hcmusthinhcode2k2/WeatherStation_Thesis/Docs/Images/1b0e72e8-8784-49f9-9e78-873ca0ad76dc.png

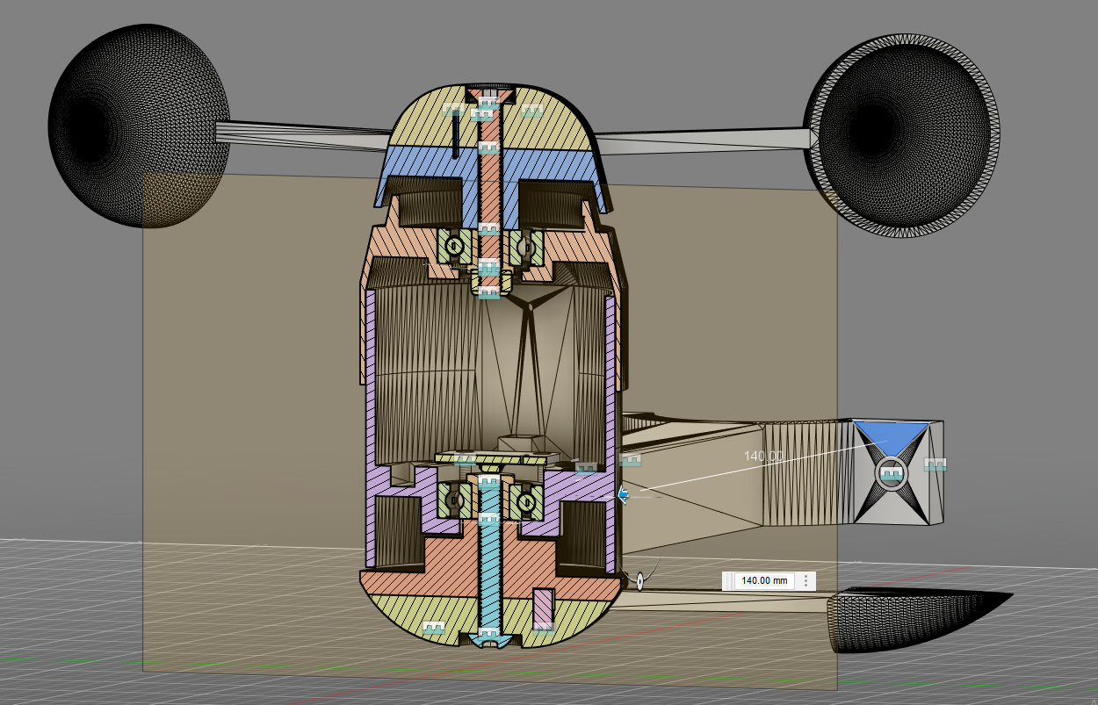
Docs/Images/1b0e72e8-8784-49f9-9e78-873ca0ad76dc.png
