hcmusthinhcode2k2/WeatherStation_Thesis/Docs/Images/2f302a85-7f2c-48bd-ab72-bc9634dedcbf.png

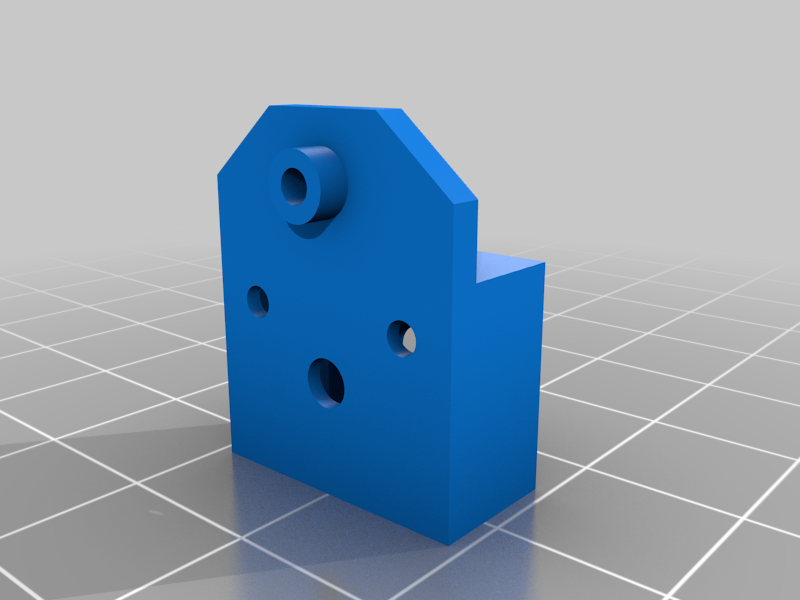
Docs/Images/2f302a85-7f2c-48bd-ab72-bc9634dedcbf.png
