hcmusthinhcode2k2/WeatherStation_Thesis/Docs/Images/3e30936f-f37a-4110-baf6-09b9fe7c85cc.png

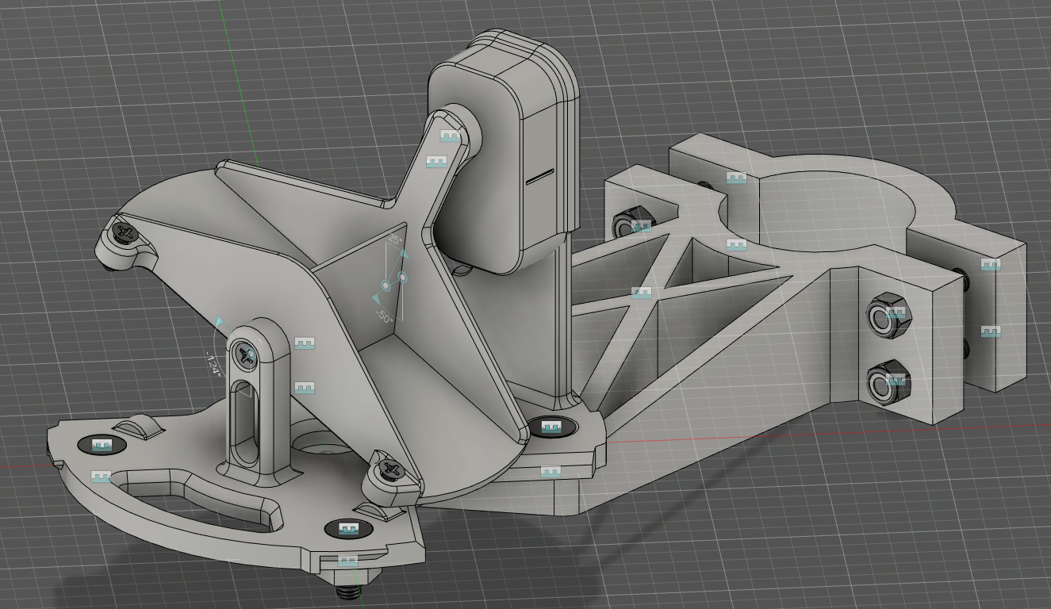
Docs/Images/3e30936f-f37a-4110-baf6-09b9fe7c85cc.png
