hcmusthinhcode2k2/WeatherStation_Thesis/Docs/Images/6b6d25d0-493b-4c5d-b1c7-931fbae90489.png

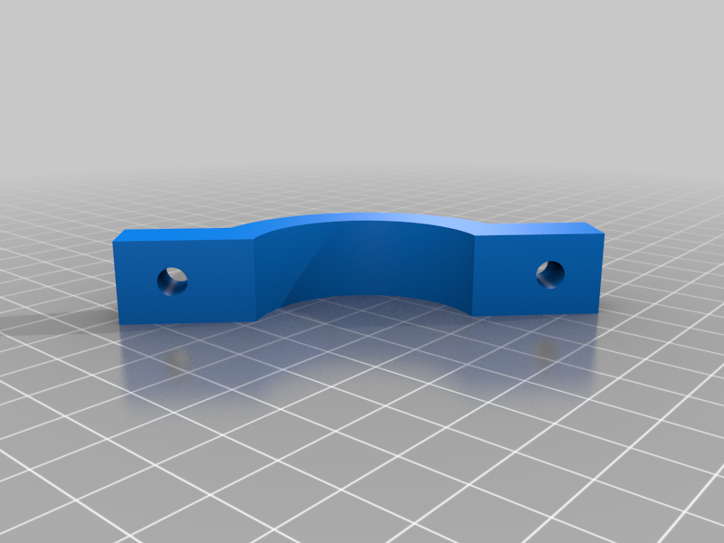
Docs/Images/6b6d25d0-493b-4c5d-b1c7-931fbae90489.png
