hcmusthinhcode2k2/WeatherStation_Thesis/Docs/Images/64f7d702-b31b-4c6c-b1bf-0f5daace0e0c.png

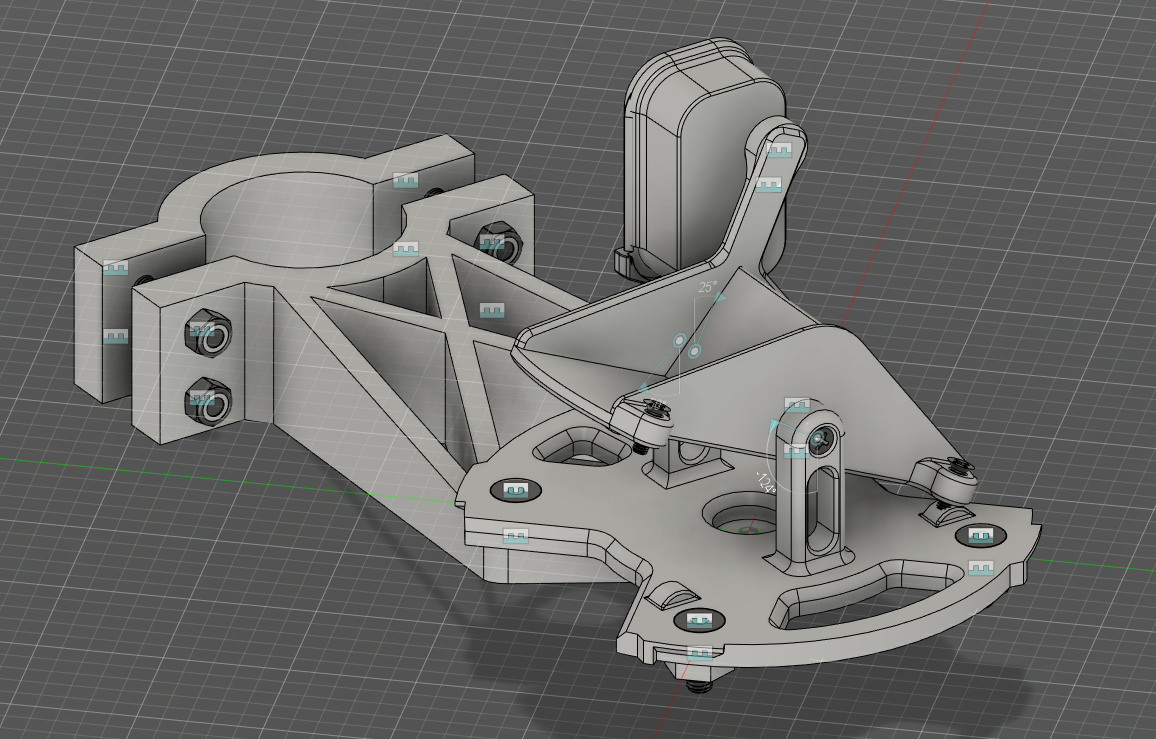
Docs/Images/64f7d702-b31b-4c6c-b1bf-0f5daace0e0c.png
