hcmusthinhcode2k2/WeatherStation_Thesis/Docs/Images/68ed1a44-c36f-472e-b6a4-fc436cf54907.PNG

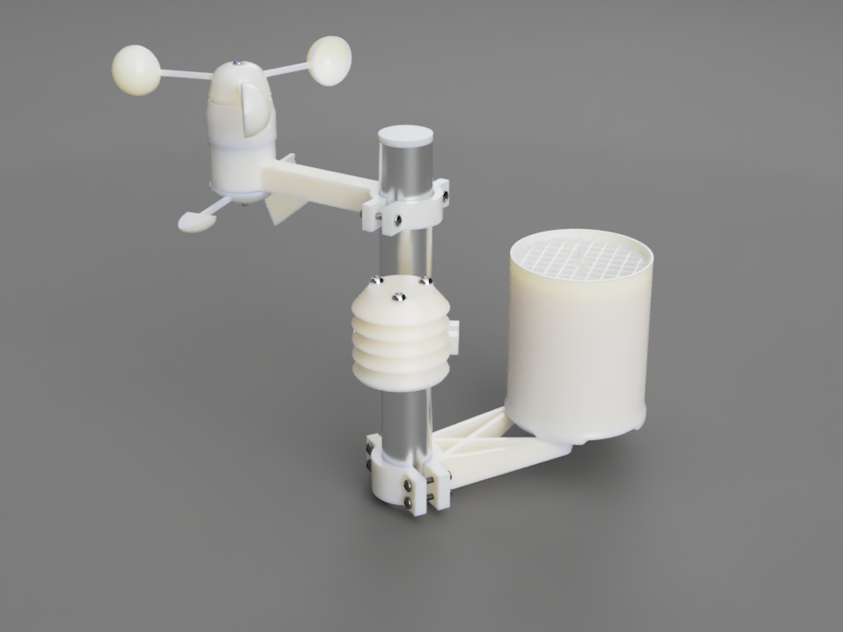
Docs/Images/68ed1a44-c36f-472e-b6a4-fc436cf54907.PNG
