hcmusthinhcode2k2/WeatherStation_Thesis/Docs/Images/645dd349-c03a-4ee8-80c0-8387001d7b49.png

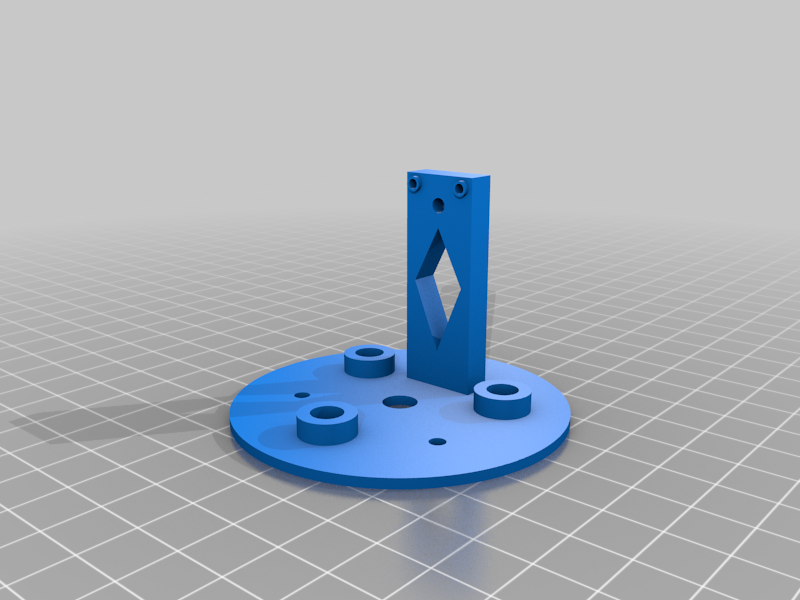
Docs/Images/645dd349-c03a-4ee8-80c0-8387001d7b49.png
