hcmusthinhcode2k2/WeatherStation_Thesis/Docs/Images/985cce32-4516-4d66-b6d8-986ed9bc3f87.png

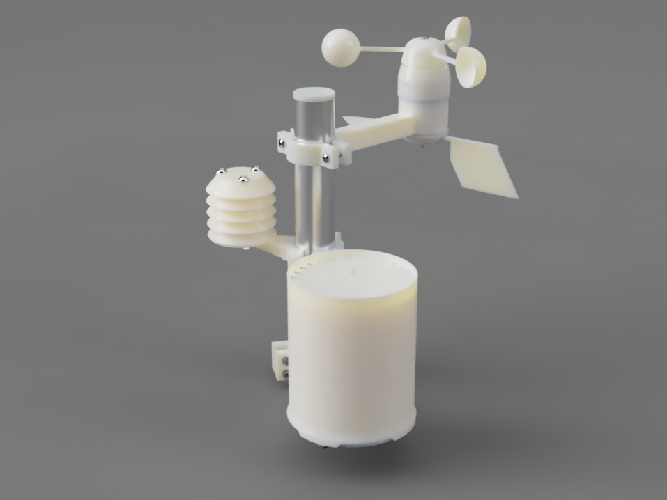
Docs/Images/985cce32-4516-4d66-b6d8-986ed9bc3f87.png
