hcmusthinhcode2k2/WeatherStation_Thesis/Docs/Images/32318.jpg

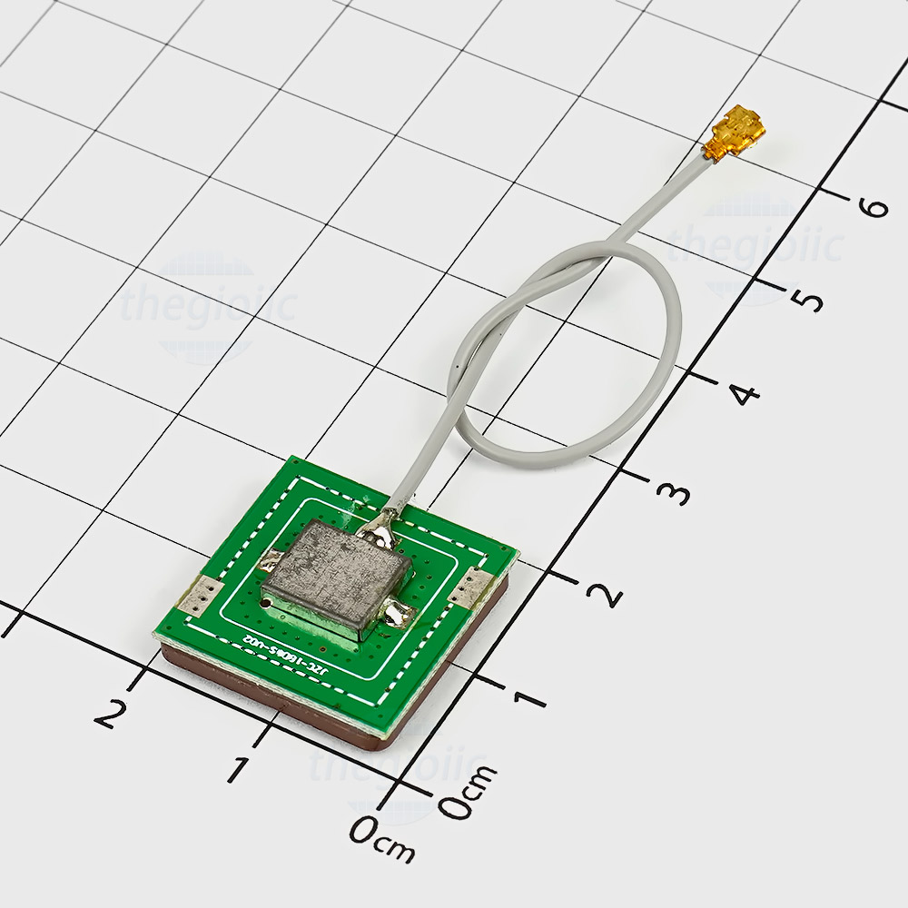
Docs/Images/32318.jpg
