hcmusthinhcode2k2/WeatherStation_Thesis/Docs/Images/a2c3049a-74b5-474f-aa45-c427f0820a80.png

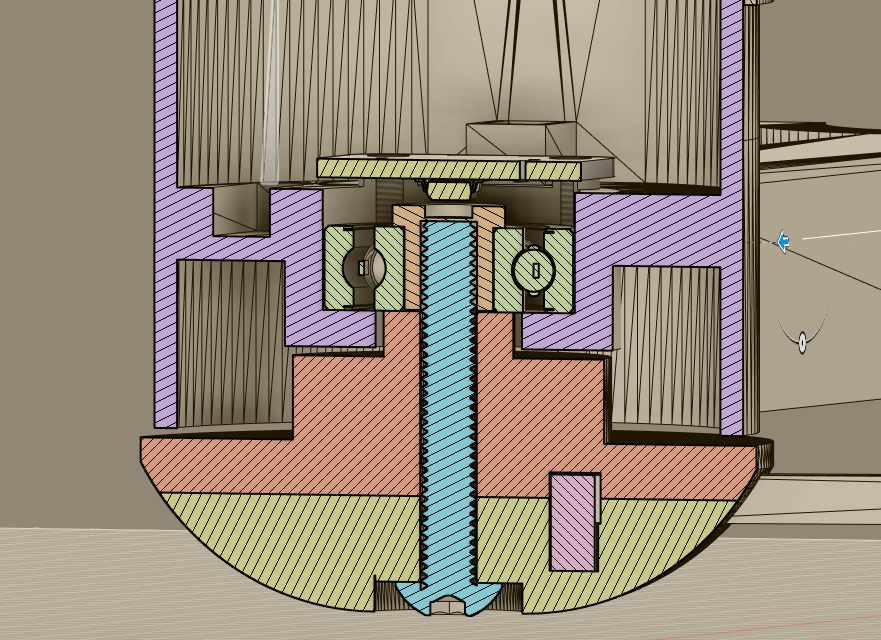
Docs/Images/a2c3049a-74b5-474f-aa45-c427f0820a80.png
