hcmusthinhcode2k2/WeatherStation_Thesis/Docs/Images/afb9a49a-6707-486c-9c42-9a4db6bc618d.png

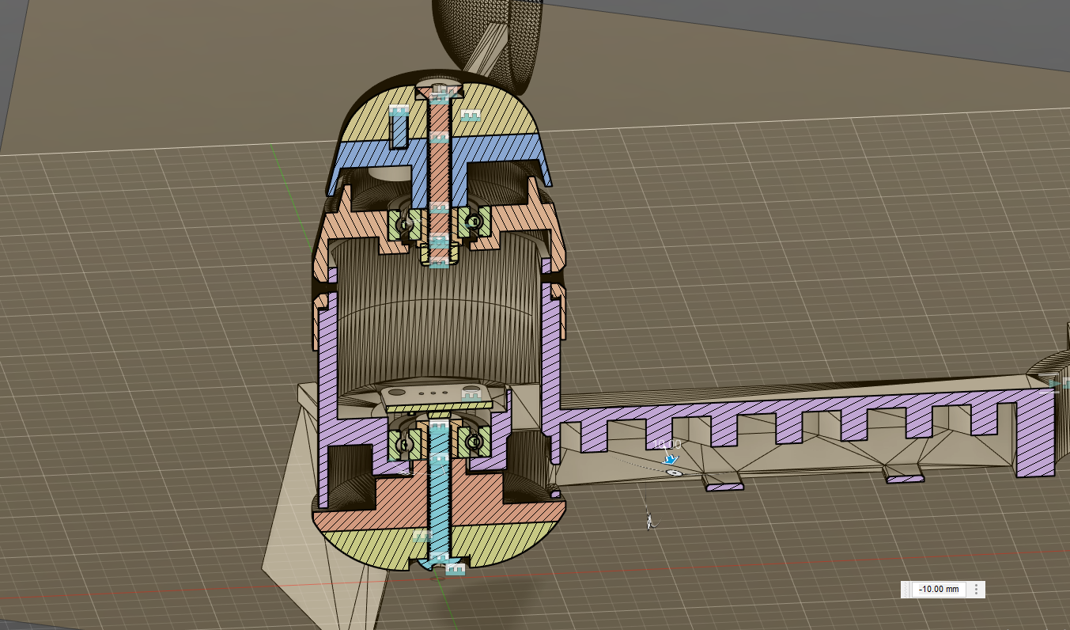
Docs/Images/afb9a49a-6707-486c-9c42-9a4db6bc618d.png
