hcmusthinhcode2k2/WeatherStation_Thesis/Docs/Images/d9b64d6f-a50a-4adc-8f70-32a4585b2f64.png

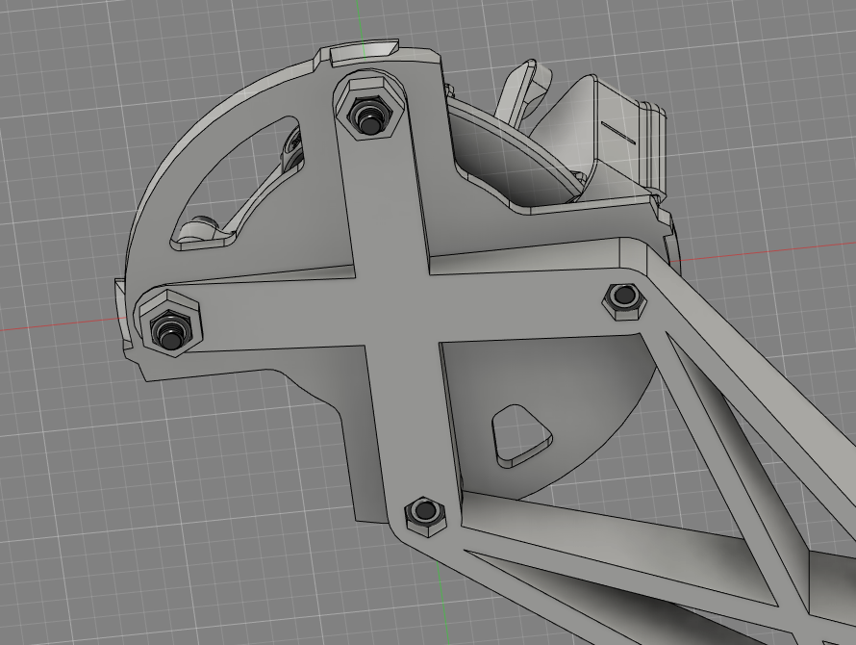
Docs/Images/d9b64d6f-a50a-4adc-8f70-32a4585b2f64.png
