hcmusthinhcode2k2/WeatherStation_Thesis/Docs/Images/e0c8014d-c326-444c-a0a5-c2a14836fae6.png

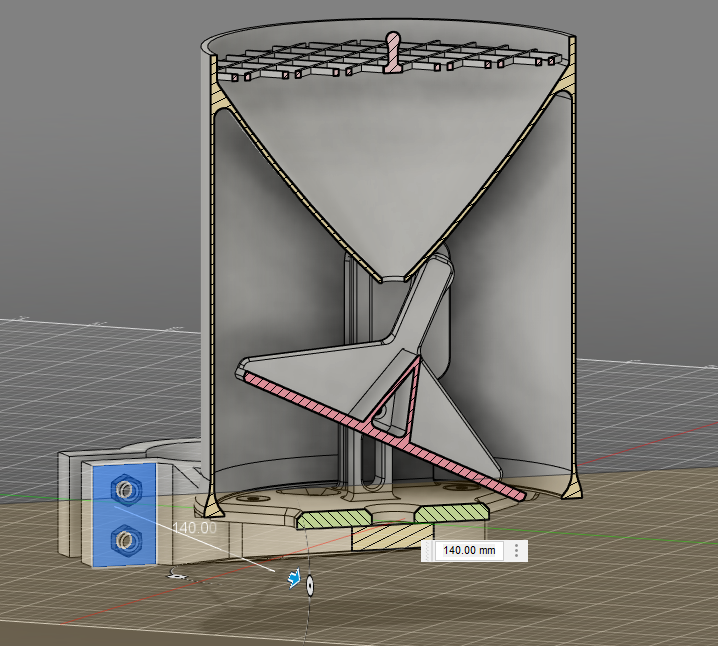
Docs/Images/e0c8014d-c326-444c-a0a5-c2a14836fae6.png
