hcmusthinhcode2k2/WeatherStation_Thesis/Docs/Images/RainSensor.png

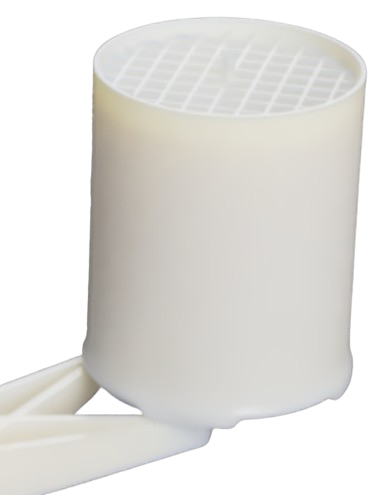
Docs/Images/RainSensor.png
