hcmusthinhcode2k2/WeatherStation_Thesis/Docs/Images/sOLAR.png

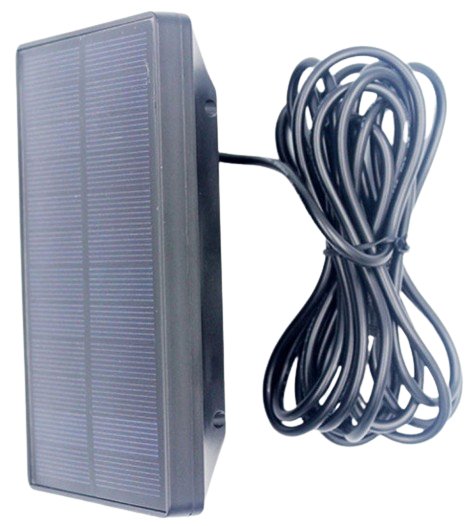
Docs/Images/sOLAR.png
