hcmusthinhcode2k2/WeatherStation_Thesis/Docs/Images/trokhangJLPCB.png

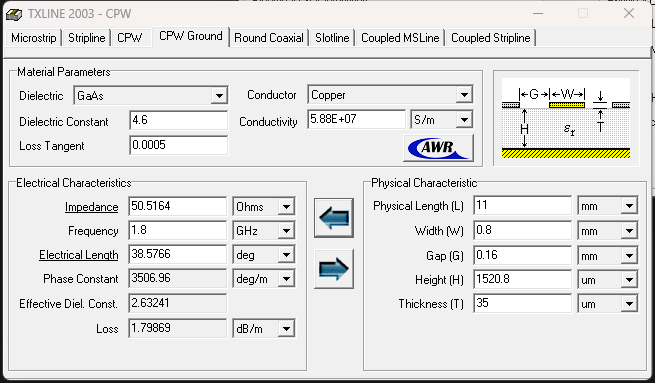
Docs/Images/trokhangJLPCB.png
