hcmusthinhcode2k2/WeatherStation_Thesis/Docs/Images/USBC.png

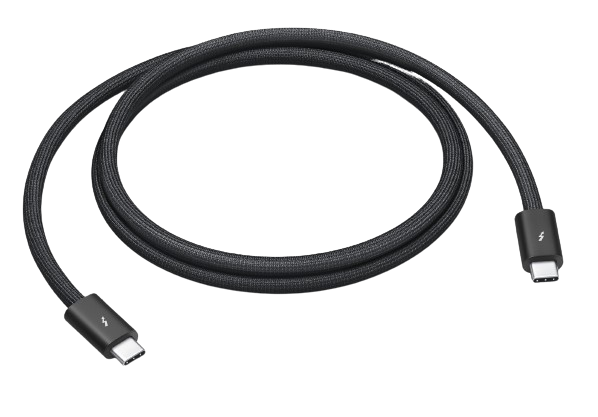
Docs/Images/USBC.png
