hcmusthinhcode2k2/WeatherStation_Thesis/Docs/Images/WindSensor.png

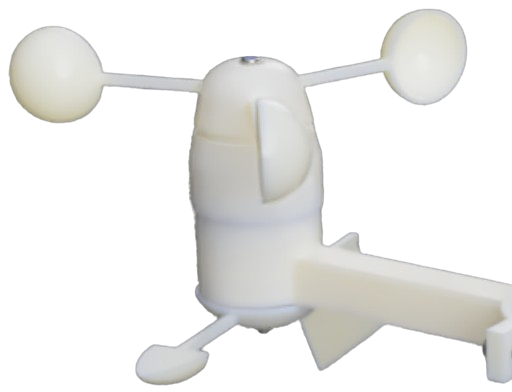
Docs/Images/WindSensor.png
