hcmusthinhcode2k2/WeatherStation_Thesis/Production/DHTP/Images/Bot.png

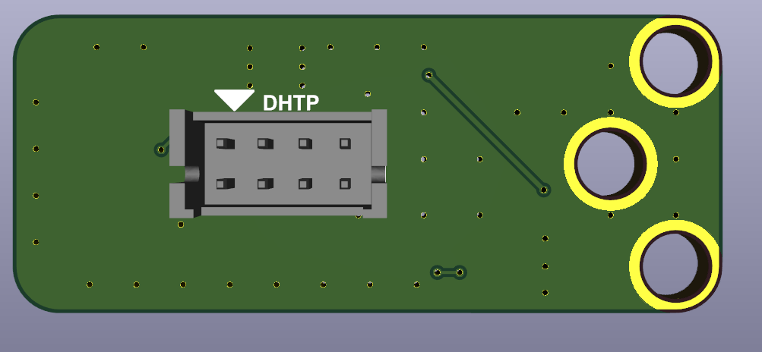
Production/DHTP/Images/Bot.png
