hcmusthinhcode2k2/WeatherStation_Thesis/Production/DHTP/Images/Top.png

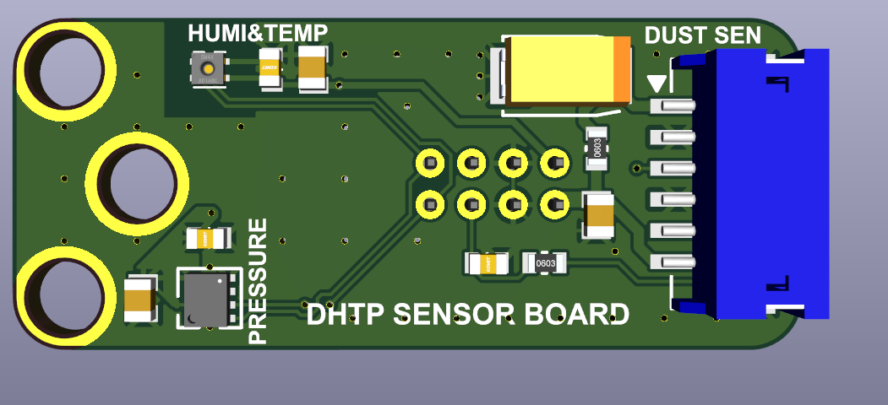
Production/DHTP/Images/Top.png
