hcmusthinhcode2k2/WeatherStation_Thesis/Production/Main-Sen/Pictures/Bot.png

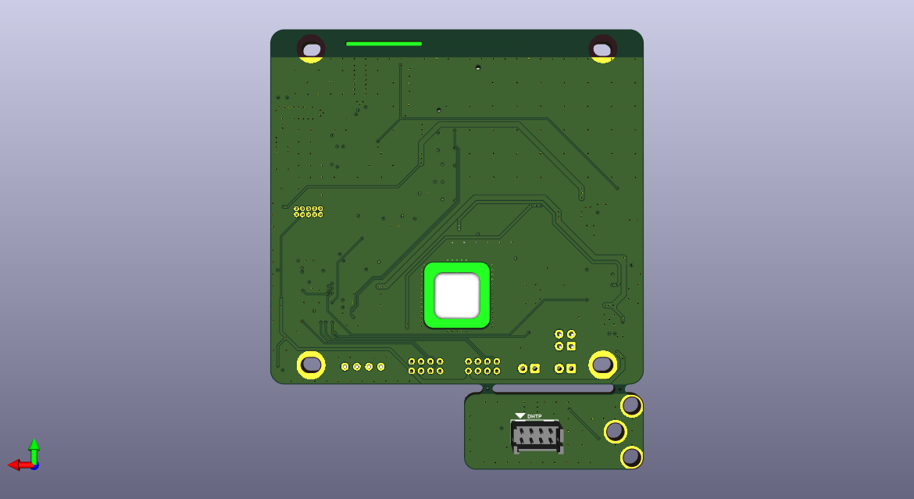
Production/Main-Sen/Pictures/Bot.png
