hcmusthinhcode2k2/WeatherStation_Thesis/Hardware/Model3D/XH2.54-4P.step

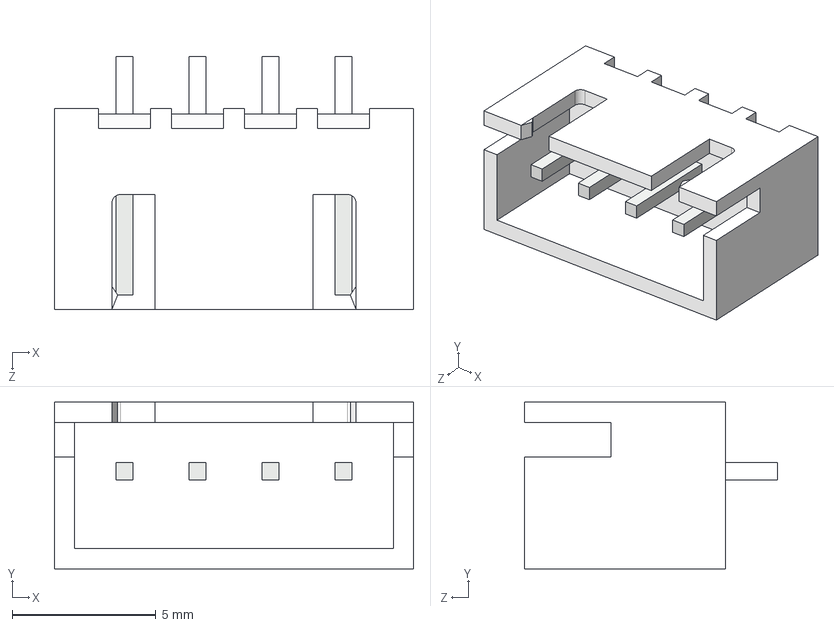
[picture p65: CAD file, 2024-08-14]
Hardware/Model3D/XH2.54-4P.step
12.5 x 5.80 x 8.80 mm
