hcmusthinhcode2k2/WeatherStation_Thesis/Production/Enclosure/Sensor_Hub_Shield_2.stl

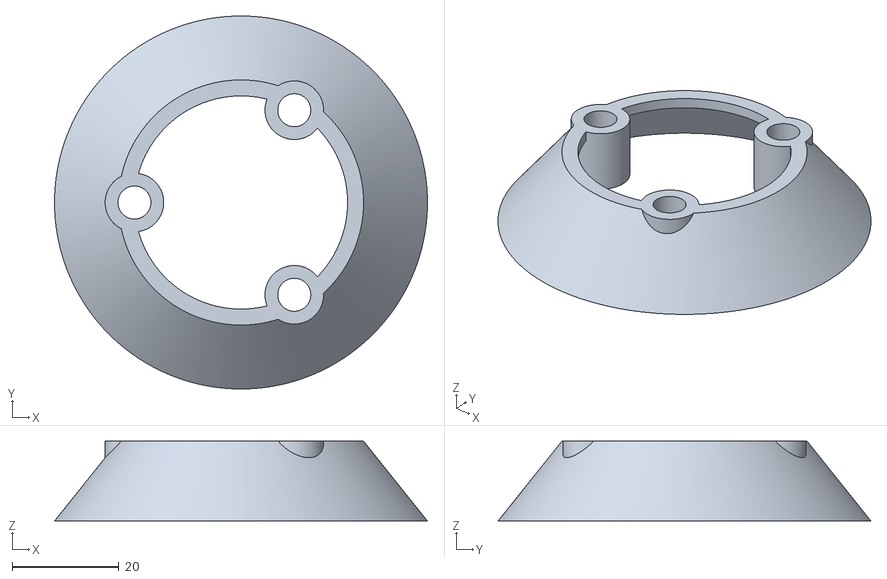
[picture p66: CAD file, 2024-08-14]
Production/Enclosure/Sensor_Hub_Shield_2.stl
70.0 x 70.0 x 15.0
