hcmusthinhcode2k2/WeatherStation_Thesis/Hardware/Model3D/SOT23-3.step

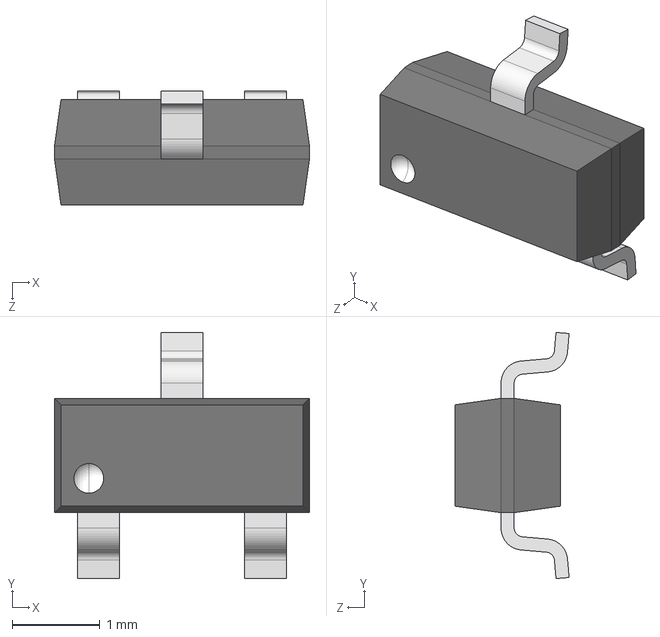
[picture p67: CAD file, 2024-08-14]
Hardware/Model3D/SOT23-3.step
2.90 x 2.80 x 1.30 mm
