hcmusthinhcode2k2/WeatherStation_Thesis/Hardware/Model3D/CSYTAL-MC146.step

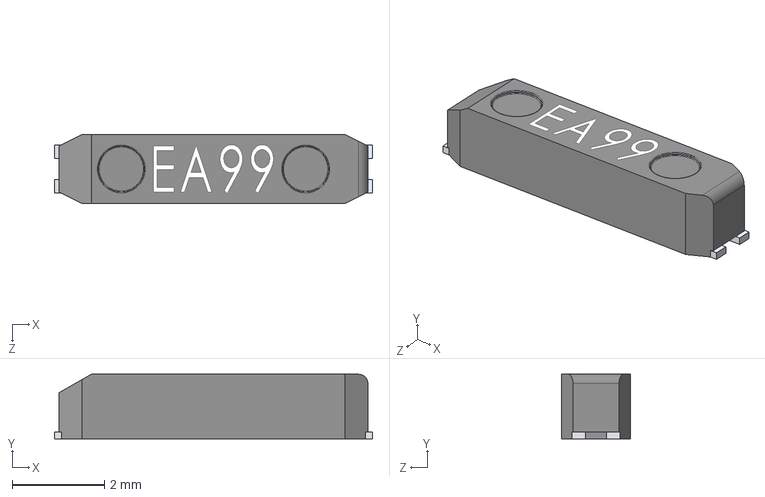
[picture p68: CAD file, 2024-08-14]
Hardware/Model3D/CSYTAL-MC146.step
6.90 x 1.40 x 1.50 mm
