hcmusthinhcode2k2/WeatherStation_Thesis/Production/Enclosure/Anemo_top_-_Cap.stl

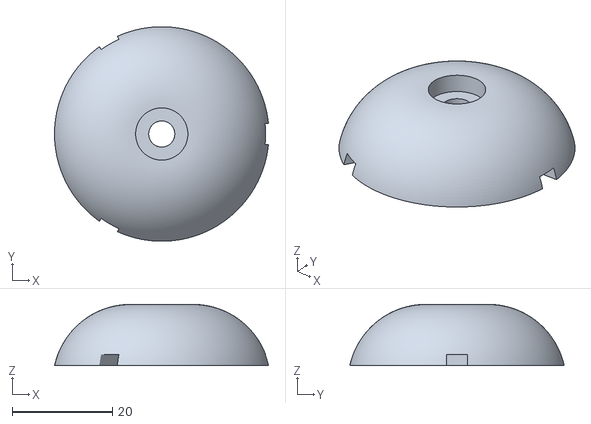
[picture p69: CAD file, 2024-08-14]
Production/Enclosure/Anemo_top_-_Cap.stl
42.6 x 42.7 x 12.2
