hcmusthinhcode2k2/WeatherStation_Thesis/Hardware/Model3D/PH2-04-UA.step

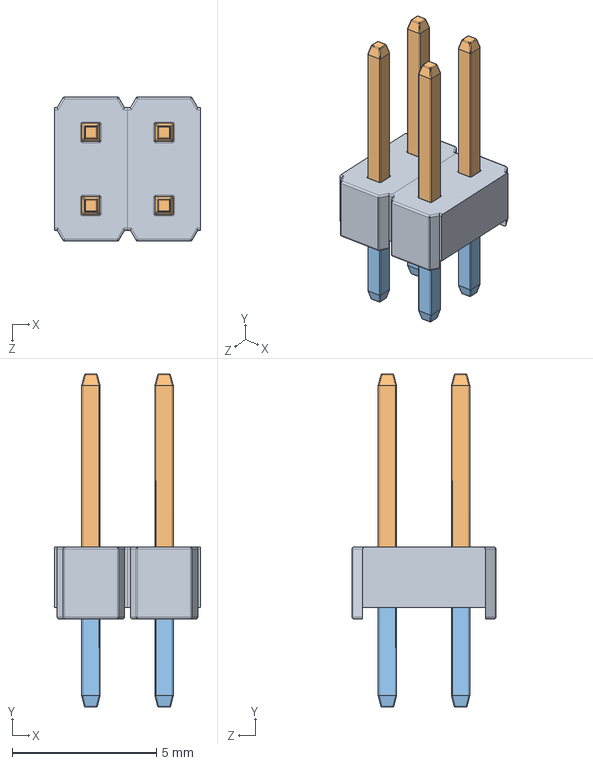
[picture p70: CAD file, 2024-08-14]
Hardware/Model3D/PH2-04-UA.step
5.08 x 11.6 x 5.00 mm
