hcmusthinhcode2k2/WeatherStation_Thesis/Production/Enclosure/Pluvio-Base_holder_V2.stl

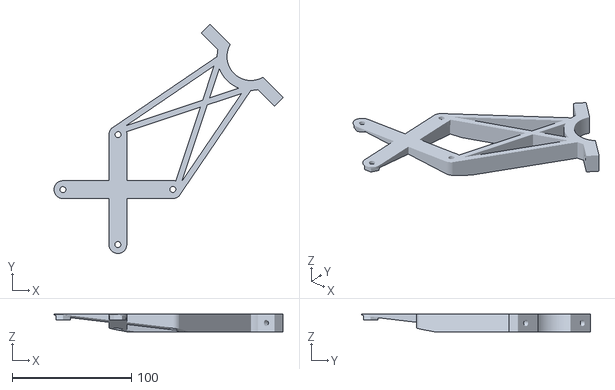
[picture p71: CAD file, 2024-08-14]
Production/Enclosure/Pluvio-Base_holder_V2.stl
191.8 x 191.8 x 15.0
