hcmusthinhcode2k2/WeatherStation_Thesis/Hardware/Model3D/B052VWVN-RC.step

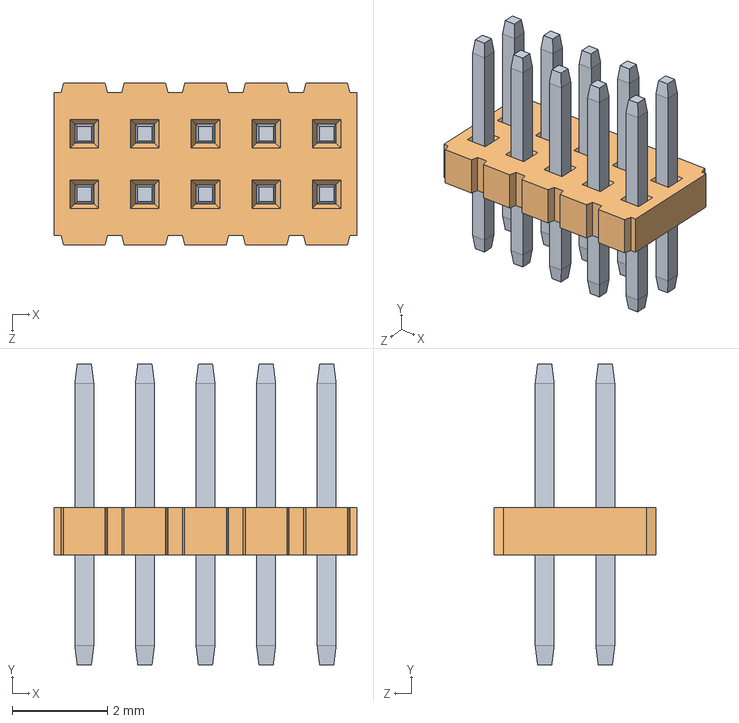
[picture p72: CAD file, 2024-08-14]
Hardware/Model3D/B052VWVN-RC.step
6.35 x 6.30 x 3.40 mm
