hcmusthinhcode2k2/WeatherStation_Thesis/Production/Enclosure/Anemo_bottom-Wing.stl

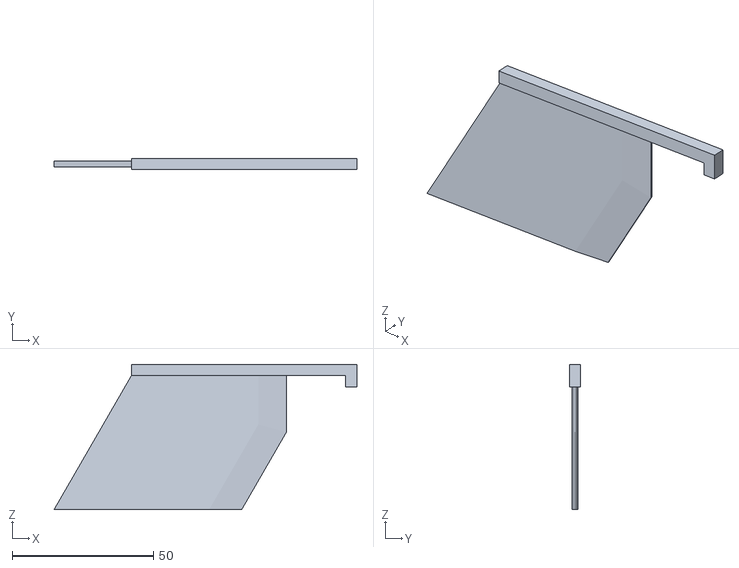
[picture p73: CAD file, 2024-08-14]
Production/Enclosure/Anemo_bottom-Wing.stl
107.4 x 4.00 x 51.5
