hcmusthinhcode2k2/WeatherStation_Thesis/Hardware/Model3D/DO-214AC.step

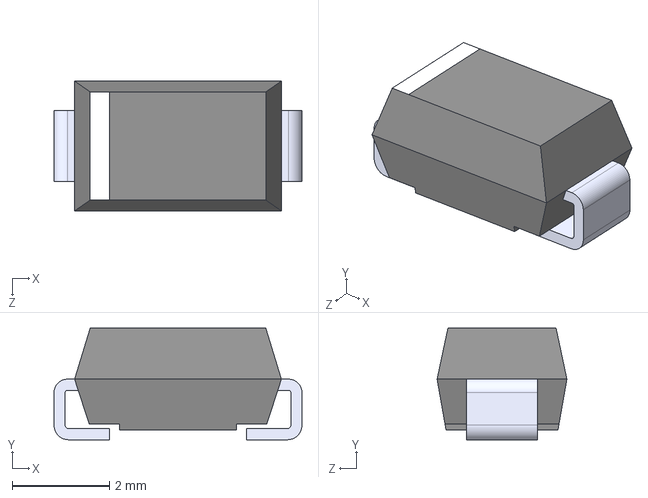
[picture p74: CAD file, 2024-08-14]
Hardware/Model3D/DO-214AC.step
5.09 x 2.29 x 2.67 mm
