hcmusthinhcode2k2/WeatherStation_Thesis/Production/Enclosure/De.dxf

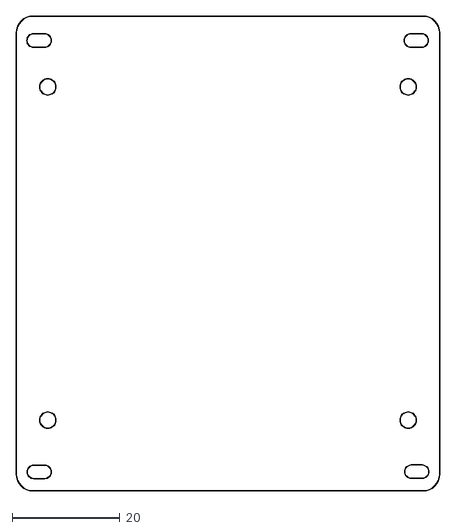
[picture p75: CAD file, 2024-08-14]
Production/Enclosure/De.dxf
78.5 x 88.0
