hcmusthinhcode2k2/WeatherStation_Thesis/Hardware/Model3D/HDM-2x4x2.0-TH.stp

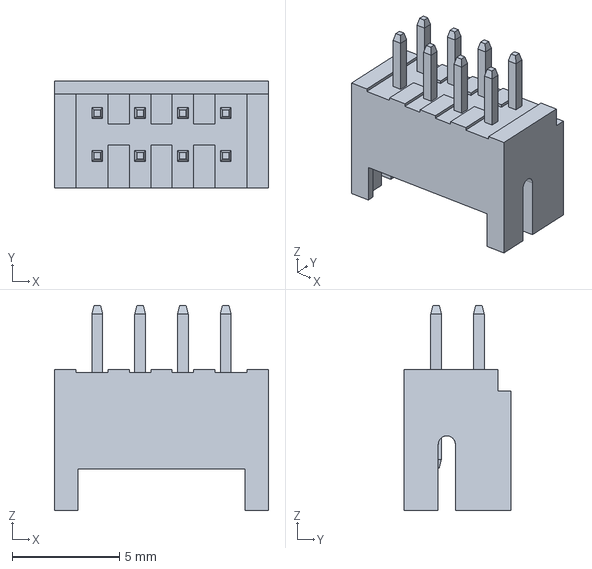
[picture p76: CAD file, 2024-08-14]
Hardware/Model3D/HDM-2x4x2.0-TH.stp
10.0 x 5.00 x 9.60 mm
