hcmusthinhcode2k2/WeatherStation_Thesis/Production/Enclosure/Pluvio_sensor_Hub.stl

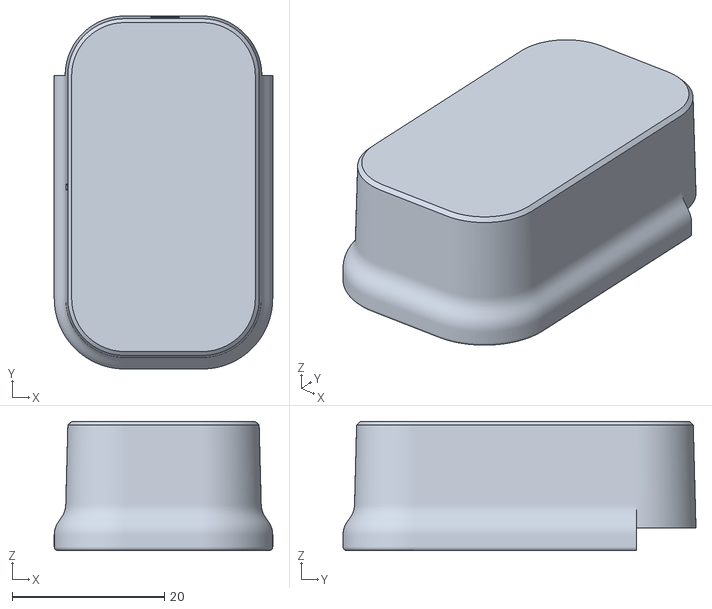
[picture p77: CAD file, 2024-08-14]
Production/Enclosure/Pluvio_sensor_Hub.stl
28.7 x 46.4 x 17.0
