hcmusthinhcode2k2/WeatherStation_Thesis/Hardware/Model3D/EVQ-PE105K_PNF05M_5PN05K.step

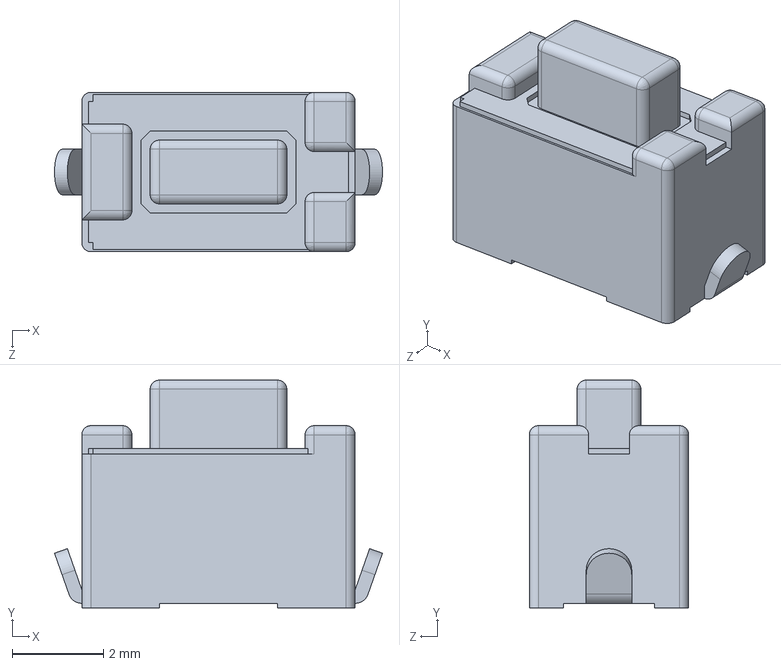
[picture p78: CAD file, 2024-08-14]
Hardware/Model3D/EVQ-PE105K_PNF05M_5PN05K.step
7.20 x 5.00 x 3.50 mm
