hcmusthinhcode2k2/WeatherStation_Thesis/Production/Enclosure/Anemo_bottom-Low_cap_FIXED.stl

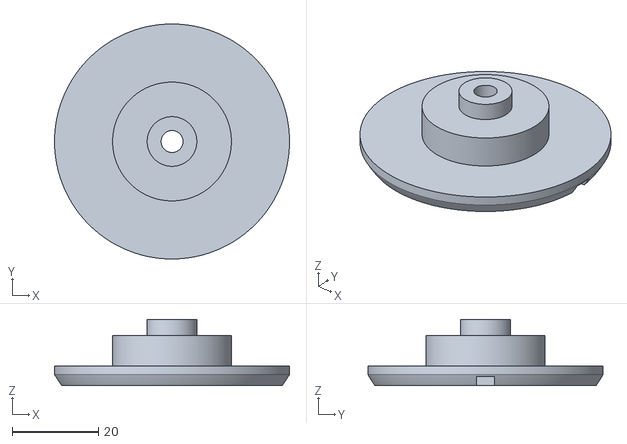
[picture p79: CAD file, 2024-08-14]
Production/Enclosure/Anemo_bottom-Low_cap_FIXED.stl
54.4 x 54.4 x 15.4
