hcmusthinhcode2k2/WeatherStation_Thesis/Hardware/Model3D/SOT363.step

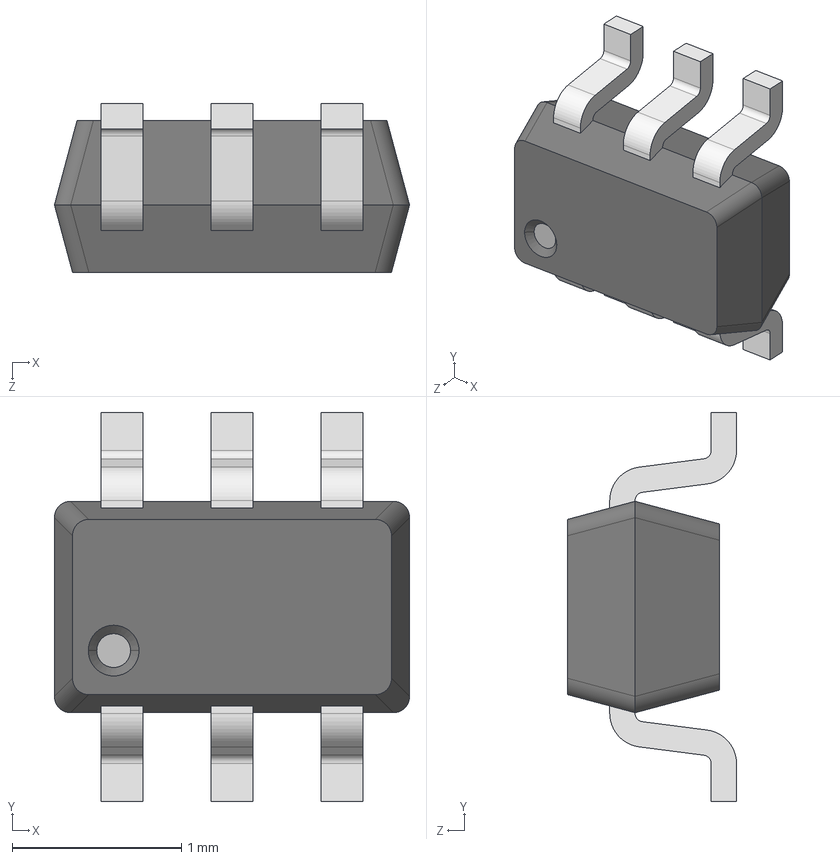
[picture p80: CAD file, 2024-08-14]
Hardware/Model3D/SOT363.step
2.10 x 2.30 x 1.00 mm
