hcmusthinhcode2k2/WeatherStation_Thesis/Production/Enclosure/Anemo_top_-_Base_FIXED.stl

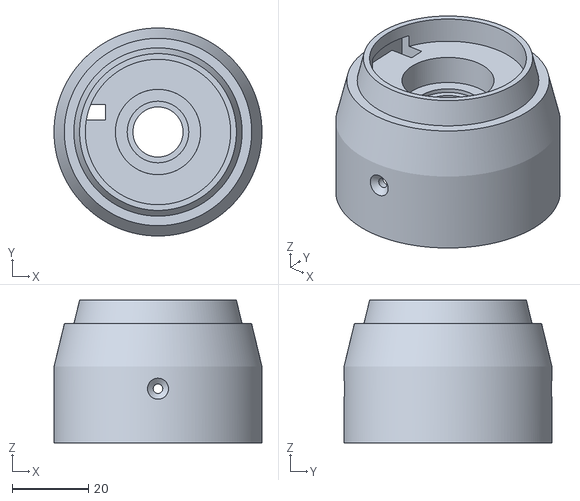
[picture p81: CAD file, 2024-08-14]
Production/Enclosure/Anemo_top_-_Base_FIXED.stl
54.4 x 54.4 x 37.4
