hcmusthinhcode2k2/WeatherStation_Thesis/Hardware/Model3D/IND0805.stp

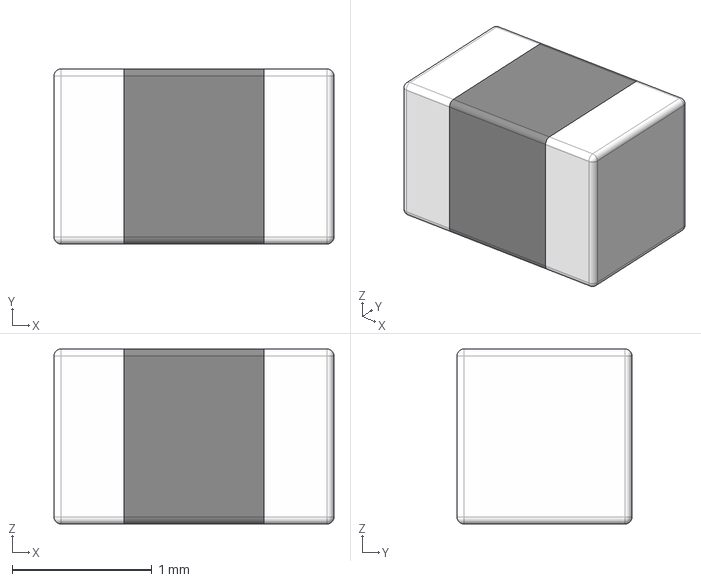
[picture p82: CAD file, 2024-08-14]
Hardware/Model3D/IND0805.stp
2.00 x 1.25 x 1.25 mm
Gehäuse
Kontaktfläche x 2
