hcmusthinhcode2k2/WeatherStation_Thesis/Hardware/Model3D/1575R-A.step

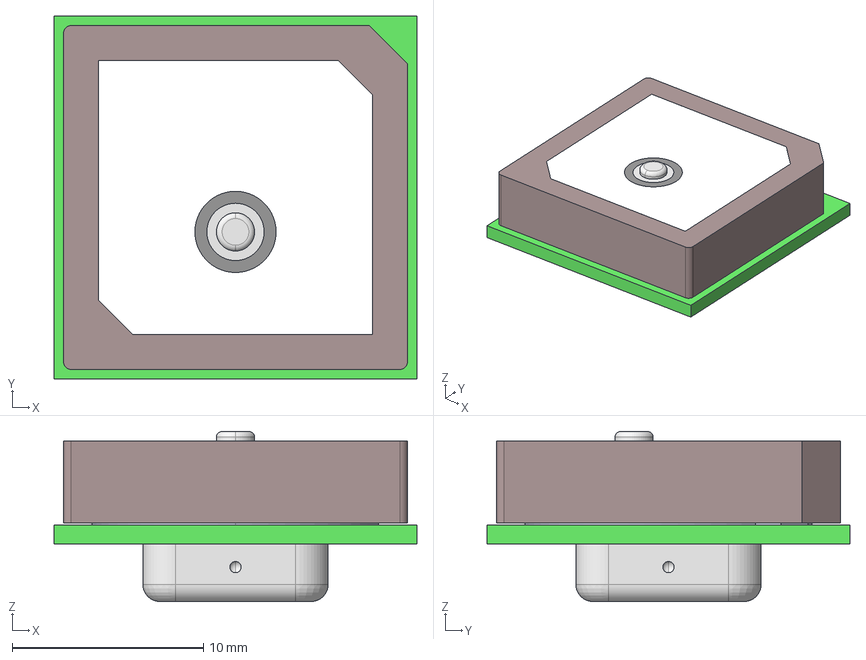
[picture p83: CAD file, 2024-08-14]
Hardware/Model3D/1575R-A.step
19.0 x 19.0 x 8.90 mm
Layer_1
=>[0:1:1:3]
=>[0:1:1:4]
=>[0:1:1:5]
=>[0:1:1:6]
=>[0:1:1:7]
=>[0:1:1:8]
=>[0:1:1:9]
