hcmusthinhcode2k2/WeatherStation_Thesis/Production/Enclosure/Anemo_top_-_Interrupter.stl

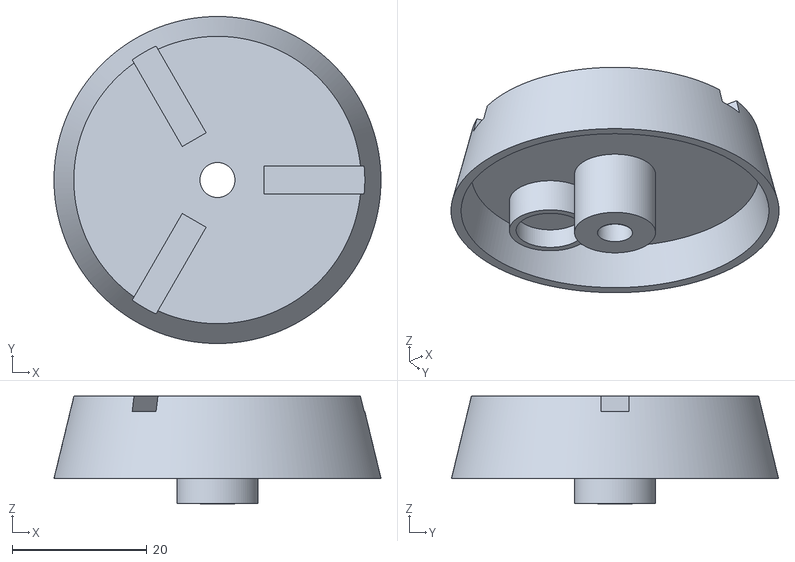
[picture p84: CAD file, 2024-08-14]
Production/Enclosure/Anemo_top_-_Interrupter.stl
48.6 x 48.6 x 16.0
