hcmusthinhcode2k2/WeatherStation_Thesis/Hardware/Model3D/SHT4x.step

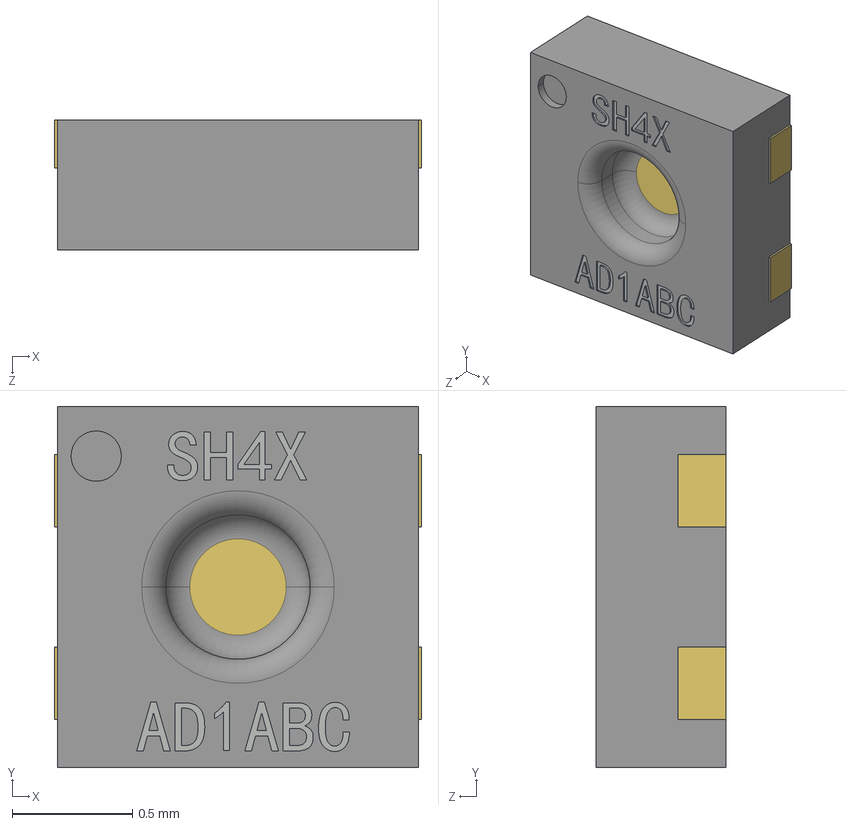
[picture p85: CAD file, 2024-08-14]
Hardware/Model3D/SHT4x.step
1.52 x 1.50 x 0.54 mm
