hcmusthinhcode2k2/WeatherStation_Thesis/Production/Enclosure/SH-First.stl

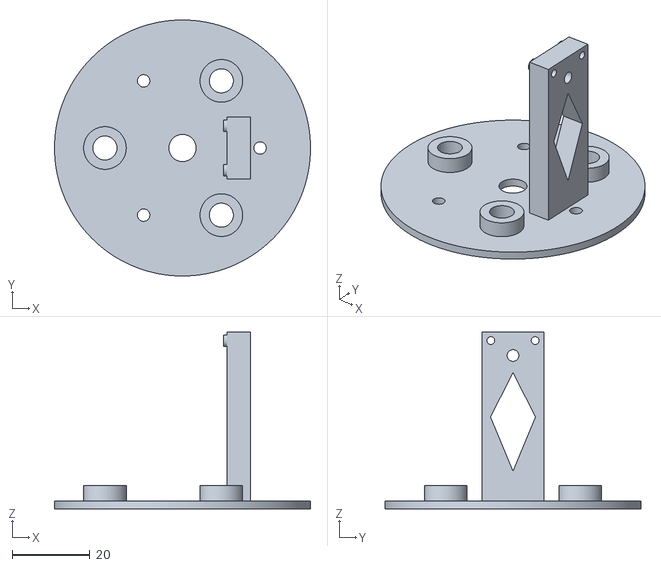
[picture p86: CAD file, 2024-08-14]
Production/Enclosure/SH-First.stl
66.0 x 66.0 x 45.5
