hcmusthinhcode2k2/WeatherStation_Thesis/Hardware/Model3D/SIM8051-6-0-14-01-X-REVD.step

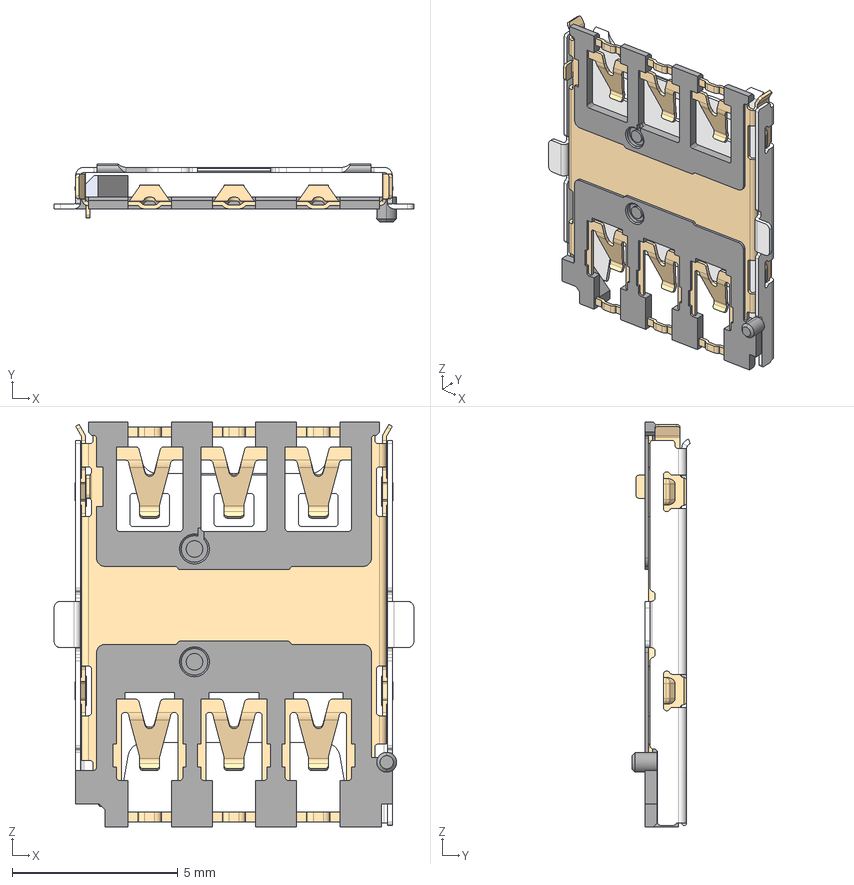
[picture p87: CAD file, 2024-08-14]
Hardware/Model3D/SIM8051-6-0-14-01-X-REVD.step
10.8 x 1.75 x 12.2 mm
