hcmusthinhcode2k2/WeatherStation_Thesis/Production/Enclosure/Pluvio_Case.stl

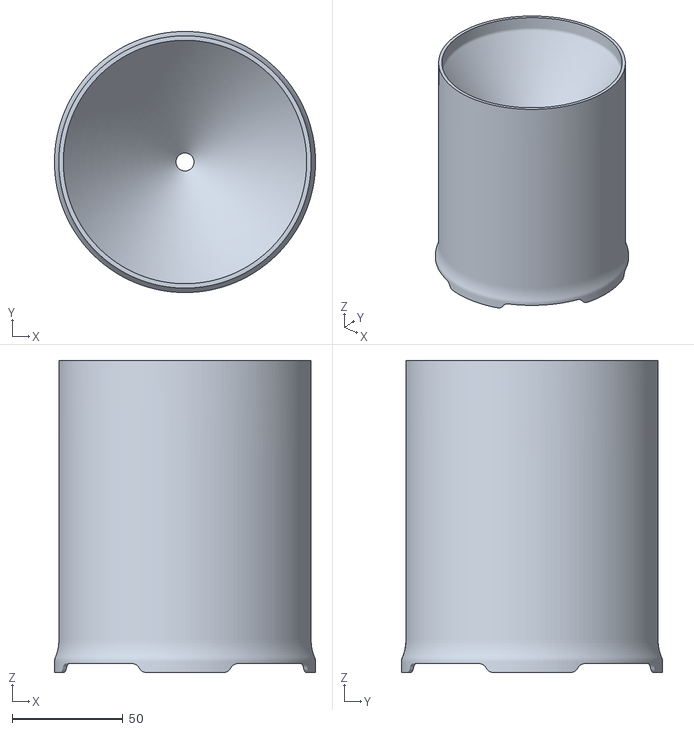
[picture p88: CAD file, 2024-08-14]
Production/Enclosure/Pluvio_Case.stl
118.0 x 118.0 x 141.0
