hcmusthinhcode2k2/WeatherStation_Thesis/Hardware/Model3D/U.FL.step

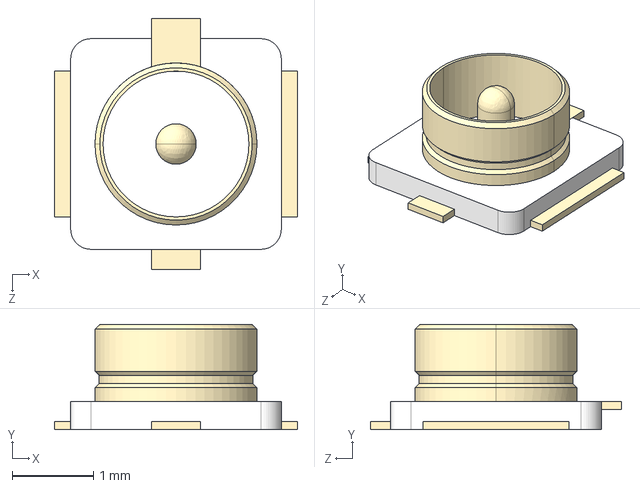
[picture p89: CAD file, 2024-08-14]
Hardware/Model3D/U.FL.step
3.00 x 1.30 x 3.10 mm
