hcmusthinhcode2k2/WeatherStation_Thesis/Production/Enclosure/Anemo_bottom-Tip.stl

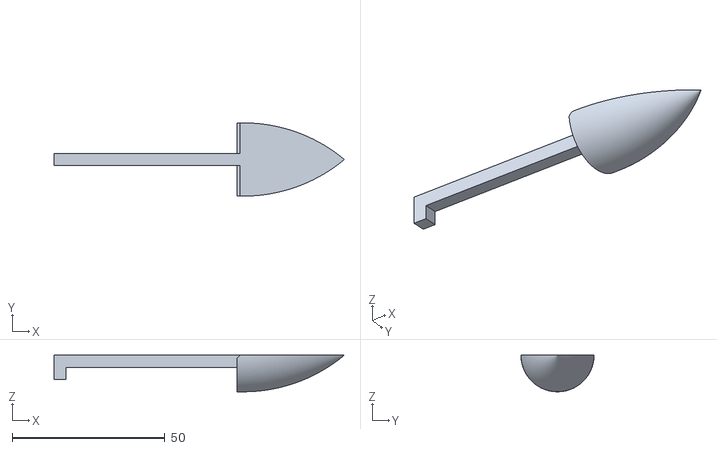
[picture p90: CAD file, 2024-08-14]
Production/Enclosure/Anemo_bottom-Tip.stl
95.0 x 24.0 x 12.0
