hcmusthinhcode2k2/WeatherStation_Thesis/Hardware/Model3D/LED_0603_WS.step

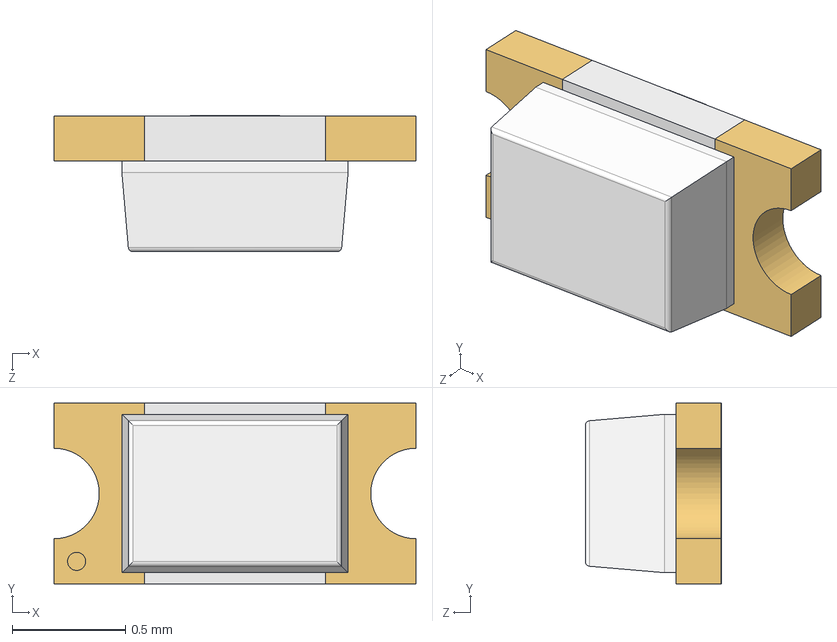
[picture p91: CAD file, 2024-08-14]
Hardware/Model3D/LED_0603_WS.step
1.60 x 0.8 x 0.602 mm
User Library-LED_0603_WS_Pocket002
User Library-LED_0603_WS_Pad004
User Library-LED_0603_WS_Fillet
User Library-LED_0603_WS_Pocket001
User Library-LED_0603_WS_Pad
