hcmusthinhcode2k2/WeatherStation_Thesis/Hardware/Model3D/IND0603.step

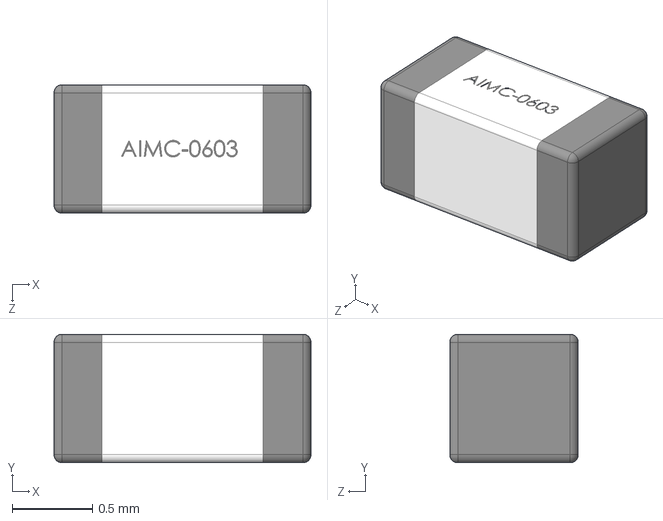
[picture p92: CAD file, 2024-08-14]
Hardware/Model3D/IND0603.step
1.60 x 0.8 x 0.8 mm
