hcmusthinhcode2k2/WeatherStation_Thesis/Production/Enclosure/Anemo_Backpole.stl

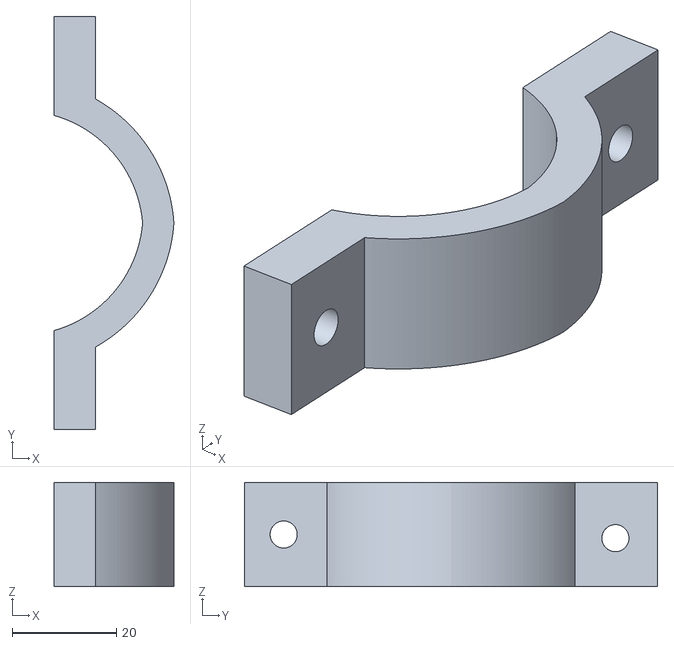
[picture p93: CAD file, 2024-08-14]
Production/Enclosure/Anemo_Backpole.stl
23.0 x 79.3 x 20.0
