hcmusthinhcode2k2/WeatherStation_Thesis/Hardware/Model3D/TQFP48.step

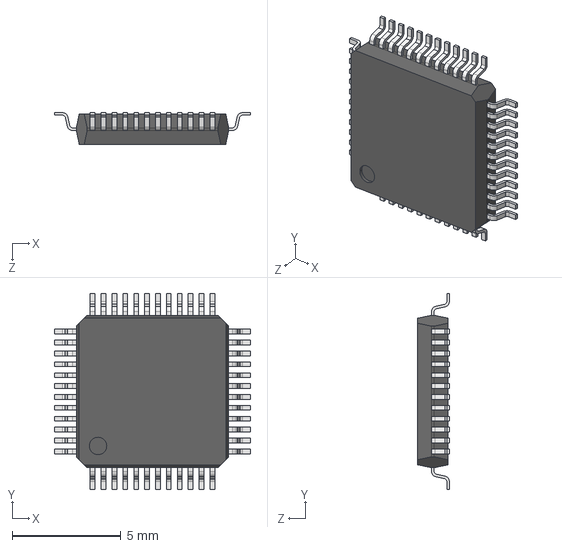
[picture p94: CAD file, 2024-08-14]
Hardware/Model3D/TQFP48.step
9.00 x 9.00 x 1.46 mm
User Library-TQFP-48_pins_TQFP_pin_TQFP_022x07_1 x 48
User Library-TQFP-48_body_10x1_TQFP_7x7_1
