hcmusthinhcode2k2/WeatherStation_Thesis/Production/Enclosure/Pluvio_Top_Mesh.stl

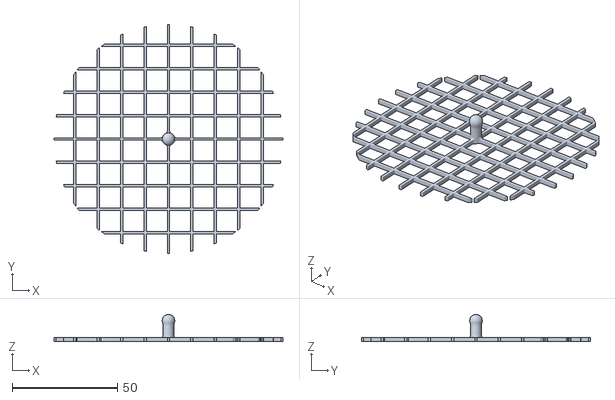
[picture p95: CAD file, 2024-08-14]
Production/Enclosure/Pluvio_Top_Mesh.stl
109.0 x 109.0 x 13.0
