hcmusthinhcode2k2/WeatherStation_Thesis/Hardware/Model3D/SHORTINGJUMPER.step

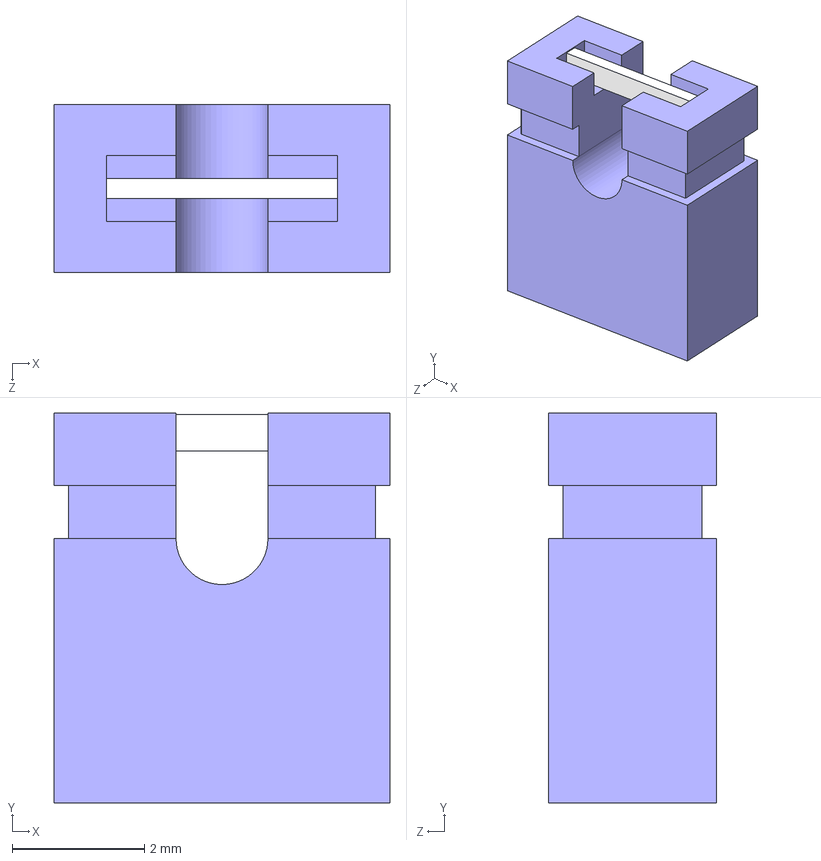
[picture p96: CAD file, 2024-08-14]
Hardware/Model3D/SHORTINGJUMPER.step
5.08 x 5.90 x 2.54 mm
