hcmusthinhcode2k2/WeatherStation_Thesis/Production/Enclosure/Sensor_Hub_Holder.stl

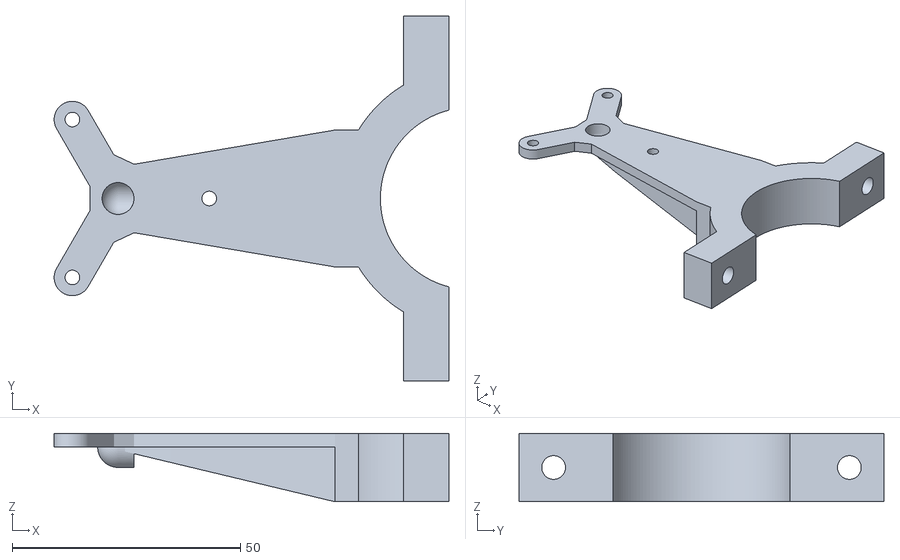
[picture p97: CAD file, 2024-08-14]
Production/Enclosure/Sensor_Hub_Holder.stl
86.5 x 80.0 x 15.0
