hcmusthinhcode2k2/WeatherStation_Thesis/Hardware/Model3D/PowerVQFN15_TI.stp

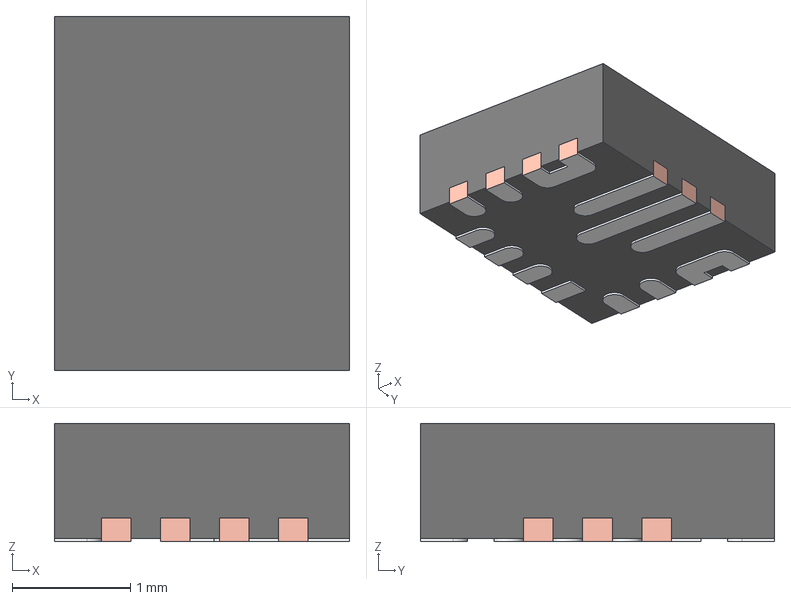
[picture p98: CAD file, 2024-08-14]
Hardware/Model3D/PowerVQFN15_TI.stp
2.50 x 3.00 x 1.00 mm
FRAME-RNM0015A
BODY-QFN
PIN1-ID
