hcmusthinhcode2k2/WeatherStation_Thesis/Production/Enclosure/SH-DHT_holder.stl

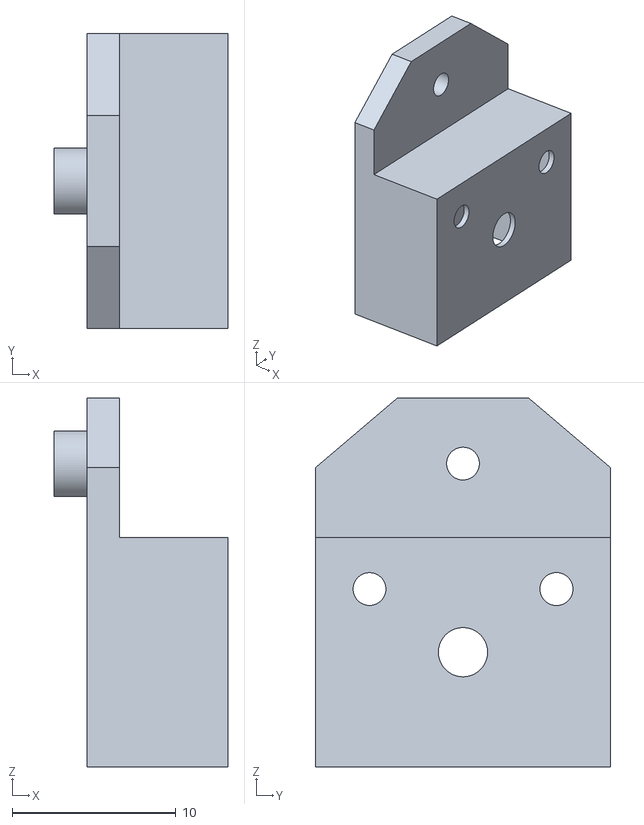
[picture p99: CAD file, 2024-08-14]
Production/Enclosure/SH-DHT_holder.stl
10.6 x 18.0 x 22.5
