hcmusthinhcode2k2/WeatherStation_Thesis/Hardware/Model3D/0805C.step

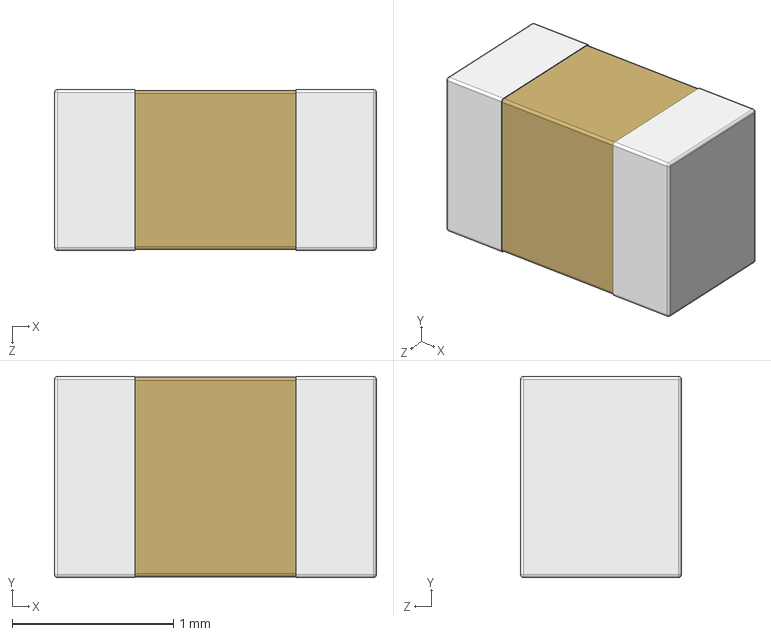
[picture p100: CAD file, 2024-08-14]
Hardware/Model3D/0805C.step
2.00 x 1.25 x 1.00 mm
