hcmusthinhcode2k2/WeatherStation_Thesis/Production/Enclosure/Pluvio-Backpole_V2.stl

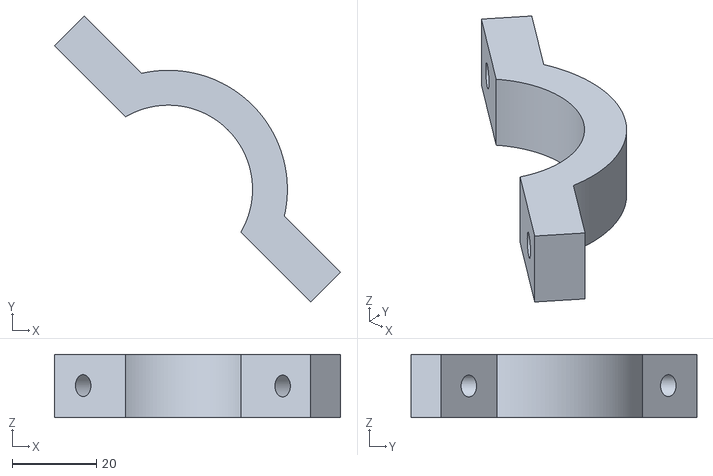
[picture p101: CAD file, 2024-08-14]
Production/Enclosure/Pluvio-Backpole_V2.stl
68.0 x 68.0 x 15.0
