hcmusthinhcode2k2/WeatherStation_Thesis/Hardware/Model3D/SOIC127P600X175-8N.step

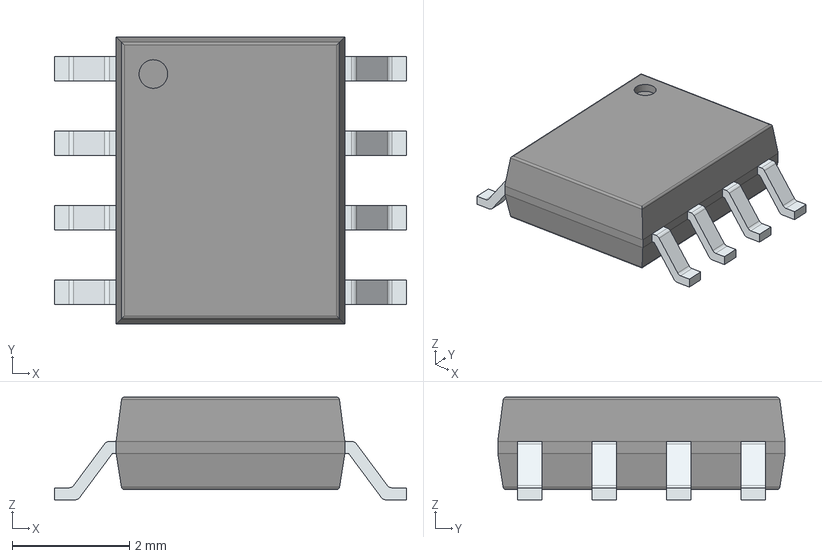
[picture p102: CAD file, 2024-08-14]
Hardware/Model3D/SOIC127P600X175-8N.step
6.00 x 4.90 x 1.75 mm
PinsArrayLR
