hcmusthinhcode2k2/WeatherStation_Thesis/Production/Enclosure/Sensor_Hub_Backpole.stl

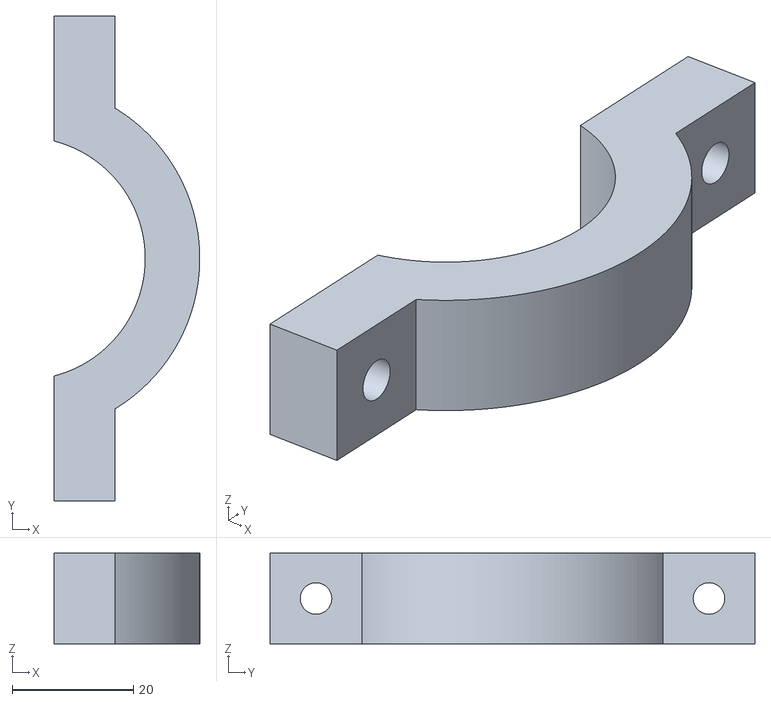
[picture p103: CAD file, 2024-08-14]
Production/Enclosure/Sensor_Hub_Backpole.stl
24.0 x 80.0 x 15.0
