hcmusthinhcode2k2/WeatherStation_Thesis/Hardware/Model3D/HDM-6x1.5-SMD-R.step

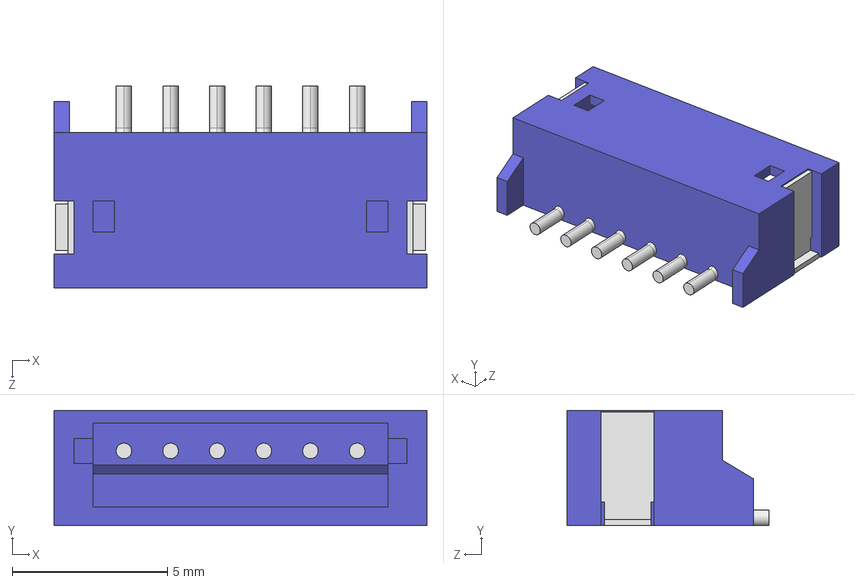
[picture p104: CAD file, 2024-08-14]
Hardware/Model3D/HDM-6x1.5-SMD-R.step
12.0 x 3.70 x 6.50 mm
