hcmusthinhcode2k2/WeatherStation_Thesis/Hardware/Model3D/QFN20-4x4x0.8MM.step

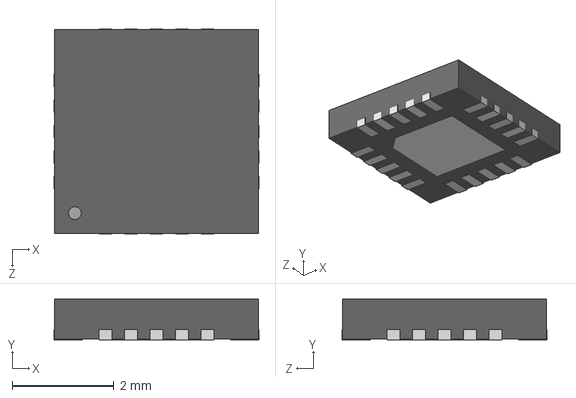
[picture p105: CAD file, 2024-08-14]
Hardware/Model3D/QFN20-4x4x0.8MM.step
4.02 x 0.8 x 4.02 mm
