hcmusthinhcode2k2/WeatherStation_Thesis/Hardware/Model3D/CAP2312-6032.step

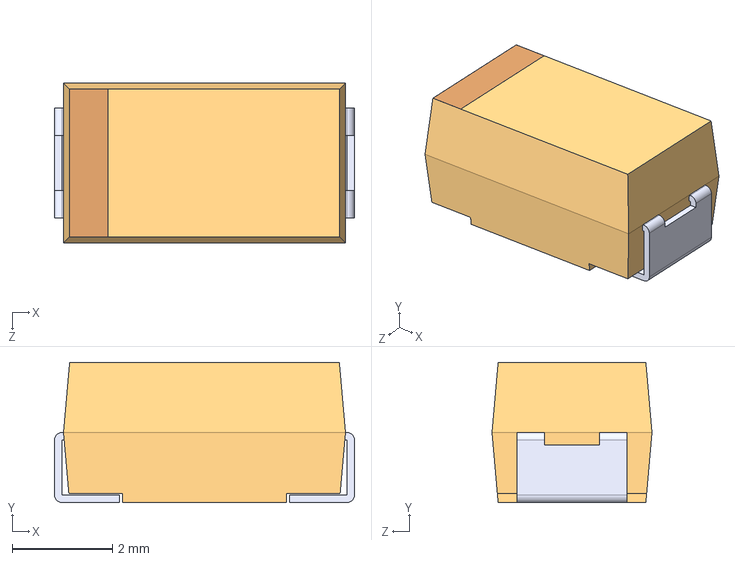
[picture p106: CAD file, 2024-08-14]
Hardware/Model3D/CAP2312-6032.step
6.00 x 2.80 x 3.20 mm
