hcmusthinhcode2k2/WeatherStation_Thesis/Hardware/Model3D/RES0603.step

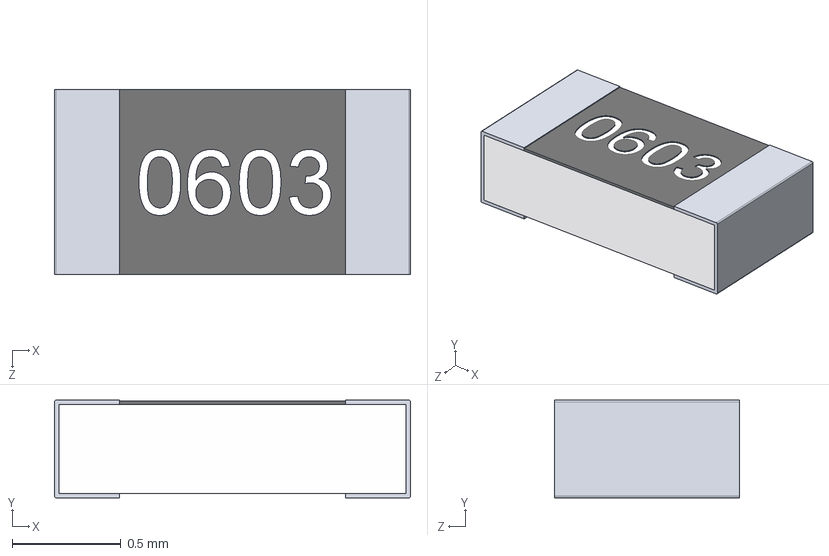
[picture p107: CAD file, 2024-08-14]
Hardware/Model3D/RES0603.step
1.64 x 0.45 x 0.85 mm
User Library-R SMD 0603_0603 BODY
User Library-R SMD 0603_0603 PAD x 2
User Library-R SMD 0603_0603 OPIS
