hcmusthinhcode2k2/WeatherStation_Thesis/Firmware/WS.X/Result.png

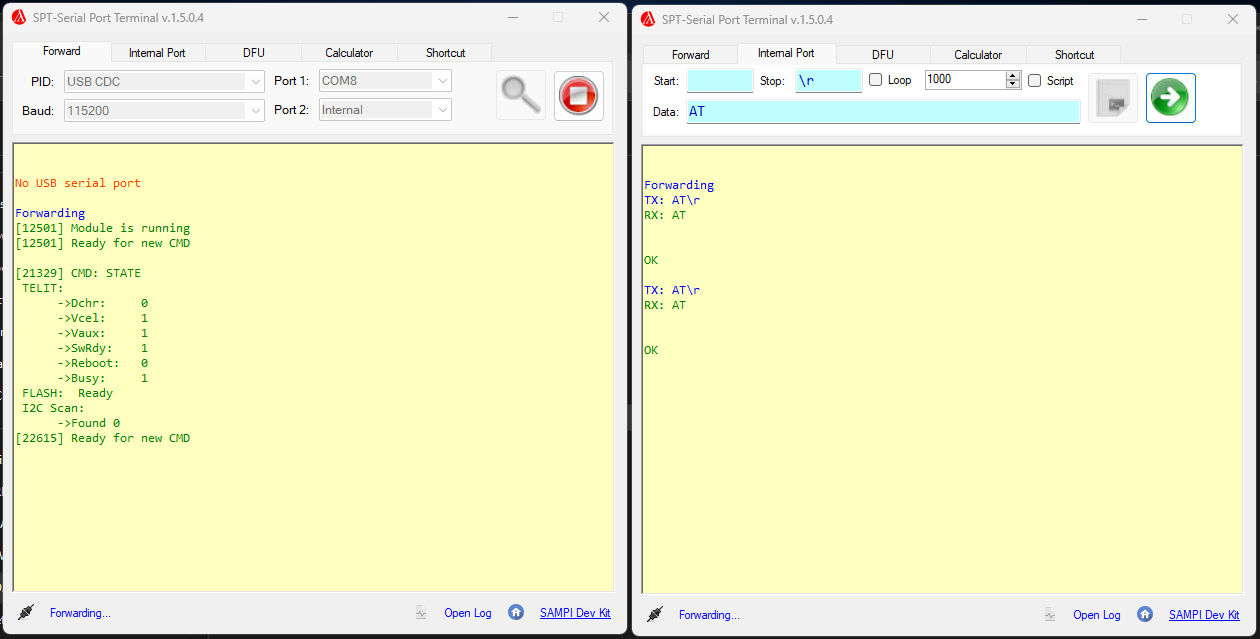
Firmware/WS.X/Result.png
