hcmusthinhcode2k2/WeatherStation_Thesis/Hardware/MCU.kicad_sch

## KiCad design Hardware/MCU.kicad_sch (2024-08-14)

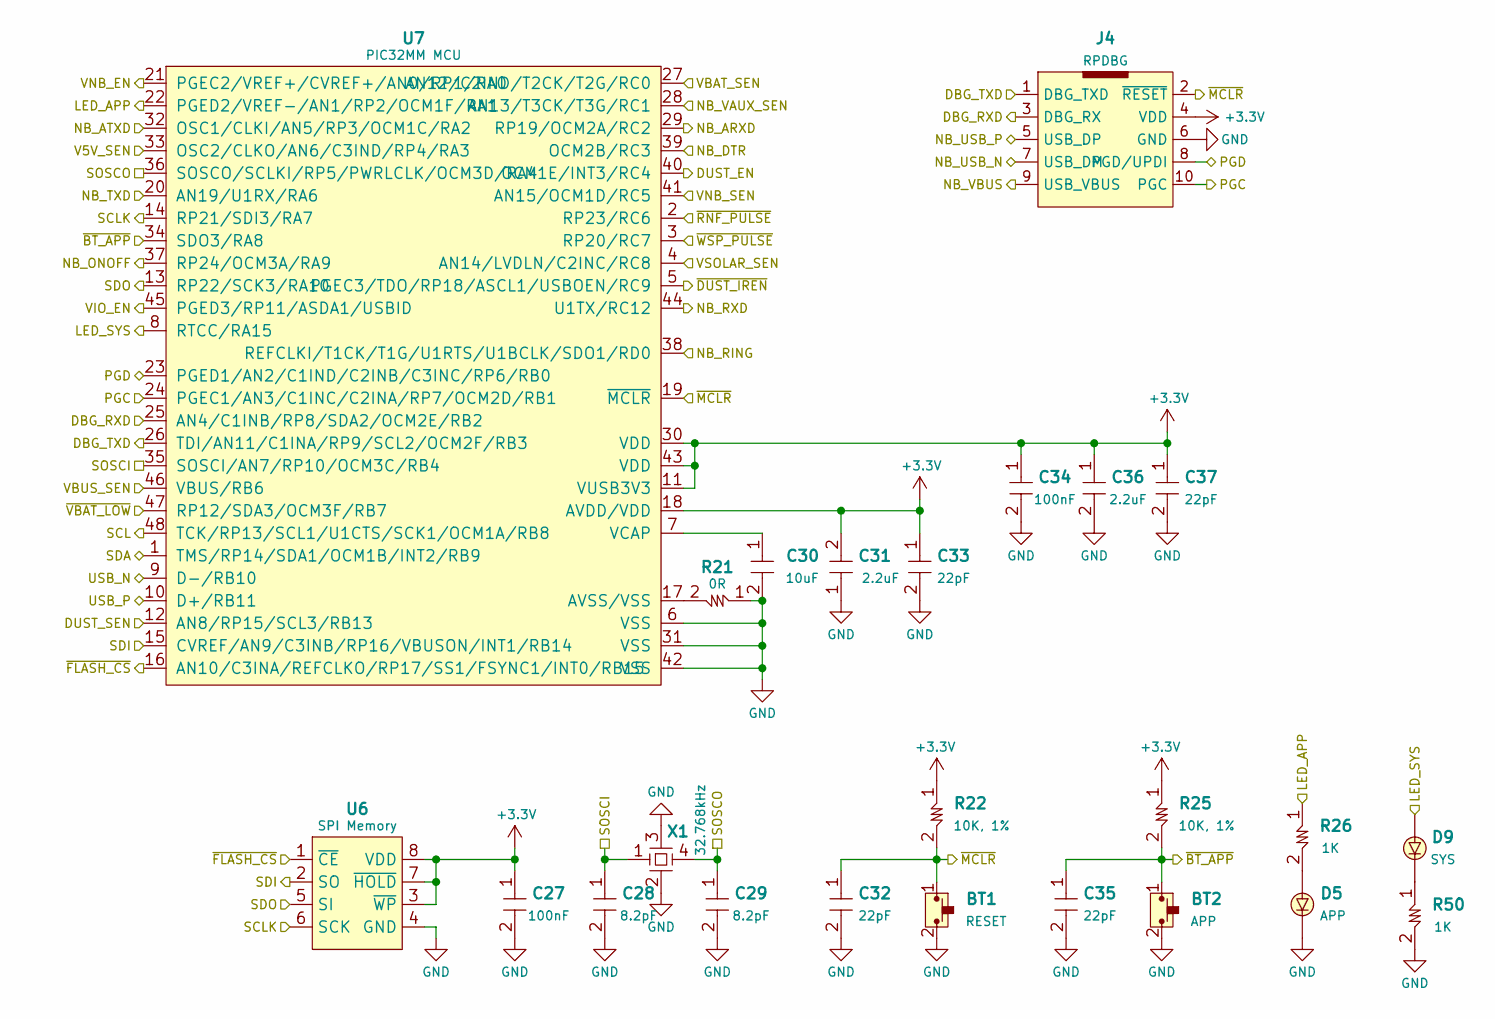
[picture p109: schematic MCU.kicad_sch]

Parts:
BT1: RESET; SW_SMD2_6.0x3.5
BT2: APP; SW_SMD2_6.0x3.5
C27, C34: 100nF; CAP0603
C28, C29: 8.2pF; CAP0603
C30: 10uF; CAP0805
C31, C36: 2.2uF; CAP0603
C32, C33, C35, C37: 22pF; CAP0603
D5: APP; LED0603
D9: SYS; LED0603
J4: RPDBG; DIL10_1.27_MTH
R21: 0R; RES0603
R22, R25: 10K, 1%; RES0603
R26, R50: 1K; RES0603
U6: SPI Memory; SOIC8_3.9_MCHP
U7: PIC32MM MCU; TQFP48-7x7_MCHP
X1: 32.768kHz; SMD4-7015

Connections:
+3.3V: C27.1, C31.2, C33.1, C34.1, C36.1, C37.1, J4.4 (VDD), R22.1, R25.1, U6.3 (~WP), U6.7 (~HOLD), U6.8 (VDD), U7.11 (VUSB3V3), U7.18 (AVDD/VDD), U7.30 (VDD), U7.43 (VDD)
DBG_RXD: J4.3 (DBG_RX), U7.25 (AN4/C1INB/RP8/SDA2/OCM2E/RB2)
DBG_TXD: J4.1 (DBG_TXD), U7.26 (TDI/AN11/C1INA/RP9/SCL2/OCM2F/RB3)
DUST_EN: U7.40 (OCM1E/INT3/RC4)
DUST_SEN: U7.12 (AN8/RP15/SCL3/RB13)
GND: BT1.2, BT2.2, C27.2, C28.2, C29.2, C30.2, C31.1, C32.2, C33.2, C34.2, C35.2, C36.2, C37.2, D5.K, J4.6 (GND), R21.1, R50.2, U6.4 (GND), U7.6 (VSS), U7.31 (VSS), U7.42 (VSS), X1.2 (GND1), X1.3 (GND2)
LED_APP: R26.1, U7.22 (PGED2/VREF-/AN1/RP2/OCM1F/RA1)
LED_SYS: D9.A, U7.8 (RTCC/RA15)
NB_ARXD: U7.29 (RP19/OCM2A/RC2)
NB_ATXD: U7.32 (OSC1/CLKI/AN5/RP3/OCM1C/RA2)
NB_DTR: U7.39 (OCM2B/RC3)
NB_ONOFF: U7.37 (RP24/OCM3A/RA9)
NB_RING: U7.38 (REFCLKI/T1CK/T1G/U1RTS/U1BCLK/SDO1/RD0)
NB_RXD: U7.44 (U1TX/RC12)
NB_TXD: U7.20 (AN19/U1RX/RA6)
NB_USB_N: J4.7 (USB_DM)
NB_USB_P: J4.5 (USB_DP)
NB_VAUX_SEN: U7.28 (AN13/T3CK/T3G/RC1)
NB_VBUS: J4.9 (USB_VBUS)
unnamed: C30.1, U7.7 (VCAP)
unnamed: D5.A, R26.2
unnamed: D9.K, R50.1
unnamed: R21.2, U7.17 (AVSS/VSS)
PGC: J4.10 (PGC), U7.24 (PGEC1/AN3/C1INC/C2INA/RP7/OCM2D/RB1)
PGD: J4.8 (PGD/UPDI), U7.23 (PGED1/AN2/C1IND/C2INB/C3INC/RP6/RB0)
SCL: U7.48 (TCK/RP13/SCL1/U1CTS/SCK1/OCM1A/RB8)
SCLK: U6.6 (SCK), U7.14 (RP21/SDI3/RA7)
SDA: U7.1 (TMS/RP14/SDA1/OCM1B/INT2/RB9)
SDI: U6.2 (SO), U7.15 (CVREF/AN9/C3INB/RP16/VBUSON/INT1/RB14)
SDO: U6.5 (SI), U7.13 (RP22/SCK3/RA10)
SOSCI: C28.1, U7.35 (SOSCI/AN7/RP10/OCM3C/RB4), X1.1 (X1)
SOSCO: C29.1, U7.36 (SOSCO/SCLKI/RP5/PWRLCLK/OCM3D/RA4), X1.4 (X2)
USB_N: U7.9 (D-/RB10)
USB_P: U7.10 (D+/RB11)
V5V_SEN: U7.33 (OSC2/CLKO/AN6/C3IND/RP4/RA3)
VBAT_SEN: U7.27 (AN12/C2IND/T2CK/T2G/RC0)
VBUS_SEN: U7.46 (VBUS/RB6)
VIO_EN: U7.45 (PGED3/RP11/ASDA1/USBID)
VNB_EN: U7.21 (PGEC2/VREF+/CVREF+/AN0/RP1/RA0)
VNB_SEN: U7.41 (AN15/OCM1D/RC5)
VSOLAR_SEN: U7.4 (AN14/LVDLN/C2INC/RC8)
~BT_APP: BT2.1, C35.1, R25.2, U7.34 (SDO3/RA8)
~DUST_IREN: U7.5 (PGEC3/TDO/RP18/ASCL1/USBOEN/RC9)
~FLASH_CS: U6.1 (~CE), U7.16 (AN10/C3INA/REFCLKO/RP17/SS1/FSYNC1/INT0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)
~MCLR: BT1.1, C32.1, J4.2 (~RESET), R22.2, U7.19 (~MCLR)
~RNF_PULSE: U7.2 (RP23/RC6)
~VBAT_LOW: U7.47 (RP12/SDA3/OCM3F/RB7)
~WSP_PULSE: U7.3 (RP20/RC7)
