hcmusthinhcode2k2/WeatherStation_Thesis/Hardware/NBMODULE.kicad_sch

## KiCad design Hardware/NBMODULE.kicad_sch (2024-08-14)

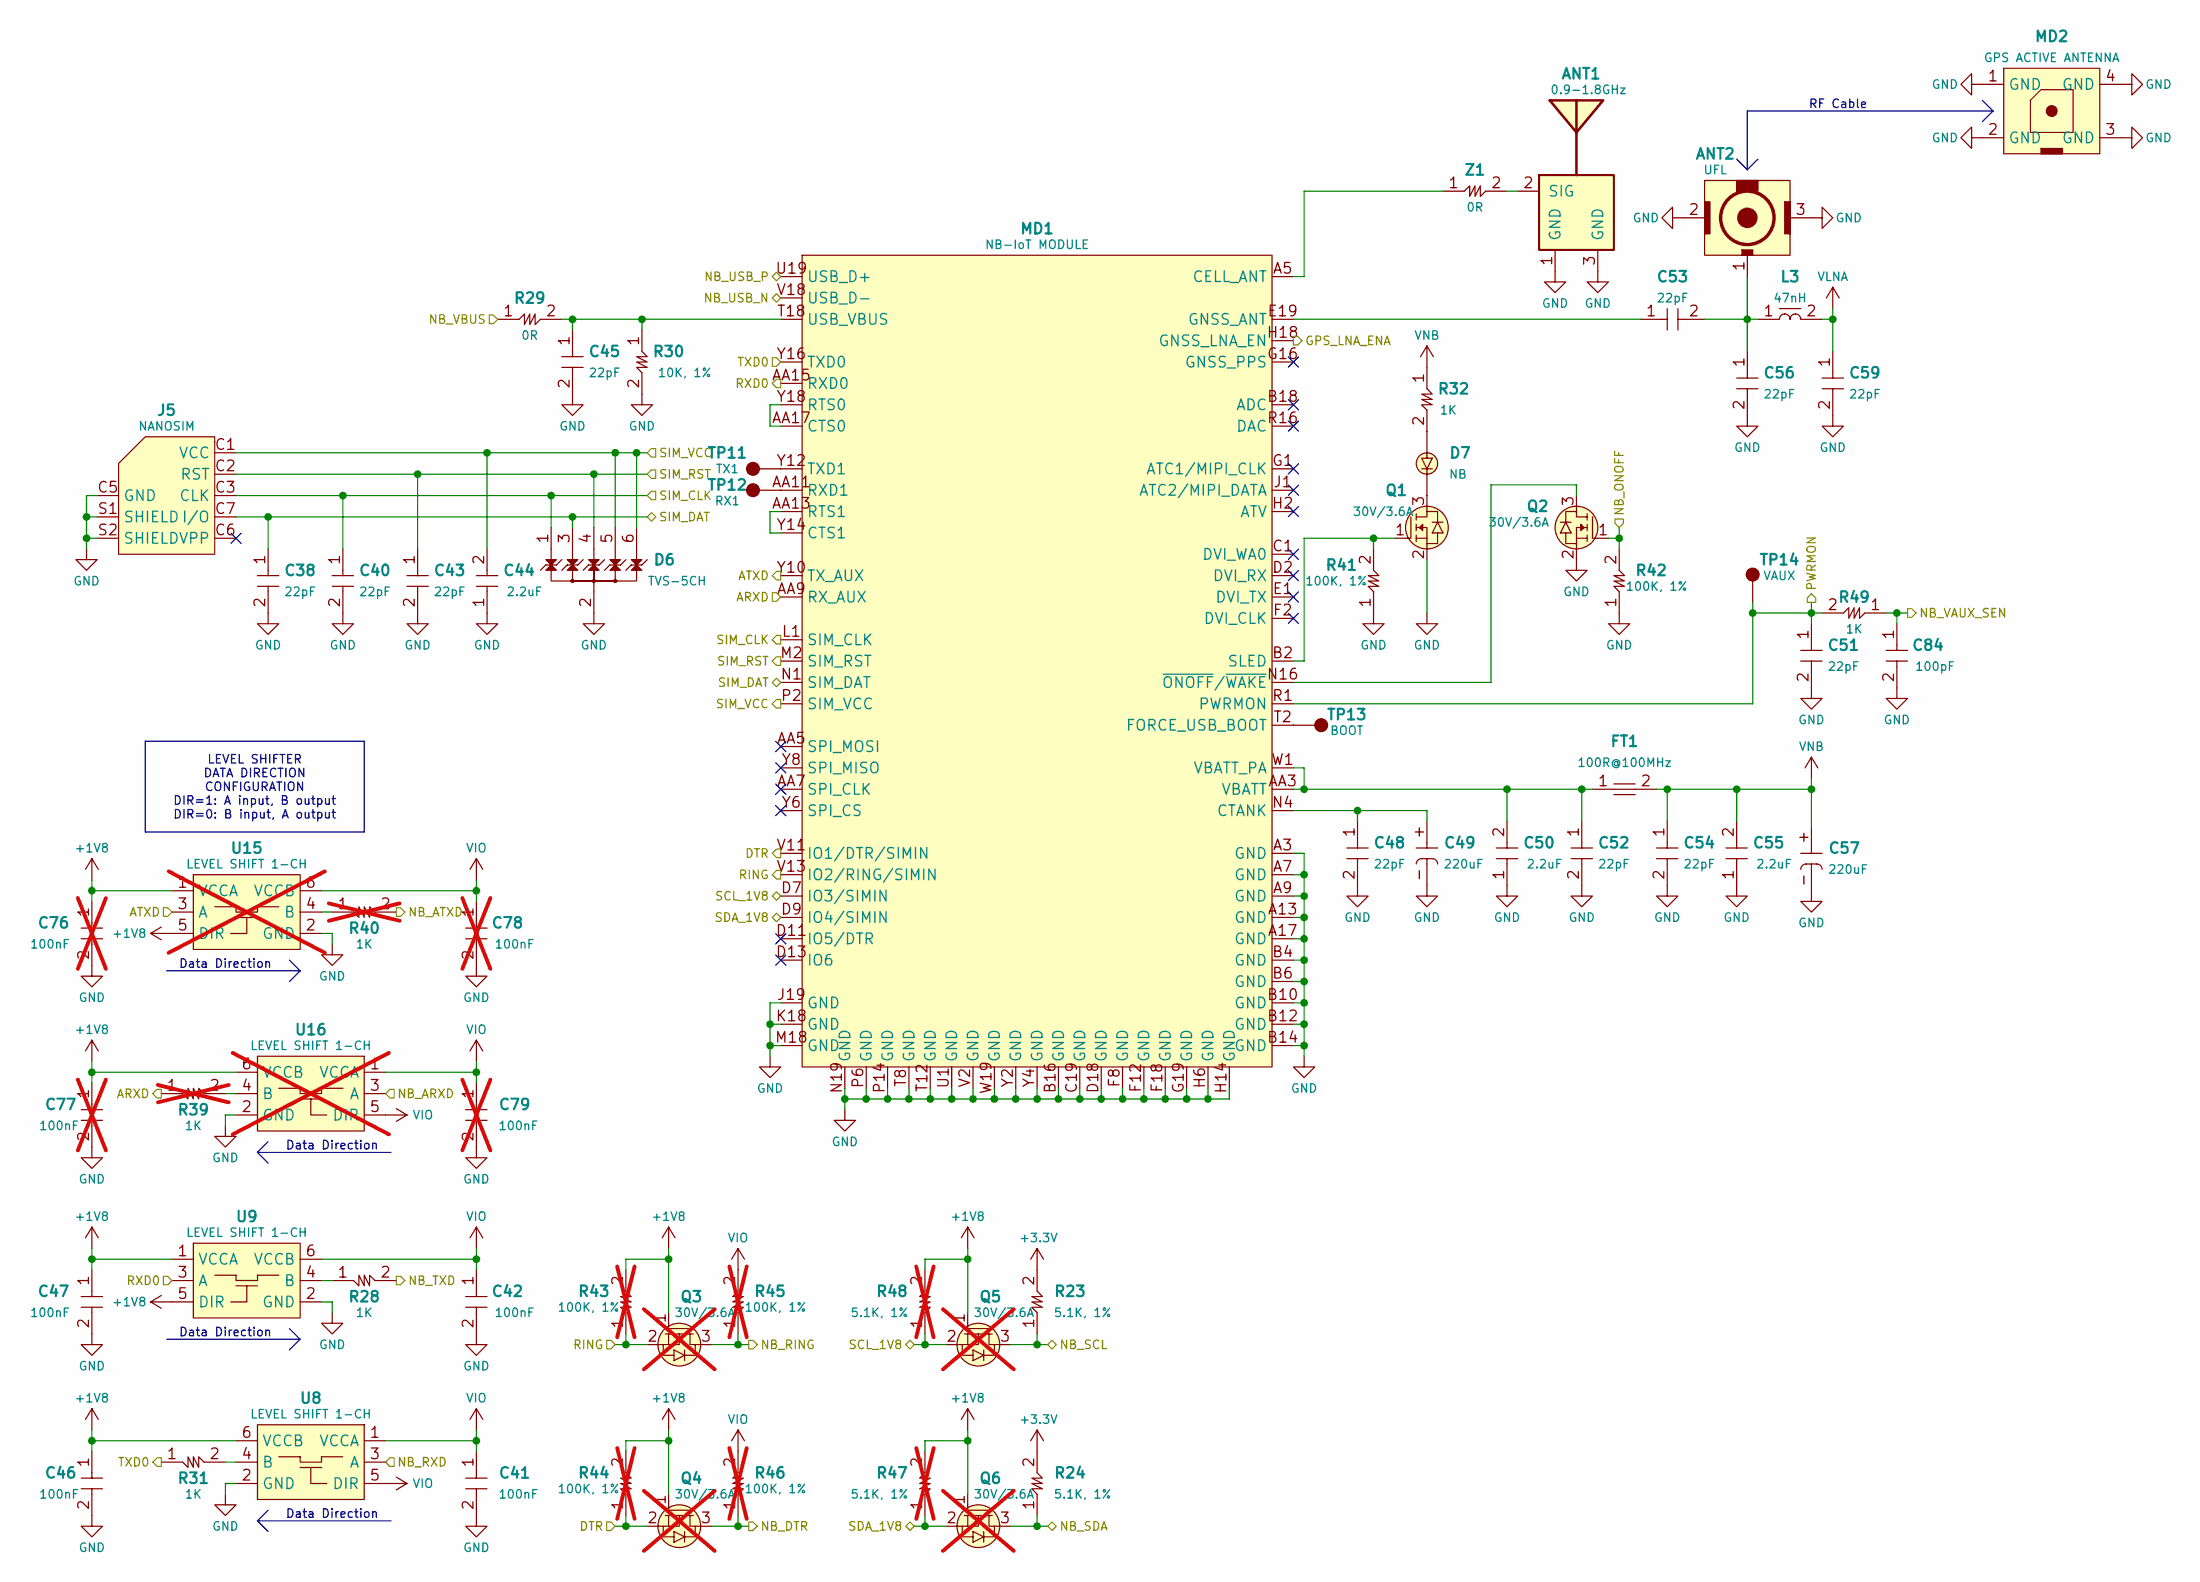
[picture p110: schematic NBMODULE.kicad_sch]

Parts:
ANT1: 0.9-1.8GHz; AH3G.303
ANT2: UFL; U.FL
C38, C40, C43, C45, C48, C51, C52, C53, C54, C56, C59: 22pF; CAP0603
C41, C42, C46, C47: 100nF; CAP0603
C44, C50, C55: 2.2uF; CAP0603
C49, C57: 220uF; CAP2312-6032
C76, C77, C78, C79: 100nF; CAP0603; not fitted
C84: 100pF; CAP0603
D6: TVS-5CH; SOT363
D7: NB; LED0603
FT1: 100R@100MHz; IND0805
J5: NANOSIM; SIM8051-6-0-14-01-A_GCT
L3: 47nH; IND0603
MD1: NB-IoT MODULE; xE310
MD2: GPS ACTIVE ANTENNA; 1575R-A
Q1, Q2: 30V/3.6A; SOT23
Q3, Q4, Q5, Q6: 30V/3.6A; SOT23; not fitted
R23, R24: 5.1K, 1%; RES0603
R28, R31, R32, R49: 1K; RES0603
R29: 0R; RES0603
R30: 10K, 1%; RES0603
R39, R40: 1K; RES0603; not fitted
R41, R42: 100K, 1%; RES0603
R43, R44, R45, R46: 100K, 1%; RES0603; not fitted
R47, R48: 5.1K, 1%; RES0603; not fitted
TP11: TX1; TP1MM
TP12: RX1; TP1MM
TP13: BOOT; TP1MM
TP14: VAUX; TP1MM
U8, U9: LEVEL SHIFT 1-CH; SOT-23-6_MCHP
U15, U16: LEVEL SHIFT 1-CH; SOT-23-6_MCHP; not fitted
Z1: 0R; RES0603

Connections:
+1V8: C46.1, C47.1, C76.1, C77.1, Q3.1 (G), Q4.1 (G), Q5.1 (G), Q6.1 (G), R43.2, R44.2, R47.2, R48.2, U8.6 (VCCB), U9.1 (VCCA), U9.5 (DIR), U15.1 (VCCA), U15.5 (DIR), U16.6 (VCCB)
+3.3V: R23.2, R24.2
ARXD: MD1.AA9 (RX_AUX), R39.1
ATXD: MD1.Y10 (TX_AUX), U15.3 (A)
DTR: MD1.V11 (IO1/DTR/SIMIN), Q4.2 (S), R44.1
GND: ANT1.1 (GND), ANT1.3 (GND), ANT2.2 (GND), ANT2.3 (GND), C38.2, C40.2, C41.2, C42.2, C43.2, C44.1, C45.2, C46.2, C47.2, C48.2, C49.-, C50.1, C51.2, C52.2, C54.2, C55.1, C56.2, C57.-, C59.2, C76.2, C77.2, C78.2, C79.2, C84.2, D6.2 (GND), J5.C5 (GND), J5.S1 (SHIELD), J5.S2 (SHIELD), MD1.A3 (GND), MD1.A7 (GND), MD1.A9 (GND), MD1.A13 (GND), MD1.A17 (GND), MD1.B4 (GND), MD1.B6 (GND), MD1.B10 (GND), MD1.B12 (GND), MD1.B14 (GND), MD1.B16 (GND), MD1.C19 (GND), MD1.D18 (GND), MD1.F8 (GND), MD1.F12 (GND), MD1.F18 (GND), MD1.G19 (GND), MD1.H6 (GND), MD1.H14 (GND), MD1.J19 (GND), MD1.K18 (GND), MD1.M18 (GND), MD1.N19 (GND), MD1.P6 (GND), MD1.P14 (GND), MD1.T8 (GND), MD1.T12 (GND), MD1.U1 (GND), MD1.V2 (GND), MD1.W19 (GND), MD1.Y2 (GND), MD1.Y4 (GND), MD2.1, MD2.2, MD2.3, MD2.4, Q1.2 (S), Q2.2 (S), R30.2, R41.1, R42.1, U8.2 (GND), U9.2 (GND), U15.2 (GND), U16.2 (GND)
GPS_LNA_ENA: MD1.H18 (GNSS_LNA_EN)
NB_ARXD: U16.3 (A)
NB_ATXD: R40.2
NB_DTR: Q4.3 (D), R46.1
NB_ONOFF: Q2.1 (G), R42.2
NB_RING: Q3.3 (D), R45.1
NB_RXD: U8.3 (A)
NB_SCL: Q5.3 (D), R23.1
NB_SDA: Q6.3 (D), R24.1
NB_TXD: R28.2
NB_USB_N: MD1.V18 (USB_D-)
NB_USB_P: MD1.U19 (USB_D+)
NB_VAUX_SEN: C84.1, R49.1
NB_VBUS: R29.1
unnamed: ANT1.2 (SIG), Z1.2
unnamed: ANT2.1 (SIG), C53.2, C56.1, L3.1
unnamed: C45.1, MD1.T18 (USB_VBUS), R29.2, R30.1
unnamed: C48.1, C49.+, MD1.N4 (CTANK)
unnamed: C50.2, C52.1, FT1.1, MD1.AA3 (VBATT), MD1.W1 (VBATT_PA)
unnamed: C53.1, MD1.E19 (GNSS_ANT)
unnamed: D7.A, R32.2
unnamed: D7.K, Q1.3 (D)
unnamed: MD1.A5 (CELL_ANT), Z1.1
unnamed: MD1.AA11 (RXD1), TP12.1
unnamed: MD1.AA13 (RTS1), MD1.Y14 (CTS1)
unnamed: MD1.AA17 (CTS0), MD1.Y18 (RTS0)
unnamed: MD1.B2 (SLED), Q1.1 (G), R41.2
unnamed: MD1.N16 (~ONOFF/~WAKE), Q2.3 (D)
unnamed: MD1.T2 (FORCE_USB_BOOT), TP13.1
unnamed: MD1.Y12 (TXD1), TP11.1
unnamed: R28.1, U9.4 (B)
unnamed: R31.2, U8.4 (B)
unnamed: R39.2, U16.4 (B)
unnamed: R40.1, U15.4 (B)
PWRMON: C51.1, MD1.R1 (PWRMON), R49.2, TP14.1
RING: MD1.V13 (IO2/RING/SIMIN), Q3.2 (S), R43.1
RXD0: MD1.AA15 (RXD0), U9.3 (A)
SCL_1V8: MD1.D7 (IO3/SIMIN), Q5.2 (S), R48.1
SDA_1V8: MD1.D9 (IO4/SIMIN), Q6.2 (S), R47.1
SIM_CLK: C40.1, D6.1 (CH1), J5.C3 (CLK), MD1.L1 (SIM_CLK)
SIM_DAT: C38.1, D6.3 (CH2), J5.C7 (I/O), MD1.N1 (SIM_DAT)
SIM_RST: C43.1, D6.4 (CH3), J5.C2 (RST), MD1.M2 (SIM_RST)
SIM_VCC: C44.2, D6.5 (CH4), D6.6 (CH5), J5.C1 (VCC), MD1.P2 (SIM_VCC)
TXD0: MD1.Y16 (TXD0), R31.1
VIO: C41.1, C42.1, C78.1, C79.1, R45.2, R46.2, U8.1 (VCCA), U8.5 (DIR), U9.6 (VCCB), U15.6 (VCCB), U16.1 (VCCA), U16.5 (DIR)
VLNA: C59.1, L3.2
VNB: C54.1, C55.2, C57.+, FT1.2, R32.1

Notes on the sheet:
LEVEL SHIFTER DATA DIRECTION CONFIGURATION DIR=1: A input, B output DIR=0: B input, A output
Data Direction
RF Cable
