hcmusthinhcode2k2/WeatherStation_Thesis/Hardware/POWER.kicad_sch

## KiCad design Hardware/POWER.kicad_sch (2024-08-14)

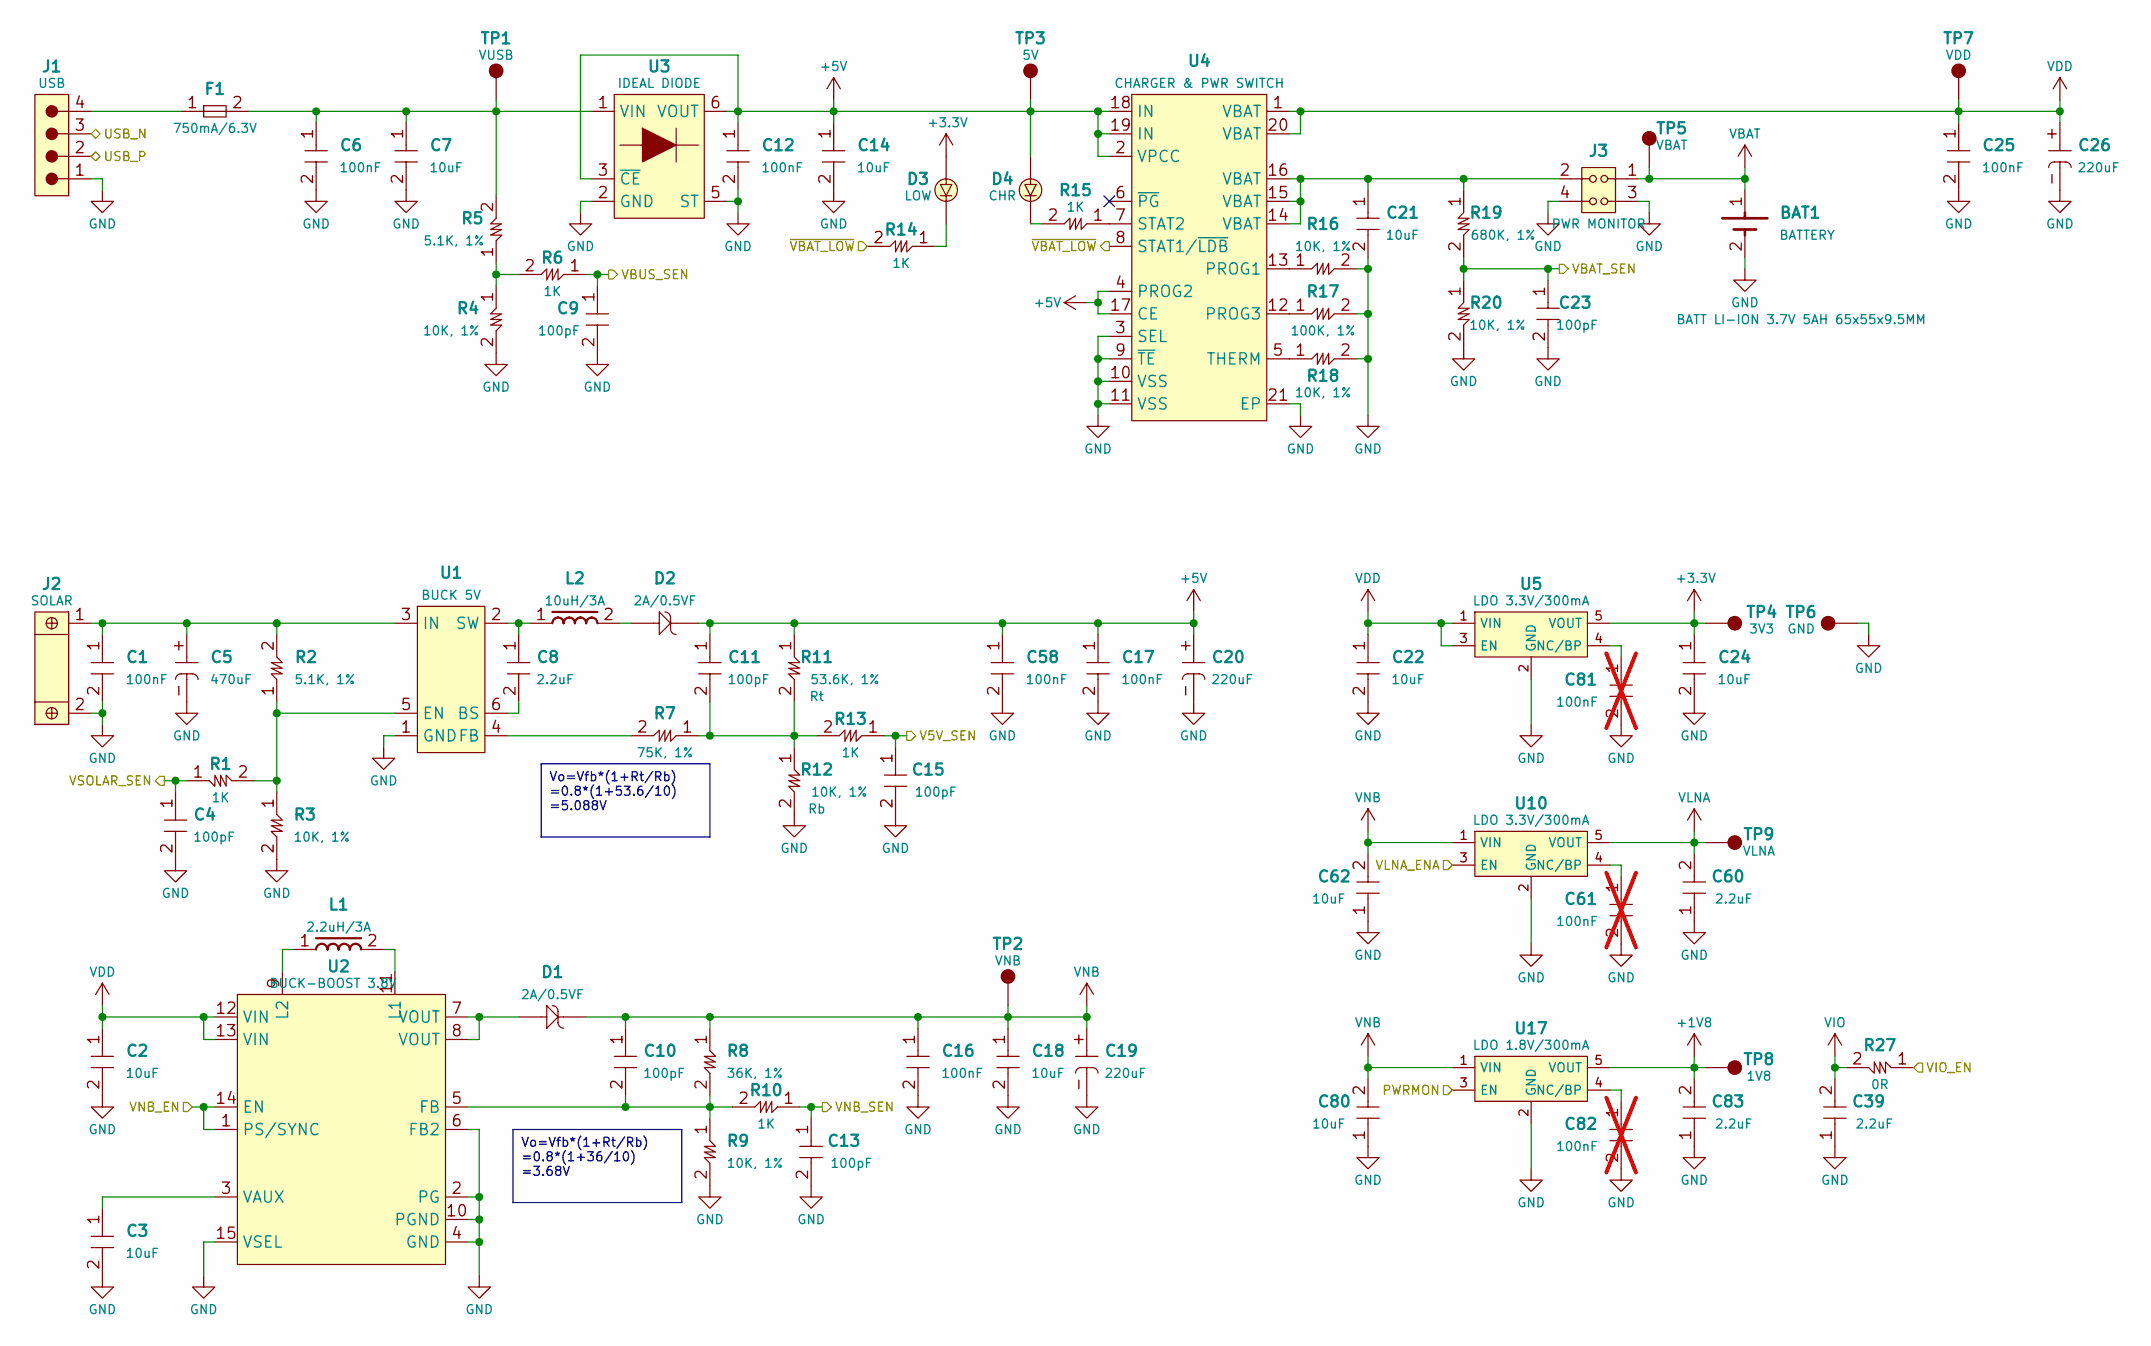
[picture p111: schematic POWER.kicad_sch]

Parts:
BAT1: BATTERY; PAD02_2.54TH
C1, C6, C12, C16, C17, C25, C58: 100nF; CAP0603
C2, C3, C7, C14, C18, C21, C22, C24, C62, C80: 10uF; CAP0805
C4, C9, C10, C11, C13, C15, C23: 100pF; CAP0603
C5: 470uF; CAP_ELEC-10.3x10.3-DIA10
C8, C39, C60, C83: 2.2uF; CAP0603
C19, C20, C26: 220uF; CAP2312-6032
C61, C81, C82: 100nF; CAP0603; not fitted
D1, D2: 2A/0.5VF; DO-214AC
D3: LOW; LED0603
D4: CHR; LED0603
F1: 750mA/6.3V; FUSE1812
J1: USB; HDM-4x2.54-TH
J2: SOLAR; PAD02_2.54TH
J3: PWR MONITOR; DIL04_2.54_MTH
L1: 2.2uH/3A; IND5852
L2: 10uH/3A; IND7870
R1, R6, R10, R13, R14, R15: 1K; RES0603
R2, R5: 5.1K, 1%; RES0603
R3, R4, R9, R12, R16, R18, R20: 10K, 1%; RES0603
R7: 75K, 1%; RES0603
R8: 36K, 1%; RES0603
R11: 53.6K, 1%; RES0603
R17: 100K, 1%; RES0603
R19: 680K, 1%; RES0603
R27: 0R; RES0603
TP1: VUSB; TP1MM
TP2: VNB; TP1MM
TP3: 5V; TP1MM
TP4: 3V3; TP1MM
TP5: VBAT; TP1MM
TP6: GND; TP1MM
TP7: VDD; TP1MM
TP8: 1V8; TP1MM
TP9: VLNA; TP1MM
U1: BUCK 5V; SOT-23-6_MCHP
U2: BUCK-BOOST 3.8V; PowerVQFN15_TI
U3: IDEAL DIODE; SOT363
U4: CHARGER & PWR SWITCH; VQFN20-4x4_MCHP
U5, U10: LDO 3.3V/300mA; SOT25_DIODES
U17: LDO 1.8V/300mA; SOT25_DIODES

Connections:
+1V8: C83.2, TP8.1, U17.5 (VOUT)
+3.3V: C24.1, D3.A, TP4.1, U5.5 (VOUT)
+5V: C11.1, C12.1, C14.1, C17.1, C20.+, C58.1, D2.K, D4.A, R11.1, TP3.1, U3.3 (~CE), U3.6 (VOUT), U4.2 (VPCC), U4.4 (PROG2), U4.17 (CE), U4.18 (IN), U4.19 (IN)
GND: BAT1.2 (-), C1.2, C2.2, C3.2, C4.2, C5.-, C6.2, C7.2, C9.2, C12.2, C13.2, C14.2, C15.2, C16.2, C17.2, C18.2, C19.-, C20.-, C21.2, C22.2, C23.2, C24.2, C25.2, C26.-, C39.1, C58.2, C60.1, C61.2, C62.1, C80.1, C81.2, C82.2, C83.1, J1.1, J2.2, J3.3, J3.4, R3.2, R4.2, R9.2, R12.2, R16.2, R17.2, R18.2, R20.2, TP6.1, U1.1 (GND), U2.2 (PG), U2.4 (GND), U2.6 (FB2), U2.10 (PGND), U2.15 (VSEL), U3.2 (GND), U3.5 (ST), U4.3 (SEL), U4.9 (~TE), U4.10 (VSS), U4.11 (VSS), U4.21 (EP), U5.2 (GND), U10.2 (GND), U17.2 (GND)
unnamed: C1.1, C5.+, J2.1, R2.2, U1.3 (IN)
unnamed: C3.1, U2.3 (VAUX)
unnamed: C6.1, C7.1, F1.2, R5.2, TP1.1, U3.1 (VIN)
unnamed: C8.1, L2.1, U1.2 (SW)
unnamed: C8.2, U1.6 (BS)
unnamed: C10.2, R8.2, R9.1, R10.2, U2.5 (FB)
unnamed: C11.2, R7.1, R11.2, R12.1, R13.2
unnamed: C21.1, J3.2, R19.1, U4.14 (VBAT), U4.15 (VBAT), U4.16 (VBAT)
unnamed: C61.1, U10.4 (NC/BP)
unnamed: C81.1, U5.4 (NC/BP)
unnamed: C82.1, U17.4 (NC/BP)
unnamed: D1.A, U2.7 (VOUT), U2.8 (VOUT)
unnamed: D2.A, L2.2
unnamed: D3.K, R14.1
unnamed: D4.K, R15.2
unnamed: F1.1, J1.4
unnamed: L1.1, U2.9 (L2)
unnamed: L1.2, U2.11 (L1)
unnamed: R1.2, R2.1, R3.1, U1.5 (EN)
unnamed: R4.1, R5.1, R6.2
unnamed: R7.2, U1.4 (FB)
unnamed: R15.1, U4.7 (STAT2)
unnamed: R16.1, U4.13 (PROG1)
unnamed: R17.1, U4.12 (PROG3)
unnamed: R18.1, U4.5 (THERM)
PWRMON: U17.3 (EN)
USB_N: J1.3
USB_P: J1.2
V5V_SEN: C15.1, R13.1
VBAT: BAT1.1 (+), J3.1, TP5.1
VBAT_SEN: C23.1, R19.2, R20.1
VBUS_SEN: C9.1, R6.1
VDD: C2.1, C22.1, C25.1, C26.+, TP7.1, U2.12 (VIN), U2.13 (VIN), U4.1 (VBAT), U4.20 (VBAT), U5.1 (VIN), U5.3 (EN)
VIO: C39.2, R27.2
VIO_EN: R27.1
VLNA: C60.2, TP9.1, U10.5 (VOUT)
VLNA_ENA: U10.3 (EN)
VNB: C10.1, C16.1, C18.1, C19.+, C62.2, C80.2, D1.K, R8.1, TP2.1, U10.1 (VIN), U17.1 (VIN)
VNB_EN: U2.1 (PS/SYNC), U2.14 (EN)
VNB_SEN: C13.1, R10.1
VSOLAR_SEN: C4.1, R1.1
~VBAT_LOW: R14.2, U4.8 (STAT1/~LDB)

Notes on the sheet:
Vo=Vfb*(1+Rt/Rb) =0.8*(1+53.6/10) =5.088V
Vo=Vfb*(1+Rt/Rb) =0.8*(1+36/10) =3.68V
