hcmusthinhcode2k2/WeatherStation_Thesis/Hardware/SENSORS.kicad_sch

## KiCad design Hardware/SENSORS.kicad_sch (2024-08-14)

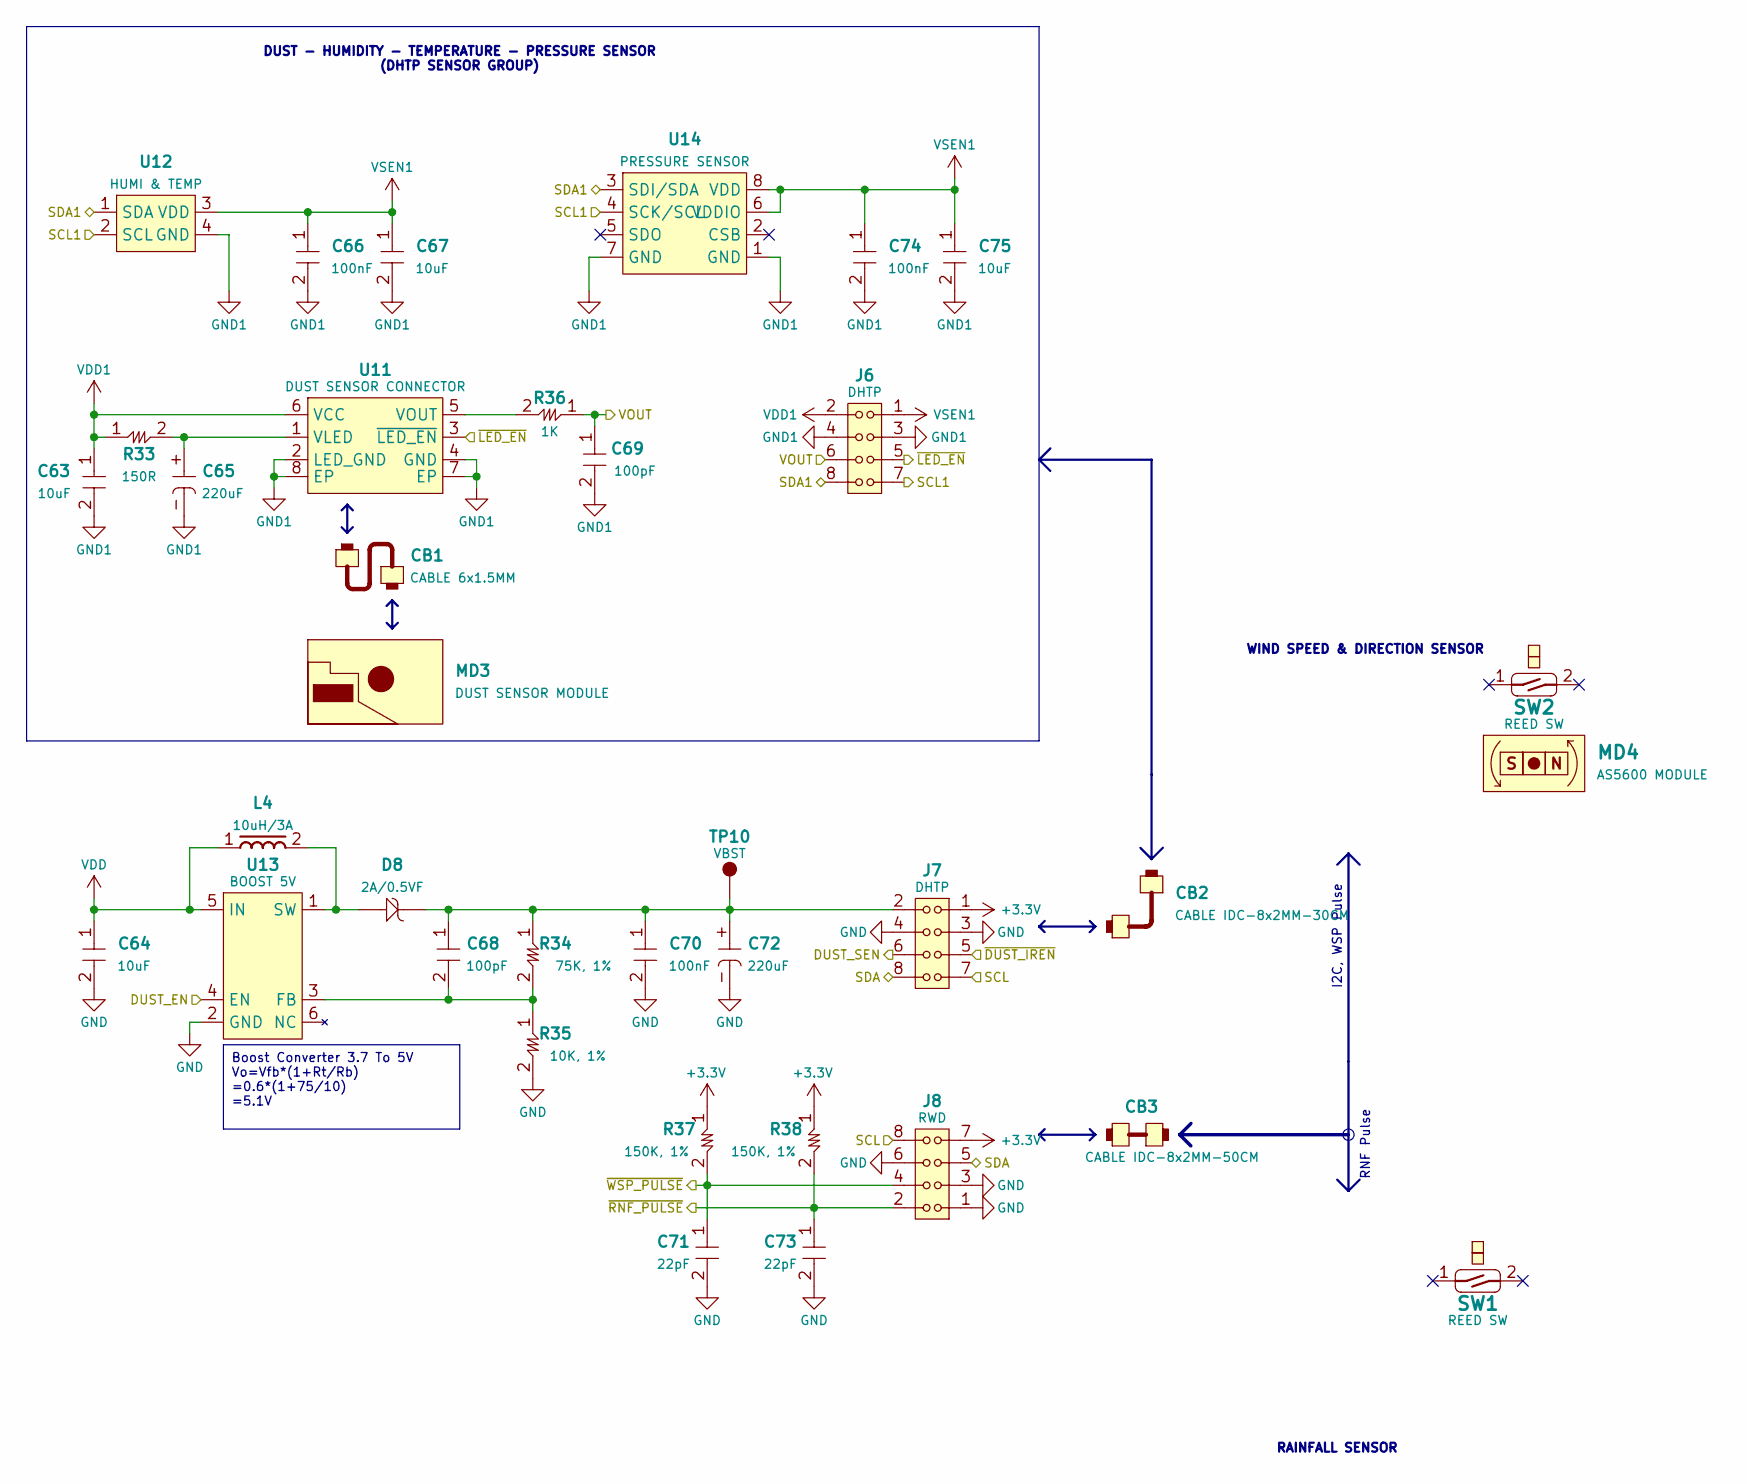
[picture p112: schematic SENSORS.kicad_sch]

Parts:
C63, C64, C67, C75: 10uF; CAP0805
C65, C72: 220uF; CAP2312-6032
C66, C70, C74: 100nF; CAP0603
C68, C69: 100pF; CAP0603
C71, C73: 22pF; CAP0603
CB1: CABLE 6x1.5MM
CB2: CABLE IDC-8x2MM-30CM
CB3: CABLE IDC-8x2MM-50CM
D8: 2A/0.5VF; DO-214AC
J6, J7: DHTP; HDM-2x4x2.0-TH-RA
J8: RWD; HDM-2x4x2.0-TH-RA
L4: 10uH/3A; IND7870
MD3: DUST SENSOR MODULE
MD4: AS5600 MODULE
R33: 150R; RES0603
R34: 75K, 1%; RES0603
R35: 10K, 1%; RES0603
R36: 1K; RES0603
R37, R38: 150K, 1%; RES0603
SW1, SW2: REED SW
TP10: VBST; TP1MM
U11: DUST SENSOR CONNECTOR; HDM-6x1.5-SMD-RA
U12: HUMI & TEMP; SHT4x
U13: BOOST 5V; SOT-23-6_MCHP
U14: PRESSURE SENSOR; DPS368

Connections:
+3.3V: J7.1, J8.7, R37.1, R38.1
DUST_EN: U13.4 (EN)
DUST_SEN: J7.6
GND: C64.2, C70.2, C71.2, C72.-, C73.2, J7.3, J7.4, J8.1, J8.3, J8.6, R35.2, U13.2 (GND)
GND1: C63.2, C65.-, C66.2, C67.2, C69.2, C74.2, C75.2, J6.3, J6.4, U11.2 (LED_GND), U11.4 (GND), U11.7 (EP), U11.8 (EP), U12.4 (GND), U14.1 (GND), U14.7 (GND)
unnamed: C65.+, R33.2, U11.1 (VLED)
unnamed: C68.1, C70.1, C72.+, D8.K, J7.2, R34.1, TP10.1
unnamed: C68.2, R34.2, R35.1, U13.3 (FB)
unnamed: D8.A, L4.2, U13.1 (SW)
unnamed: R36.2, U11.5 (VOUT)
SCL: J7.7, J8.8
SCL1: J6.7, U12.2 (SCL), U14.4 (SCK/SCL)
SDA: J7.8, J8.5
SDA1: J6.8, U12.1 (SDA), U14.3 (SDI/SDA)
VDD: C64.1, L4.1, U13.5 (IN)
VDD1: C63.1, J6.2, R33.1, U11.6 (VCC)
VOUT: C69.1, J6.6, R36.1
VSEN1: C66.1, C67.1, C74.1, C75.1, J6.1, U12.3 (VDD), U14.6 (VDDIO), U14.8 (VDD)
~DUST_IREN: J7.5
~LED_EN: J6.5, U11.3 (~LED_EN)
~RNF_PULSE: C73.1, J8.2, R38.2
~WSP_PULSE: C71.1, J8.4, R37.2

Notes on the sheet:
Boost Converter 3.7 To 5V Vo=Vfb*(1+Rt/Rb) =0.6*(1+75/10) =5.1V
I2C, WSP Pulse
RAINFALL SENSOR
RNF Pulse
DUST - HUMIDITY - TEMPERATURE - PRESSURE SENSOR (DHTP SENSOR GROUP)
WIND SPEED & DIRECTION SENSOR
