hcmusthinhcode2k2/WeatherStation_Thesis/Firmware/RPCLib/MIPS/Core/uart/uart1.h

/**
  UART1 Generated Driver API Header File 

  @Company
    Microchip Technology Inc.

  @File Name
    uart1.h

  @Summary
    This is the generated header file for the UART1 driver using PIC24 / dsPIC33 / PIC32MM MCUs

  @Description
    This header file provides APIs for driver for UART1. 
    Generation Information : 
        Product Revision  :  PIC24 / dsPIC33 / PIC32MM MCUs - 1.170.0
        Device            :  PIC32MM0256GPM048
    The generated drivers are tested against the following:
        Compiler          :  XC32 v2.50
        MPLAB             :  MPLAB X v5.45
 */

/*
    (c) 2020 Microchip Technology Inc. and its subsidiaries. You may use this
    software and any derivatives exclusively with Microchip products.

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
    IN NO EVENT WILL MICROCHIP BE LIABLE FOR ANY INDIRECT, SPECIAL, PUNITIVE,
    INCIDENTAL OR CONSEQUENTIAL LOSS, DAMAGE, COST OR EXPENSE OF ANY KIND
    WHATSOEVER RELATED TO THE SOFTWARE, HOWEVER CAUSED, EVEN IF MICROCHIP HAS
    BEEN ADVISED OF THE POSSIBILITY OR THE DAMAGES ARE FORESEEABLE. TO THE
    FULLEST EXTENT ALLOWED BY LAW, MICROCHIP'S TOTAL LIABILITY ON ALL CLAIMS IN
    ANY WAY RELATED TO THIS SOFTWARE WILL NOT EXCEED THE AMOUNT OF FEES, IF ANY,
    THAT YOU HAVE PAID DIRECTLY TO MICROCHIP FOR THIS SOFTWARE.

    MICROCHIP PROVIDES THIS SOFTWARE CONDITIONALLY UPON YOUR ACCEPTANCE OF THESE
    TERMS.
 */

#ifndef _UART1_H
#define _UART1_H

/**
 Section: Included Files
 */

#include <stdbool.h>
#include <stdint.h>

#ifdef __cplusplus  // Provide C++ Compatibility

extern "C" {

#endif
    /**
      Section: UART1 Driver Routines
     */

    /**
      @Summary
        Initializes the UART instance : 1

      @Description
        This routine initializes the UART driver instance for : 1
        index.
        This routine must be called before any other UART routine is called.
    
      @Preconditions
        None.

      @Returns
        None.

      @Param
        None.

      @Comment
        None.    
 
      @Example
        None.

     */

    void UART1_Initialize(void);
    void UART1_Deinitialize(void);
    /**
      @Summary
        Read a byte of data from the UART1

      @Description
        This routine reads a byte of data from the UART1.

      @Preconditions
        UART1_Initialize function should have been called 
        before calling this function. The transfer status should be checked to see 
        if the receiver is not empty before calling this function.

      @Param
        None.

      @Returns
        A data byte received by the driver.

      @Example
        None.
     */

    uint8_t UART1_Read(void);

    /**
      @Summary
        Writes a byte of data to the UART1

      @Description
        This routine writes a byte of data to the UART1.

      @Preconditions
        UART1_Initialize function should have been called 
        before calling this function. The transfer status should be checked to see if
        transmitter is not full before calling this function.

      @Param
        byte         - Data byte to write to the UART1

      @Returns
        None.

      @Example
        None.
     */

    void UART1_Write(uint8_t byte);


    /**
      @Description
        Indicates of there is data available to read.

      @Returns
        true if byte can be read.
        false if byte can't be read right now.
     */
    bool UART1_IsRxReady(void);

    /**
      @Description
        Indicates if a byte can be written.
 
     @Returns
        true if byte can be written.
        false if byte can't be written right now.
     */
    bool UART1_IsTxReady(void);

    /**
      @Description
        Indicates if all bytes have been transferred.
 
     @Returns
        true if all bytes transfered.
        false if there is still data pending to transfer.
     */
    bool UART1_IsTxDone(void);

    /**
      @Summary
        Assigns a function pointer with a transmit callback address.

      @Description
        This routine assigns a function pointer with a transmit callback address.

      @Param
        Address of the callback routine.

      @Returns
        None
 
      @Example 
        <code>
            UART1_SetTxInterruptHandler(&UART1_Transmit_CallBack);
        </code>
     */
    void UART1_SetTxInterruptHandler(void (* interruptHandler)(void));

    /**
      @Summary
        Transmit callback routine.

      @Description
        This routine is a transmit callback function.

      @Param
        None.

      @Returns
        None
 
      @Example 
        <code>
            UART1_SetTxInterruptHandler(&UART1_Transmit_CallBack);
        </code>
     */
    void UART1_Transmit_CallBack(void);

    /**
      @Summary
        Assigns a function pointer with a receive callback address.

      @Description
        This routine assigns a function pointer with a receive callback address.

      @Param
        Address of the callback routine.

      @Returns
        None
 
      @Example 
        <code>
            UART1_SetRxInterruptHandler(&UART1_Receive_CallBack);
        </code>
     */
    void UART1_SetRxInterruptHandler(void (* interruptHandler)(void));

    /**
      @Summary
        Receive callback routine.

      @Description
        This routine is a receive callback function.

      @Param
        None.

      @Returns
        None
 
      @Example 
        <code>
            UART1_SetTxInterruptHandler(&UART1_Receive_CallBack);
        </code>
     */
    void UART1_Receive_CallBack(void);


    /*******************************************************************************

      !!! Deprecated API and types !!!
      !!! These functions will not be supported in future releases !!!

     *******************************************************************************/

    /** UART1 Driver Hardware Flags

      @Summary
        Specifies the status of the hardware receive or transmit

      @Description
        This type specifies the status of the hardware receive or transmit.
        More than one of these values may be OR'd together to create a complete
        status value.  To test a value of this type, the bit of interest must be
        AND'ed with value and checked to see if the result is non-zero.
     */
    typedef enum {
        /* Indicates that Receive buffer has data, at least one more character can be read */
        UART1_RX_DATA_AVAILABLE = (1 << 0),
        /* Indicates that Receive buffer has overflowed */
        UART1_RX_OVERRUN_ERROR = (1 << 1),
        /* Indicates that Framing error has been detected for the current character */
        UART1_FRAMING_ERROR = (1 << 2),
        /* Indicates that Parity error has been detected for the current character */
        UART1_PARITY_ERROR = (1 << 3),
        /* Indicates that Receiver is Idle */
        UART1_RECEIVER_IDLE = (1 << 4),
        /* Indicates that the last transmission has completed */
        UART1_TX_COMPLETE = (1 << 8),
        /* Indicates that Transmit buffer is full */
        UART1_TX_FULL = (1 << 9)
    } UART1_STATUS;

    /** UART1 Driver Transfer Flags

      @Summary
        Specifies the status of the receive or transmit

      @Description
        This type specifies the status of the receive or transmit operation.
        More than one of these values may be OR'd together to create a complete
        status value.  To test a value of this type, the bit of interest must be
        AND'ed with value and checked to see if the result is non-zero.
     */

    typedef enum {
        /* Indicates that the core driver buffer is full */
        UART1_TRANSFER_STATUS_RX_FULL = (1 << 0),
        /* Indicates that at least one byte of Data has been received */
        UART1_TRANSFER_STATUS_RX_DATA_PRESENT = (1 << 1),
        /* Indicates that the core driver receiver buffer is empty */
        UART1_TRANSFER_STATUS_RX_EMPTY = (1 << 2),
        /* Indicates that the core driver transmitter buffer is full */
        UART1_TRANSFER_STATUS_TX_FULL = (1 << 3),
        /* Indicates that the core driver transmitter buffer is empty */
        UART1_TRANSFER_STATUS_TX_EMPTY = (1 << 4)
    } UART1_TRANSFER_STATUS;

    /**
      @Summary
        Returns the number of bytes read by the UART1 peripheral

      @Description
        This routine returns the number of bytes read by the Peripheral and fills the
        application read buffer with the read data.

      @Preconditions
        UART1_Initialize function should have been called 
        before calling this function

      @Param
        buffer       - Buffer into which the data read from the UART1

      @Param
        numbytes     - Total number of bytes that need to be read from the UART1
                       (must be equal to or less than the size of the buffer)

      @Returns
        Number of bytes actually copied into the caller's buffer or -1 if there
        is an error.

      @Example
        <code>
        char                     myBuffer[MY_BUFFER_SIZE];
        unsigned int             numBytes;
        UART1_TRANSFER_STATUS status ;

        // Pre-initialize myBuffer with MY_BUFFER_SIZE bytes of valid data.

        numBytes = 0;
        while( numBytes < MY_BUFFER_SIZE);
        {
            status = UART1_TransferStatusGet ( ) ;
            if (status & UART1_TRANSFER_STATUS_RX_FULL)
            {
                numBytes += UART1_ReadBuffer( myBuffer + numBytes, MY_BUFFER_SIZE - numBytes )  ;
                if(numBytes < readbufferLen)
                {
                    continue;
                }
                else
                {
                    break;
                }
            }
            else
            {
                continue;
            }

            // Do something else...
        }
        </code>
     */
    unsigned int __attribute__((deprecated)) UART1_ReadBuffer(uint8_t *buffer, unsigned int numbytes);

    /**
      @Summary
        Returns the number of bytes written into the internal buffer

      @Description
        This API transfers the data from application buffer to internal buffer and 
        returns the number of bytes added in that queue

      @Preconditions
        UART1_Initialize function should have been called 
        before calling this function

      @Example
        <code>
        char                     myBuffer[MY_BUFFER_SIZE];
        unsigned int             numBytes;
        UART1_TRANSFER_STATUS status ;

        // Pre-initialize myBuffer with MY_BUFFER_SIZE bytes of valid data.

        numBytes = 0;
        while( numBytes < MY_BUFFER_SIZE);
        {
            status = UART1_TransferStatusGet ( ) ;
            if (status & UART1_TRANSFER_STATUS_TX_EMPTY)
            {
                numBytes += UART1_WriteBuffer ( myBuffer + numBytes, MY_BUFFER_SIZE - numBytes )  ;
                if(numBytes < writebufferLen)
                {
                    continue;
                }
                else
                {
                    break;
                }
            }
            else
            {
                continue;
            }

            // Do something else...
        }
        </code>
     */
    unsigned int __attribute__((deprecated)) UART1_WriteBuffer(uint8_t *buffer, unsigned int numbytes);

    /**
      @Summary
        Returns the transmitter and receiver transfer status

      @Description
        This returns the transmitter and receiver transfer status.The returned status 
        may contain a value with more than one of the bits
        specified in the UART1_TRANSFER_STATUS enumeration set.  
        The caller should perform an "AND" with the bit of interest and verify if the
        result is non-zero (as shown in the example) to verify the desired status
        bit.

      @Preconditions
        UART1_Initialize function should have been called 
        before calling this function

      @Param
        None.

      @Returns
        A UART1_TRANSFER_STATUS value describing the current status 
        of the transfer.

      @Example
        Refer to UART1_ReadBuffer and UART1_WriteBuffer for example

     */
    UART1_TRANSFER_STATUS __attribute__((deprecated)) UART1_TransferStatusGet(void);

    /**
      @Summary
        Returns the character in the read sequence at the offset provided, without
        extracting it

      @Description
        This routine returns the character in the read sequence at the offset provided,
        without extracting it
 
      @Param
        None.
    
      @Example 
        <code>
        uint8_t readBuffer[5];
        unsigned int data, numBytes = 0;
        unsigned int readbufferLen = sizeof(readBuffer);
        UART1_Initialize();
    
        while(numBytes < readbufferLen)        
        {   
            UART1_TasksReceive ( );
            //Check for data at a particular place in the buffer
            data = UART1_Peek(3);
            if(data == 5)
            {
                //discard all other data if byte that is wanted is received.    
                //continue other operation
                numBytes += UART1_ReadBuffer ( readBuffer + numBytes , readbufferLen ) ;
            }
            else
            {
                break;
            }
        }
        </code>
 
     */
    uint8_t __attribute__((deprecated)) UART1_Peek(uint16_t offset);

    /**
      @Summary
        Returns the status of the receive buffer

      @Description
        This routine returns if the receive buffer is empty or not.

      @Param
        None.
 
      @Returns
        True if the receive buffer is empty
        False if the receive buffer is not empty
    
      @Example
        <code>
        char                     myBuffer[MY_BUFFER_SIZE];
        unsigned int             numBytes;
        UART1_TRANSFER_STATUS status ;

        // Pre-initialize myBuffer with MY_BUFFER_SIZE bytes of valid data.

        numBytes = 0;
        while( numBytes < MY_BUFFER_SIZE);
        {
            status = UART1_TransferStatusGet ( ) ;
            if (!UART1_ReceiveBufferIsEmpty())
            {
                numBytes += UART1_ReadBuffer( myBuffer + numBytes, MY_BUFFER_SIZE - numBytes )  ;
                if(numBytes < readbufferLen)
                {
                    continue;
                }
                else
                {
                    break;
                }
            }
            else
            {
                continue;
            }

            // Do something else...
        }
        </code>
 
     */
    bool __attribute__((deprecated)) UART1_ReceiveBufferIsEmpty(void);

    /**
      @Summary
        Returns the status of the transmit buffer

      @Description
        This routine returns if the transmit buffer is full or not.

     @Param
        None.
 
     @Returns
        True if the transmit buffer is full
        False if the transmit buffer is not full

     @Example
        Refer to UART1_Initialize() for example.
 
     */
    bool __attribute__((deprecated)) UART1_TransmitBufferIsFull(void);

    /**
      @Summary
        Returns the transmitter and receiver status

      @Description
        This returns the transmitter and receiver status. The returned status may 
        contain a value with more than one of the bits
        specified in the UART1_STATUS enumeration set.  
        The caller should perform an "AND" with the bit of interest and verify if the
        result is non-zero (as shown in the example) to verify the desired status
        bit.

      @Preconditions
        UART1_Initialize function should have been called 
        before calling this function

      @Param
        None.

      @Returns
        A UART1_STATUS value describing the current status 
        of the transfer.

      @Example
        <code>
            while(!(UART1_StatusGet & UART1_TX_COMPLETE ))
            {
               // Wait for the tranmission to complete
            }
        </code>
     */
    uint32_t __attribute__((deprecated)) UART1_StatusGet(void);

    /**
      @Summary
        Allows setting of a the enable bit for the UART1 mode

      @Description
        This routine is used to enable the UART1
  
      @Preconditions
        UART1_Initialize() function should have been 
        called before calling this function.
 
      @Returns
        None

      @Param
        None
  
      @Example
        Refer to UART1_Initialize(); for an example
     */

    void __attribute__((deprecated)) UART1_Enable(void);

    /**
      @Summary
        Allows setting of a the disable bit for the UART1 mode

      @Description
        This routine is used to disable the UART1
  
      @Preconditions
        UART1_Initialize() function should have been 
        called before calling this function.
 
      @Returns
        None

      @Param
        None
  
      @Example
        Refer to UART1_Initialize(); for an example
     */

    void __attribute__((deprecated)) UART1_Disable(void);

    /**
      @Summary
        Returns the number of bytes remaining in the receive buffer

      @Description
        This routine returns the number of bytes remaining in the receive buffer.

      @Param
        None.

      @Returns
        Remaining size of receive buffer.
    
      @Example 
        <code>
        uint8_t readBuffer[MY_BUFFER_SIZE];
        unsigned int size, numBytes = 0;
        UART1_Initialize();

        // Pre-initialize readBuffer with MY_BUFFER_SIZE bytes of valid data.
    
        while (size < MY_BUFFER_SIZE) {
            size = UART1_ReceiveBufferSizeGet();
        }
        numBytes = UART1_ReadBuffer(readBuffer, MY_BUFFER_SIZE);
        </code>
 
     */

    unsigned int __attribute__((deprecated)) UART1_ReceiveBufferSizeGet(void);

    /**
      @Summary
        Returns the number of bytes remaining in the transmit buffer.

      @Description
        This routine returns the number of bytes remaining in the transmit buffer.

     @Param
        None.
 
     @Returns
        Remaining size of transmit buffer.

     @Example
        Refer to UART1_Initialize(); for example.
     */

    unsigned int __attribute__((deprecated)) UART1_TransmitBufferSizeGet(void);

#ifdef __cplusplus  // Provide C++ Compatibility

}

#endif

#endif  // _UART1_H
