hcmusthinhcode2k2/WeatherStation_Thesis/Firmware/RPCLib/MIPS/Core/uart/uart3.c

/**
  UART3 Generated Driver File 

  @Company
    Microchip Technology Inc.

  @File Name
    uart3.c

  @Summary
    This is the generated source file for the UART3 driver using Foundation Services Library

  @Description
    This source file provides APIs for driver for UART3. 

    Generation Information : 
        Product Revision  :  Foundation Services Library - pic24-dspic-pic32mm : v1.26
        Device            :  PIC32MM0256GPM048
    The generated drivers are tested against the following:
        Compiler          :  XC32 1.42
        MPLAB 	          :  MPLAB X 3.45
 */

/*
    (c) 2016 Microchip Technology Inc. and its subsidiaries. You may use this
    software and any derivatives exclusively with Microchip products.

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
    IN NO EVENT WILL MICROCHIP BE LIABLE FOR ANY INDIRECT, SPECIAL, PUNITIVE,
    INCIDENTAL OR CONSEQUENTIAL LOSS, DAMAGE, COST OR EXPENSE OF ANY KIND
    WHATSOEVER RELATED TO THE SOFTWARE, HOWEVER CAUSED, EVEN IF MICROCHIP HAS
    BEEN ADVISED OF THE POSSIBILITY OR THE DAMAGES ARE FORESEEABLE. TO THE
    FULLEST EXTENT ALLOWED BY LAW, MICROCHIP'S TOTAL LIABILITY ON ALL CLAIMS IN
    ANY WAY RELATED TO THIS SOFTWARE WILL NOT EXCEED THE AMOUNT OF FEES, IF ANY,
    THAT YOU HAVE PAID DIRECTLY TO MICROCHIP FOR THIS SOFTWARE.

    MICROCHIP PROVIDES THIS SOFTWARE CONDITIONALLY UPON YOUR ACCEPTANCE OF THESE
    TERMS.
 */

/**
  Section: Included Files
 */
#include <stdbool.h>
#include <stdint.h>
#include "xc.h"
#include "uart3.h"

/**
  Section: Data Type Definitions
 */

/** UART Driver Queue Status

  @Summary
    Defines the object required for the status of the queue.
 */

static uint8_t*volatile rxTail;
static uint8_t * rxHead;
static uint8_t * txTail;
static uint8_t*volatile txHead;
static bool volatile rxOverflowed;

/** UART Driver Queue Length

  @Summary
    Defines the length of the Transmit and Receive Buffers

 */

#define UART3_CONFIG_TX_BYTEQ_LENGTH (254+1)
#define UART3_CONFIG_RX_BYTEQ_LENGTH (254+1)

/** UART Driver Queue

  @Summary
    Defines the Transmit and Receive Buffers

 */

static uint8_t txQueue[UART3_CONFIG_TX_BYTEQ_LENGTH];
static uint8_t rxQueue[UART3_CONFIG_RX_BYTEQ_LENGTH];

void (*UART3_TxDefaultInterruptHandler)(void);
void (*UART3_RxDefaultInterruptHandler)(void);

/**
  Section: Driver Interface
 */


void UART3_Initialize(void)
{
    IEC1bits.U3TXIE=0;
    IEC1bits.U3RXIE=0;

    // STSEL 1; PDSEL 8N; RTSMD disabled; OVFDIS disabled; ACTIVE disabled; RXINV disabled; WAKE disabled; BRGH enabled; IREN disabled; ON enabled; SLPEN disabled; SIDL disabled; ABAUD disabled; LPBACK disabled; UEN TX_RX; CLKSEL SYSCLK; 
    U3MODE=(0x28008& ~(1<<15)); // disabling UART
    // UTXISEL TX_ONE_CHAR; UTXINV disabled; ADDR 0; MASK 0; URXEN disabled; OERR disabled; URXISEL RX_ONE_CHAR; UTXBRK disabled; UTXEN disabled; ADDEN disabled; 
    U3STA=0x0;
    // BaudRate = 115200; Frequency = 24000000 Hz; BRG 51; 
    U3BRG=0x33;

    txHead=txQueue;
    txTail=txQueue;
    rxHead=rxQueue;
    rxTail=rxQueue;

    rxOverflowed=0;

    UART3_SetTxInterruptHandler(UART3_Transmit_ISR);

    UART3_SetRxInterruptHandler(UART3_Receive_ISR);
    IEC1bits.U3RXIE=1;

    //Make sure to set LAT bit corresponding to TxPin as high before UART initialization
    U3STASET=_U3STA_UTXEN_MASK;
    U3MODESET=_U3MODE_ON_MASK; // enabling UART ON bit
    U3STASET=_U3STA_URXEN_MASK;
}

void UART3_Deinitialize(void)
{
    if(U3MODEbits.ON==1)
    {
        IEC1bits.U3TXIE=0;
        IEC1bits.U3RXIE=0;

        // STSEL 1; PDSEL 8N; RTSMD disabled; OVFDIS disabled; ACTIVE disabled; RXINV disabled; WAKE disabled; BRGH enabled; IREN disabled; ON enabled; SLPEN disabled; SIDL disabled; ABAUD disabled; LPBACK disabled; UEN TX_RX; CLKSEL SYSCLK; 
        U3MODE=(0x28008& ~(1<<15)); // disabling UART
        // UTXISEL TX_ONE_CHAR; UTXINV disabled; ADDR 0; MASK 0; URXEN disabled; OERR disabled; URXISEL RX_ONE_CHAR; UTXBRK disabled; UTXEN disabled; ADDEN disabled; 
        U3STA=0x0;
    }
}

/**
    Maintains the driver's transmitter state machine and implements its ISR
 */
void UART3_SetTxInterruptHandler(void* handler)
{
    UART3_TxDefaultInterruptHandler=handler;
}

void __attribute__((vector(_UART3_TX_VECTOR), interrupt(IPL4SOFT))) _UART3_TX(void)
{
    (*UART3_TxDefaultInterruptHandler)();
}

void UART3_Transmit_ISR(void)
{
    if(txHead==txTail)
    {
        IEC1bits.U3TXIE=0;
        return;
    }

    IFS1CLR=1<<_IFS1_U3TXIF_POSITION;

    while(!(U3STAbits.UTXBF==1))
    {
        U3TXREG= *txHead++;

        if(txHead==(txQueue+UART3_CONFIG_TX_BYTEQ_LENGTH))
        {
            txHead=txQueue;
        }

        // Are we empty?
        if(txHead==txTail)
        {
            break;
        }
    }
}

void UART3_SetRxInterruptHandler(void* handler)
{
    UART3_RxDefaultInterruptHandler=handler;
}

void __attribute__((vector(_UART3_RX_VECTOR), interrupt(IPL4SOFT))) _UART3_RX(void)
{
    (*UART3_RxDefaultInterruptHandler)();
}

void UART3_Receive_ISR(void)
{
    while((U3STAbits.URXDA==1))
    {
        *rxTail=U3RXREG;

        // Will the increment not result in a wrap and not result in a pure collision?
        // This is most often condition so check first
        if((rxTail!=(rxQueue+UART3_CONFIG_RX_BYTEQ_LENGTH-1)) &&
                ((rxTail+1)!=rxHead))
        {
            rxTail++;
        }
        else if((rxTail==(rxQueue+UART3_CONFIG_RX_BYTEQ_LENGTH-1)) &&
                (rxHead!=rxQueue))
        {
            // Pure wrap no collision
            rxTail=rxQueue;
        }
        else // must be collision
        {
            rxOverflowed=true;
        }

    }

    IFS1CLR=1<<_IFS1_U3RXIF_POSITION;
}

void __attribute__((vector(_UART3_ERR_VECTOR), interrupt(IPL4SOFT))) _UART3_ERR(void)
{
    if((U3STAbits.OERR==1))
    {
        U3STACLR=_U3STA_OERR_MASK;
    }

    IFS1CLR=1<<_IFS1_U3EIF_POSITION;
}

/**
  Section: UART Driver Client Routines
 */

uint8_t UART3_Read(void)
{
    uint8_t data=0;

    while(rxHead==rxTail)
    {
    }

    data= *rxHead;

    rxHead++;

    if(rxHead==(rxQueue+UART3_CONFIG_RX_BYTEQ_LENGTH))
    {
        rxHead=rxQueue;
    }
    return data;
}

void UART3_Write(uint8_t byte)
{
    while(UART3_IsTxReady()==0)
    {
    }

    *txTail=byte;

    txTail++;

    if(txTail==(txQueue+UART3_CONFIG_TX_BYTEQ_LENGTH))
    {
        txTail=txQueue;
    }

    IEC1bits.U3TXIE=1;
}

bool UART3_IsRxReady(void)
{
    return !(rxHead==rxTail);
}

bool UART3_IsTxReady(void)
{
    uint16_t size;
    uint8_t *snapshot_txHead=(uint8_t*) txHead;

    if(txTail<snapshot_txHead)
    {
        size=(snapshot_txHead-txTail-1);
    }
    else
    {
        size=(UART3_CONFIG_TX_BYTEQ_LENGTH-(txTail-snapshot_txHead)-1);
    }

    return (size!=0);
}

bool UART3_IsTxDone(void)
{
    if(txTail==txHead)
    {
        return (bool) U3STAbits.TRMT;
    }

    return false;
}

void _mon_putc(char c)
{
    while(UART3_IsTxReady()==false)
    {
    }

    UART3_Write(c);
}

/* !!! Deprecated API - This function may not be supported in a future release !!! */
static uint8_t UART3_RxDataAvailable(void)
{
    uint16_t size;
    uint8_t *snapshot_rxTail=(uint8_t*) rxTail;

    if(snapshot_rxTail<rxHead)
    {
        size=(UART3_CONFIG_RX_BYTEQ_LENGTH-(rxHead-snapshot_rxTail));
    }
    else
    {
        size=((snapshot_rxTail-rxHead));
    }

    if(size>0xFF)
    {
        return 0xFF;
    }

    return size;
}

/* !!! Deprecated API - This function may not be supported in a future release !!! */
uint8_t __attribute__((deprecated)) UART3_is_rx_ready(void)
{
    return UART3_RxDataAvailable();
}

/* !!! Deprecated API - This function may not be supported in a future release !!! */
static uint8_t UART3_TxDataAvailable(void)
{
    uint16_t size;
    uint8_t *snapshot_txHead=(uint8_t*) txHead;

    if(txTail<snapshot_txHead)
    {
        size=(snapshot_txHead-txTail-1);
    }
    else
    {
        size=(UART3_CONFIG_TX_BYTEQ_LENGTH-(txTail-snapshot_txHead)-1);
    }

    if(size>0xFF)
    {
        return 0xFF;
    }

    return size;
}

/* !!! Deprecated API - This function may not be supported in a future release !!! */
uint8_t __attribute__((deprecated)) UART3_is_tx_ready(void)
{
    return UART3_TxDataAvailable();
}

/* !!! Deprecated API - This function may not be supported in a future release !!! */
bool __attribute__((deprecated)) UART3_is_tx_done(void)
{
    return UART3_IsTxDone();
}

/* !!! Deprecated API - This function may not be supported in a future release !!! */
unsigned int __attribute__((deprecated)) UART3_ReadBuffer(uint8_t *buffer, unsigned int numbytes)
{
    unsigned int rx_count=UART3_RxDataAvailable();
    unsigned int i;

    if(numbytes<rx_count)
    {
        rx_count=numbytes;
    }

    for(i=0; i<rx_count; i++)
    {
        *buffer++ =UART3_Read();
    }

    return rx_count;
}

/* !!! Deprecated API - This function may not be supported in a future release !!! */
unsigned int __attribute__((deprecated)) UART3_WriteBuffer(uint8_t *buffer, unsigned int numbytes)
{
    unsigned int tx_count=UART3_TxDataAvailable();
    unsigned int i;

    if(numbytes<tx_count)
    {
        tx_count=numbytes;
    }

    for(i=0; i<tx_count; i++)
    {
        UART3_Write(*buffer++);
    }

    return tx_count;
}

/* !!! Deprecated API - This function may not be supported in a future release !!! */
UART3_TRANSFER_STATUS __attribute__((deprecated)) UART3_TransferStatusGet(void)
{
    UART3_TRANSFER_STATUS status=0;
    uint8_t rx_count=UART3_RxDataAvailable();
    uint8_t tx_count=UART3_TxDataAvailable();

    switch(rx_count)
    {
        case 0:
            status|=UART3_TRANSFER_STATUS_RX_EMPTY;
            break;
        case UART3_CONFIG_RX_BYTEQ_LENGTH:
            status|=UART3_TRANSFER_STATUS_RX_FULL;
            break;
        default:
            status|=UART3_TRANSFER_STATUS_RX_DATA_PRESENT;
            break;
    }

    switch(tx_count)
    {
        case 0:
            status|=UART3_TRANSFER_STATUS_TX_FULL;
            break;
        case UART3_CONFIG_RX_BYTEQ_LENGTH:
            status|=UART3_TRANSFER_STATUS_TX_EMPTY;
            break;
        default:
            break;
    }

    return status;
}

/* !!! Deprecated API - This function may not be supported in a future release !!! */
uint8_t __attribute__((deprecated)) UART3_Peek(uint16_t offset)
{
    uint8_t *peek=rxHead+offset;

    while(peek>(rxQueue+UART3_CONFIG_RX_BYTEQ_LENGTH))
    {
        peek-=UART3_CONFIG_RX_BYTEQ_LENGTH;
    }

    return *peek;
}

/* !!! Deprecated API - This function may not be supported in a future release !!! */
bool __attribute__((deprecated)) UART3_ReceiveBufferIsEmpty(void)
{
    return (UART3_RxDataAvailable()==0);
}

/* !!! Deprecated API - This function may not be supported in a future release !!! */
bool __attribute__((deprecated)) UART3_TransmitBufferIsFull(void)
{
    return (UART3_TxDataAvailable()==0);
}

/* !!! Deprecated API - This function may not be supported in a future release !!! */
UART3_STATUS __attribute__((deprecated)) UART3_StatusGet(void)
{
    return U3STA;
}
