hcmusthinhcode2k2/WeatherStation_Thesis/Firmware/RPCLib/MIPS/Core/ext_int.h

/**
  EXT_INT Generated Driver API Header File 

  @Company:
    Microchip Technology Inc.

  @File Name:
    ext_int.h

  @Summary:
    This is the generated header file for the EXT_INT driver using PIC24 / dsPIC33 / PIC32MM MCUs

  @Description:
    This header file provides APIs for driver for EXT_INT. 
    Generation Information : 
        Product Revision  :  PIC24 / dsPIC33 / PIC32MM MCUs - 1.170.0
        Device            :  PIC32MM0256GPM048
    The generated drivers are tested against the following:
        Compiler          :  XC32 v2.50
        MPLAB             :  MPLAB X v5.45
*/

/*
    (c) 2020 Microchip Technology Inc. and its subsidiaries. You may use this
    software and any derivatives exclusively with Microchip products.

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
    IN NO EVENT WILL MICROCHIP BE LIABLE FOR ANY INDIRECT, SPECIAL, PUNITIVE,
    INCIDENTAL OR CONSEQUENTIAL LOSS, DAMAGE, COST OR EXPENSE OF ANY KIND
    WHATSOEVER RELATED TO THE SOFTWARE, HOWEVER CAUSED, EVEN IF MICROCHIP HAS
    BEEN ADVISED OF THE POSSIBILITY OR THE DAMAGES ARE FORESEEABLE. TO THE
    FULLEST EXTENT ALLOWED BY LAW, MICROCHIP'S TOTAL LIABILITY ON ALL CLAIMS IN
    ANY WAY RELATED TO THIS SOFTWARE WILL NOT EXCEED THE AMOUNT OF FEES, IF ANY,
    THAT YOU HAVE PAID DIRECTLY TO MICROCHIP FOR THIS SOFTWARE.

    MICROCHIP PROVIDES THIS SOFTWARE CONDITIONALLY UPON YOUR ACCEPTANCE OF THESE
    TERMS.
*/

#ifndef _EXT_INT_H
#define _EXT_INT_H

/**
    Section: Includes
*/

#include <xc.h>

// Provide C++ Compatibility
#ifdef __cplusplus  

extern "C" {

#endif

/**
    Section: Macros
*/
/**
  @Summary
    Clears the interrupt flag for INT4

  @Description
    This routine clears the interrupt flag for the external interrupt, INT4.
 
  @Preconditions
    None.

  @Returns
    None.

  @Param
    None.

  @Example
    <code>
    void __attribute__ ( ( interrupt, no_auto_psv ) ) _EXTERNAL_4(void)
    {
        // User Area Begin->code: External 4

        // User Area End->code: External 4
        EX_INT4_InterruptFlagClear();
    }
    </code>

*/
#define EX_INT4_InterruptFlagClear()       IFS0CLR= 1 << _IFS0_INT4IF_POSITION
/**
  @Summary
    Clears the interrupt enable for INT4

  @Description
    This routine clears the interrupt enable for the external interrupt, INT4.
    After calling this routine, external interrupts on this pin will not be serviced by the 
    interrupt handler, _EXTERNAL_4.

  @Preconditions
    None.

  @Returns
    None.

  @Param
    None.

  @Example
    Changing the external interrupt edge detect from negative to positive
    <code>
    // clear the interrupt enable
    EX_INT4_InterruptDisable();
    // change the edge
    EX_INT4_PositiveEdgeSet();
    // clear the interrupt flag and re-enable the interrupt
    EX_INT4_InterruptFlagClear();
    EX_INT4_InterruptEnable();
    </code>

*/
#define EX_INT4_InterruptDisable()     (IEC0bits.INT4IE = 0)
/**
  @Summary
    Clears the interrupt enable for INT4

  @Description
    This routine clears the interrupt enable for the external interrupt, INT4.
    After calling this routine, external interrupts on this pin will be serviced by the 
    interrupt handler, _EXTERNAL_4.
 
  @Preconditions
    None.

  @Returns
    None.

  @Param
    None.

  @Example
    Setting the external interrupt to handle positive edge interrupts
    <code>
    // set the edge
    EX_INT4_PositiveEdgeSet();
    // clear the interrupt flag and enable the interrupt
    EX_INT4_InterruptFlagClear();
    EX_INT4_InterruptEnable();
    </code>

*/
#define EX_INT4_InterruptEnable()       (IEC0bits.INT4IE = 1)
/**
  @Summary
    Sets the edge detect of the external interrupt to negative edge.

  @Description
    This routine set the edge detect of the extern interrupt to negative edge.  
    After this routine is called the interrupt flag will be set when the external 
    interrupt pins level transitions from a high to low level.
 
  @Preconditions
    None.

  @Returns
    None.

  @Param
    None.

  @Example
    Setting the external interrupt to handle negative edge interrupts
    <code>
    // set the edge
    EX_INT4_NegativeEdgeSet();
    // clear the interrupt flag and enable the interrupt
    EX_INT4_InterruptFlagClear();
    EX_INT4_InterruptEnable();
    </code>

*/
#define EX_INT4_NegativeEdgeSet()          (INTCONCLR = _INTCON_INT4EP_MASK)
/**
  @Summary
    Sets the edge detect of the external interrupt to positive edge.

  @Description
    This routine set the edge detect of the extern interrupt to positive edge.  
    After this routine is called the interrupt flag will be set when the external 
    interrupt pins level transitions from a low to high level.
 
  @Preconditions
    None.

  @Returns
    None.

  @Param
    None.

  @Example
    Setting the external interrupt to handle positive edge interrupts
    <code>
    // set the edge
    EX_INT4_PositiveEdgeSet();
    // clear the interrupt flag and enable the interrupt
    EX_INT4_InterruptFlagClear();
    EX_INT4_InterruptEnable();
    </code>

*/
#define EX_INT4_PositiveEdgeSet()          (INTCONSET = _INTCON_INT4EP_MASK)

/**
  @Summary
    Callback for EX_INT4.

  @Description
    This routine is callback for EX_INT4

  @Param
    None.

  @Returns
    None
 
  @Example 
	<code>
    EX_INT4_CallBack();
    </code>
*/
void EX_INT4_CallBack(void);


/**
    Section: External Interrupt Initializers
 */
/**
  @Summary
    Initializes the external interrupt pins

  @Description
    This routine initializes the EXT_INT driver to detect the configured edge, clear
    the interrupt flag and enable the interrupt.

    The following external interrupts will be initialized:
    INT4 - EX_INT4
 
  @Preconditions
    None.

  @Returns
    None.

  @Param
    None.

  @Example
    Initialize the external interrupt pins
    <code>
    EXT_INT_Initialize();
    </code>

*/
void EXT_INT_Initialize(void);

// Provide C++ Compatibility
#ifdef __cplusplus  

}

#endif
#endif
