hcmusthinhcode2k2/WeatherStation_Thesis/Firmware/RPCLib/MIPS/Core/rtcc.c

/**
  RTCC Generated Driver API Header File

  @Company:
    Microchip Technology Inc.

  @File Name:
    rtcc.c

  @Summary:
    This is the generated header file for the RTCC driver using PIC24 / dsPIC33 / PIC32MM MCUs

  @Description:
    This header file provides APIs for driver for RTCC.
    Generation Information :
        Product Revision  :  PIC24 / dsPIC33 / PIC32MM MCUs - 1.170.0
        Device            :  PIC32MM0256GPM048
    The generated drivers are tested against the following:
        Compiler          :  XC32 v2.50
        MPLAB 	          :  MPLAB X v5.45
*/

/*
    (c) 2020 Microchip Technology Inc. and its subsidiaries. You may use this
    software and any derivatives exclusively with Microchip products.

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
    IN NO EVENT WILL MICROCHIP BE LIABLE FOR ANY INDIRECT, SPECIAL, PUNITIVE,
    INCIDENTAL OR CONSEQUENTIAL LOSS, DAMAGE, COST OR EXPENSE OF ANY KIND
    WHATSOEVER RELATED TO THE SOFTWARE, HOWEVER CAUSED, EVEN IF MICROCHIP HAS
    BEEN ADVISED OF THE POSSIBILITY OR THE DAMAGES ARE FORESEEABLE. TO THE
    FULLEST EXTENT ALLOWED BY LAW, MICROCHIP'S TOTAL LIABILITY ON ALL CLAIMS IN
    ANY WAY RELATED TO THIS SOFTWARE WILL NOT EXCEED THE AMOUNT OF FEES, IF ANY,
    THAT YOU HAVE PAID DIRECTLY TO MICROCHIP FOR THIS SOFTWARE.

    MICROCHIP PROVIDES THIS SOFTWARE CONDITIONALLY UPON YOUR ACCEPTANCE OF THESE
    TERMS.
*/


/**
 Section: Included Files
*/

#include "rtcc.h"
#include "system.h"

/**
  Section: Static function
*/


static bool rtccTimeInitialized;
static bool RTCCTimeInitialized(void);
static uint8_t ConvertHexToBCD(uint8_t hexvalue);
static uint8_t ConvertBCDToHex(uint8_t bcdvalue);

/**
   Section: Driver Interface Function Definitions
*/

void RTCC_Initialize(void)
{
  
   SYSTEM_RegUnlock();
   RTCCON1CLR = (1 << _RTCCON1_WRLOCK_POSITION);
   RTCCON1CLR = (1 << _RTCCON1_ON_POSITION);
     
   if(!RTCCTimeInitialized())
   {
       // set 2024-05-11 12-45-38
       RTCDATE = 0x24051106; // Year/Month/Date/Wday
       RTCTIME = 0x12453800; //  hours/minutes/seconds
       
   }
       // ON enabled; OUTSEL Seconds Clock; WRLOCK disabled; AMASK Every Half Second; ALMRPT 0; RTCOE disabled; CHIME disabled; ALRMEN disabled; 
       RTCCON1 = 0x8010;
   
       // DIV 16383; CLKSEL SOSC; FDIV 0; 
       RTCCON2 = 0x3FFF0000;

   // Enable RTCC 
   RTCCON1SET = (1 << _RTCCON1_ON_POSITION);
   RTCCON1SET = (1 << _RTCCON1_WRLOCK_POSITION);
   SYSTEM_RegLock();

}

bool RTCC_TimeGet(struct tm *currentTime)
{
    uint32_t register_value;
    if(RTCSTATbits.SYNC){
        return false;
    }
     
    register_value = RTCDATE;
    currentTime->tm_year = ConvertBCDToHex((register_value & 0xFF000000) >> 24);
    currentTime->tm_mon = ConvertBCDToHex((register_value & 0xFF0000) >> 16);
    currentTime->tm_mday = ConvertBCDToHex((register_value & 0xFF00) >> 8);
    currentTime->tm_wday = ConvertBCDToHex(register_value & 0xF);
    
    register_value = RTCTIME;
    currentTime->tm_hour = ConvertBCDToHex((register_value & 0xFF000000) >> 24);
    currentTime->tm_min = ConvertBCDToHex((register_value & 0xFF0000) >> 16);
    currentTime->tm_sec = ConvertBCDToHex((register_value & 0xFF00) >> 8);

    return true;
}

void RTCC_TimeSet(struct tm *initialTime)
{
   SYSTEM_RegUnlock();
   RTCCON1CLR = (1 << _RTCCON1_WRLOCK_POSITION);
   RTCCON1CLR = (1 << _RTCCON1_ON_POSITION);
  

   // set RTCC initial time
   RTCDATE = (ConvertHexToBCD(initialTime->tm_year) << 24) | (ConvertHexToBCD(initialTime->tm_mon) << 16 ) | (ConvertHexToBCD(initialTime->tm_mday) << 8) | ConvertHexToBCD(initialTime->tm_wday) ; // YEAR/MONTH-1/DAY-1/WEEKDAY
   RTCTIME = (ConvertHexToBCD(initialTime->tm_hour) << 24) | (ConvertHexToBCD(initialTime->tm_min) << 16 ) | (ConvertHexToBCD(initialTime->tm_sec) << 8) ; // HOURS/MINUTES/SECOND
          
   // Enable RTCC 
   RTCCON1SET = (1 << _RTCCON1_ON_POSITION);
    
    // SET WRLOCK
   RTCCON1SET = (1 << _RTCCON1_WRLOCK_POSITION);
   SYSTEM_RegLock();

}

bool RTCC_BCDTimeGet(bcdTime_t *currentTime)
{
    uint32_t register_value;
    if(RTCSTATbits.SYNC){
        return false;
    }
    
    register_value = RTCDATE;
    currentTime->tm_year = (register_value & 0xFF000000) >> 24;
    currentTime->tm_mon = (register_value & 0xFF0000) >> 16;
    currentTime->tm_mday = (register_value & 0xFF00) >> 8;
    currentTime->tm_wday = (register_value & 0xF);
    
    register_value = RTCTIME;
    currentTime->tm_hour = (register_value & 0xFF000000) >> 24;
    currentTime->tm_min = (register_value & 0xFF0000) >> 16;
    currentTime->tm_sec = (register_value & 0xFF00) >> 8;
    
    return true;
}

void RTCC_BCDTimeSet(bcdTime_t *initialTime)
{
   SYSTEM_RegUnlock();
   RTCCON1CLR = (1 << _RTCCON1_WRLOCK_POSITION);
   RTCCON1CLR = (1 << _RTCCON1_ON_POSITION);

   // set RTCC initial time
   RTCDATE = (initialTime->tm_year << 24) | (initialTime->tm_mon << 16 ) | (initialTime->tm_mday << 8) | (initialTime->tm_wday) ; // YEAR/MONTH-1/DAY-1/WEEKDAY
   RTCTIME = (initialTime->tm_hour << 24) | (initialTime->tm_min << 16 ) | (initialTime->tm_sec << 8) ; // HOURS/MINUTES/SECOND
              
   // Enable RTCC  
   RTCCON1SET = (1 << _RTCCON1_ON_POSITION);
   
   // SET WRLOCK 
   RTCCON1SET = (1 << _RTCCON1_WRLOCK_POSITION);
   SYSTEM_RegLock();

}

/**
 This function implements RTCC_TimeReset.This function is used to
 used by application to reset the RTCC value and reinitialize RTCC value.
*/
void RTCC_TimeReset(bool reset)
{
    rtccTimeInitialized = reset;
}

static bool RTCCTimeInitialized(void)
{
    return(rtccTimeInitialized);
}

static uint8_t ConvertHexToBCD(uint8_t hexvalue)
{
    uint8_t bcdvalue;
    bcdvalue = (hexvalue / 10) << 4;
    bcdvalue = bcdvalue | (hexvalue % 10);
    return (bcdvalue);
}

static uint8_t ConvertBCDToHex(uint8_t bcdvalue)
{
    uint8_t hexvalue;
    hexvalue = (((bcdvalue & 0xF0) >> 4)* 10) + (bcdvalue & 0x0F);
    return hexvalue;
}

void __attribute__ ((weak)) RTCC_CallBack(void)
{
    // Add your custom callback code here
}

/* Function:
    bool RTCC_Task(void)

  Summary:
    Status function which returns the RTCC interrupt flag status

  Description:
    This is the status function for the RTCC peripheral. 
*/
bool RTCC_Task(void)
{
    bool status;
    status = IFS1bits.RTCCIF;
    if( IFS1bits.RTCCIF)
    {
		// RTCC callback function 
		RTCC_CallBack();
        
		IFS1CLR= 1 << _IFS1_RTCCIF_POSITION;
    }
    return status;
}
/**
 End of File
*/
