hcmusthinhcode2k2/WeatherStation_Thesis/Firmware/RPCLib/MIPS/Core/system.c

/**
  @Generated PIC24 / dsPIC33 / PIC32MM MCUs Source File

  @Company:
    Microchip Technology Inc.

  @File Name:
    system.h

  @Summary:
    This is the sysetm.h file generated using PIC24 / dsPIC33 / PIC32MM MCUs

  @Description:
    This header file provides implementations for driver APIs for all modules selected in the GUI.
    Generation Information :
        Product Revision  :  PIC24 / dsPIC33 / PIC32MM MCUs - 1.170.0
        Device            :  PIC32MM0256GPM048
    The generated drivers are tested against the following:
        Compiler          :  XC16 v1.61
        MPLAB             :  MPLAB X v5.45
 */

/*
    (c) 2020 Microchip Technology Inc. and its subsidiaries. You may use this
    software and any derivatives exclusively with Microchip products.

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
    IN NO EVENT WILL MICROCHIP BE LIABLE FOR ANY INDIRECT, SPECIAL, PUNITIVE,
    INCIDENTAL OR CONSEQUENTIAL LOSS, DAMAGE, COST OR EXPENSE OF ANY KIND
    WHATSOEVER RELATED TO THE SOFTWARE, HOWEVER CAUSED, EVEN IF MICROCHIP HAS
    BEEN ADVISED OF THE POSSIBILITY OR THE DAMAGES ARE FORESEEABLE. TO THE
    FULLEST EXTENT ALLOWED BY LAW, MICROCHIP'S TOTAL LIABILITY ON ALL CLAIMS IN
    ANY WAY RELATED TO THIS SOFTWARE WILL NOT EXCEED THE AMOUNT OF FEES, IF ANY,
    THAT YOU HAVE PAID DIRECTLY TO MICROCHIP FOR THIS SOFTWARE.

    MICROCHIP PROVIDES THIS SOFTWARE CONDITIONALLY UPON YOUR ACCEPTANCE OF THESE
    TERMS.
 */

// Configuration bits: selected in the GUI

// FDEVOPT
#pragma config SOSCHP = OFF    //Secondary Oscillator High Power Enable bit->SOSC oprerates in normal power mode.
#pragma config ALTI2C = OFF    //Alternate I2C1 Pins Location Enable bit->Primary I2C1 pins are used
#pragma config FUSBIDIO = OFF    //USBID pin control->USBID pin is controlled by the USB module
#pragma config FVBUSIO = OFF    //VBUS Pin Control->VBUS pin is controlled by the USB module

// FICD
#pragma config JTAGEN = OFF    //JTAG Enable bit->JTAG is disabled
#pragma config ICS = PGx1    //ICE/ICD Communication Channel Selection bits->Communicate on PGEC1/PGED1

// FPOR
#pragma config BOREN = BOR3    //Brown-out Reset Enable bits->Brown-out Reset enabled in hardware; SBOREN bit disabled
#pragma config RETVR = OFF    //Retention Voltage Regulator Enable bit->Retention regulator is disabled
#pragma config LPBOREN = ON    //Downside Voltage Protection Enable bit->Low power BOR is enabled, when main BOR is disabled

// FWDT
#pragma config SWDTPS = PS1048576    //Sleep Mode Watchdog Timer Postscale Selection bits->1:1048576
#pragma config FWDTWINSZ = PS25_0    //Watchdog Timer Window Size bits->Watchdog timer window size is 25%
#pragma config WINDIS = OFF    //Windowed Watchdog Timer Disable bit->Watchdog timer is in non-window mode
#pragma config RWDTPS = PS8192    //Run Mode Watchdog Timer Postscale Selection bits->1:8192
#pragma config RCLKSEL = LPRC    //Run Mode Watchdog Timer Clock Source Selection bits->Clock source is LPRC (same as for sleep mode)
#pragma config FWDTEN = ON    //Watchdog Timer Enable bit->WDT is enabled

// FOSCSEL
#pragma config FNOSC = FRCDIV    //Oscillator Selection bits->FRCDIV
#pragma config PLLSRC = FRC    //System PLL Input Clock Selection bit->FRC oscillator is selected as PLL reference input on device reset
#pragma config SOSCEN = ON    //Secondary Oscillator Enable bit->Secondary oscillator is enabled
#pragma config IESO = ON    //Two Speed Startup Enable bit->Two speed startup is enabled
#pragma config POSCMOD = OFF    //Primary Oscillator Selection bit->Primary oscillator is disabled
#pragma config OSCIOFNC = OFF    //System Clock on CLKO Pin Enable bit->OSCO pin operates as a normal I/O
#pragma config SOSCSEL = OFF    //Secondary Oscillator External Clock Enable bit->SOSC pins configured for Crystal mode
#pragma config FCKSM = CSECMD    //Clock Switching and Fail-Safe Clock Monitor Enable bits->Clock switching is enabled; Fail-safe clock monitor is disabled

// FSEC
#pragma config CP = ON    //Code Protection Enable bit->Code protection is enabled

#include "pin_manager.h"
#include "clock.h"
#include "system.h"
#include "usb/usb.h"
#include "drivers/spi_master.h"
#include "i2c1.h"
#include "tmr2.h"
#include "ext_int.h"
#include "adc1.h"
#include "uart1.h"
#include "coretimer.h"
#include "spi2_driver.h"
#include "tmr1.h"
#include "uart3.h"
#include "interrupt_manager.h"
#include "exceptions.h"
#include "uart2.h"
#include "rtcc.h"

uint32_t system_task_count;

void SYSTEM_Initialize(void)
{
    system_task_count=0;
    PIN_MANAGER_Initialize();
    CLOCK_Initialize();
    INTERRUPT_Initialize();
    CORETIMER_Initialize();
    //USBDeviceInit();
    UART3_Initialize();
    ADC1_Initialize();
    UART1_Initialize();
    TMR2_Initialize();
    EXT_INT_Initialize();
    UART2_Initialize();
    I2C1_Initialize();
    TMR1_Initialize();
    RTCC_Initialize();
    INTERRUPT_GlobalEnable();
}

void SYSTEM_SleepControl(void)
{
    if(system_task_count==0)
    {
        if(USBIsDeviceSuspended())
            Sleep();
    }
}

/**
 End of File
 */
