hcmusthinhcode2k2/WeatherStation_Thesis/Firmware/RPCLib/Boards/ARDI/APP.X/Cfg/Project_Cfg.h

#ifndef PROJECT_CFG_H
#define PROJECT_CFG_H
/* ******************************************************* C STANDARD LIBRARY */
#ifndef __LANGUAGE_ASSEMBLY__
#include <stdio.h>
#include <stdint.h>
#include <string.h>
#include <stdbool.h>
#include <string.h>
#endif

/* ************************************************************** MCC LIBRARY */
#include <xc.h>

#ifndef __LANGUAGE_ASSEMBLY__
#include "adc1.h"
#include "i2c1.h"
#include "i2c2.h"
#include "spi2_driver.h"
#include "drivers/spi_master.h"
#include "clock.h"
#include "coretimer.h"
#include "exceptions.h"
#include "interrupt_manager.h"
#include "pin_manager.h"
#include "system.h"
#include "uart2.h"
#include "uart3.h"
#include "usb/usb.h"
#include "usb/usb_ch9.h"
#include "usb/usb_common.h"
#include "usb/usb_device.h"
#include "watchdog.h"
#endif
/* *********************************************************** RPC LIB CONFIG */
// SST25xx Cfg
#define USE_SST25PF040C
// TelitAtCmd Cfg
#define ATCMD_BUFFER_SIZE   512
// TelitPwrCtrl Cfg
//#define USE_TELITPWRCTRL_DEBUG
// TelitAtCMD Cfg
//#define USE_ATCMD_DEBUG
/* ************************************************************ COMMON MACROS */
// Global interrupt
#define Disable_Global_Interrupt()      __builtin_disable_interrupts()
#define Enable_Global_Interrupt()       __builtin_enable_interrupts()
// Peripheral interrupt
#define Disable_Peripheral_Interrupt()  // Not implemented in PIC32
#define Enable_Peripheral_Interrupt()   // Not implemented in PIC32
// Core timer interrupt
#define Disable_Coretimer_Interrupt()   (IEC0CLR=_IEC0_CTIE_MASK)
#define Enable_Coretimer_Interrupt()    (IEC0SET=_IEC0_CTIE_MASK)
#define Clear_Coretimer_Interrupt()     (IFS0CLR=_IFS0_CTIF_MASK)

#endif
