hcmusthinhcode2k2/WeatherStation_Thesis/Firmware/RPCLib/MIPS/System/Gpio.h

#ifndef GPIO_H
#define GPIO_H

#include "Common/LibDef.h"
#include "Project_Cfg.h"

#define GPIO_MCU "PIC32MM"

#define HIGH    1
#define LOW     0
#define TOGGLE  2
#define INPUT   1
#define OUTPUT  0
#define PULLENA 1
#define PULLDIS 0
#define ANALOG  1
#define DIGITAL 0

typedef enum {
    PIN_A0 = 0,
    PIN_A1,
    PIN_A2,
    PIN_A3,
    PIN_A4,
    PIN_A5,
    PIN_A6,
    PIN_A7,
    PIN_A8,
    PIN_A9,
    PIN_A10,
    PIN_A11,
    PIN_A12,
    PIN_A13,
    PIN_A14,
    PIN_A15,

    PIN_B0,
    PIN_B1,
    PIN_B2,
    PIN_B3,
    PIN_B4,
    PIN_B5,
    PIN_B6,
    PIN_B7,
    PIN_B8,
    PIN_B9,
    PIN_B10,
    PIN_B11,
    PIN_B12,
    PIN_B13,
    PIN_B14,
    PIN_B15,

    PIN_C0,
    PIN_C1,
    PIN_C2,
    PIN_C3,
    PIN_C4,
    PIN_C5,
    PIN_C6,
    PIN_C7,
    PIN_C8,
    PIN_C9,
    PIN_C10,
    PIN_C11,
    PIN_C12,
    PIN_C13,
    PIN_C14,
    PIN_C15,

    PIN_D0,
    PIN_D1,
    PIN_D2,
    PIN_D3,
    PIN_D4,
    NOT_USE
} gpio_pin_t;

bool Gpio_Get(volatile uint32_t *baseReg, gpio_pin_t pin);
void Gpio_Set(volatile uint32_t *baseReg, gpio_pin_t pin, uint8_t val);
void Gpio_GetPinName(char *pStr, gpio_pin_t pin);

#define Gpio_SetAnalogInputOn(pin)  Gpio_Set(&ANSELA, (gpio_pin_t)pin, ANALOG)
#define Gpio_SetAnalogInputOff(pin) Gpio_Set(&ANSELA, (gpio_pin_t)pin, DIGITAL)
#define Gpio_SetDigitalInput(pin)   Gpio_Set(&TRISA, (gpio_pin_t)pin, INPUT)
#define Gpio_SetDigitalOutput(pin)  Gpio_Set(&TRISA, (gpio_pin_t)pin, OUTPUT)
#define Gpio_PullupOn(pin)          Gpio_Set(&CNPUA, (gpio_pin_t)pin, PULLENA)
#define Gpio_PullupOff(pin)         Gpio_Set(&CNPUA, (gpio_pin_t)pin, PULLDIS)
#define Gpio_PulldownOn(pin)        Gpio_Set(&CNPDA, (gpio_pin_t)pin, PULLENA)
#define Gpio_PulldownOff(pin)       Gpio_Set(&CNPDA, (gpio_pin_t)pin, PULLDIS)
#define Gpio_GetState(pin)          Gpio_Get(&PORTA, (gpio_pin_t)pin)
#define Gpio_SetState(pin, stt)     Gpio_Set(&LATA, (gpio_pin_t)pin, stt)
#define Gpio_SetHigh(pin)           Gpio_Set(&LATA, (gpio_pin_t)pin, HIGH)
#define Gpio_SetLow(pin)            Gpio_Set(&LATA, (gpio_pin_t)pin, LOW)
#define Gpio_Toggle(pin)            Gpio_Set(&LATA, (gpio_pin_t)pin, TOGGLE)

#endif
